efabless/caravel_board/hardware/nucleo/caravel_nucleo/docs/Caravel+Nucleo Board.pdf

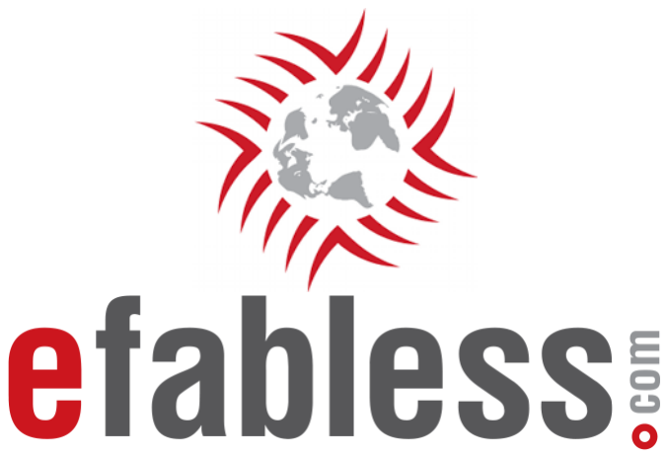
[picture p19: figure]

# Caravel + Nucleo Board

# Specifications

## The board required features:

## - To be physically compatible to act as a hat to the ST Nucleo board using the ST morpho connectors (plug-in). This would provide test setups for characterizing IOs configuration using the Nucleo board

## - Includes programmable power supply on board to test the Caravel chip at a range of power supplies

## - The programmable power supply is programmed with SPI/I

2C

## - It can function as a stand-alone Caravel evaluation board similar to the Caravel V4 evaluation board system

## - The reset could be programmed and not only activated with the push-button

# Programmable Power Supply

## - A programmable power supply is required to test the chip with non-nominal supplies

## - The required ranges are from 1.4V to 2.2V for V1.8 and 3V to 3.6V for V3.3

## - Adjustable dual LDO (MIC2211) is capable of suppling from 1.25V to 5V at 150mA

for Vout1 and at 300mA for Vout2

## - A digital potentiometer (D-POT) MCP4661 could be used with R network to dynamically tune the voltage outputs of the LDO using I

## 2C interface

## - D-POT (10 kΩ device) range to be used in the calculations is from 0 kΩ to 7 kΩ, since its maximum resistance range at temperature corners is 8 kΩ and 12 kΩ

## - MCP4661 has 257 taps

N =

RMAX

RTOT

∗ 256 = 179.2 ≈ 179

[1]: https://www.ti.com/lit/ug/tidu950/tidu950.pdf?ts=1661679201370&ref_url=https%253A%252F%252Fwww.google.com%252F

# Resistance Calculations

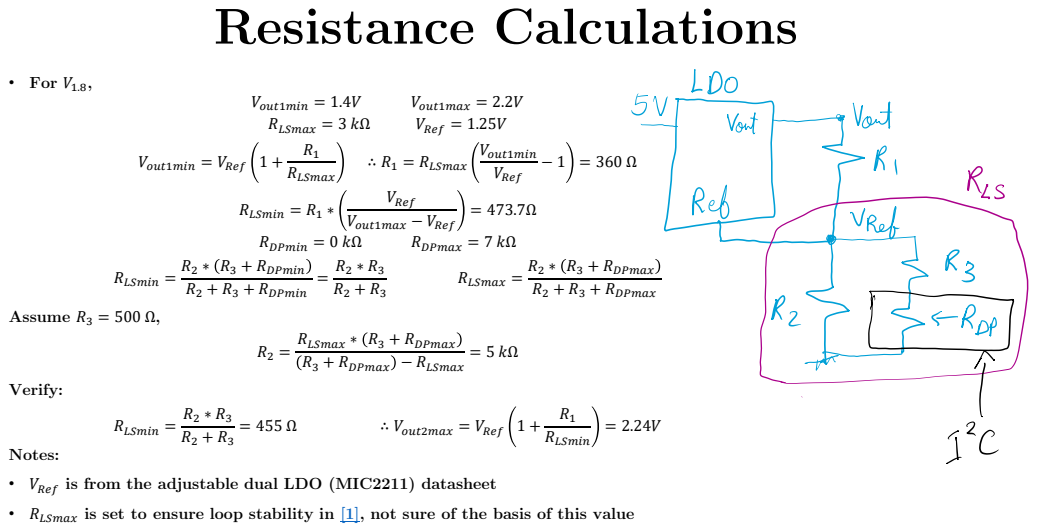
[picture p20: page 4]
• For V1.8,; Vout1min = 1.4V; Vout1max = 2.2V; RLSmax = 3 kΩ; VRef = 1.25V; Vout1min = VRef 1 +; RLSmax; ∴ R1 = RLSmax; Vout1min; VRef; RLSmin = R1 ∗; Vout1max − VRef; RDPmin = 0 kΩ; RDPmax = 7 kΩ; RLSmin =; R2 ∗ R3 + RDPmin; R2 + R3 + RDPmin; RLSmax =; R2 ∗ R3 + RDPmax; R2 + R3 + RDPmax; Assume R3 = 500 Ω,; RLSmax ∗ R3 + RDPmax; R3 + RDPmax − RLSmax; Verify:; ∴ Vout2max = VRef 1 +; RLSmin

Notes:
• VRef is from the adjustable dual LDO (MIC2211) datasheet

• RLSmax is set to ensure loop stability in [1], not sure of the basis of this value

# Resistance Calculations

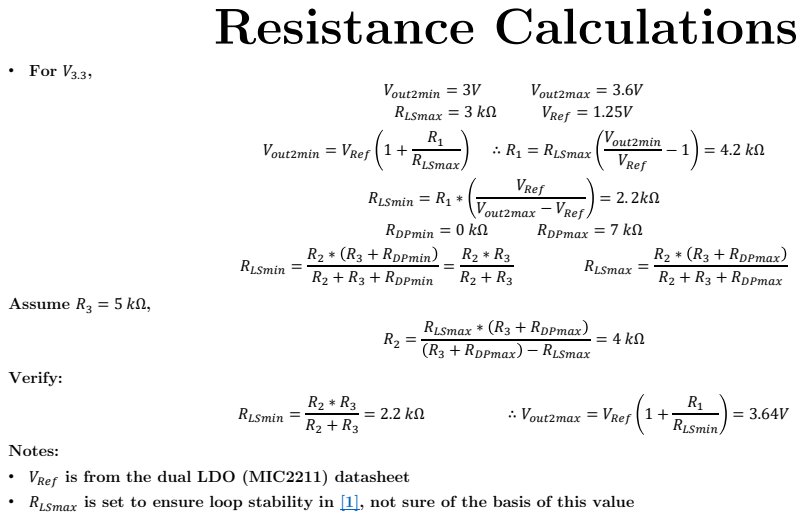
[picture p21: page 5]
• For V3.3,; Vout2min = 3V; Vout2max = 3.6V; RLSmax = 3 kΩ; VRef = 1.25V; Vout2min = VRef 1 +; RLSmax; ∴ R1 = RLSmax; Vout2min; VRef; RLSmin = R1 ∗; Vout2max − VRef; RDPmin = 0 kΩ; RDPmax = 7 kΩ; RLSmin =; R2 ∗ R3 + RDPmin; R2 + R3 + RDPmin; RLSmax =; R2 ∗ R3 + RDPmax; R2 + R3 + RDPmax; Assume R3 = 5 kΩ,; RLSmax ∗ R3 + RDPmax; R3 + RDPmax − RLSmax; Verify:; ∴ Vout2max = VRef 1 +; RLSmin

Notes:
• VRef is from the dual LDO (MIC2211) datasheet
• RLSmax is set to ensure loop stability in [1], not sure of the basis of this value

# Resistors

Output | Resistor | Computed Value | Size 0805 1%
Vout1 | R1 | 360 Ω | 360 Ω
| R2 | 5 kΩ | 4.99 kΩ
| R3 | 500 Ω | 499 Ω
Vout2 | R1 | 4.2 kΩ | 4.22 kΩ
| R2 | 4 kΩ | 4.02 kΩ
| R3 | 5 kΩ | 4.99 kΩ

Note:

- MIC2211 datasheet recommends the resistor values should be between 100kΩ and 500kΩ to prevent compromising the low quiescent current performance. This can’t be achieved with the RLSmax assumption

# Nominal Supplies Code

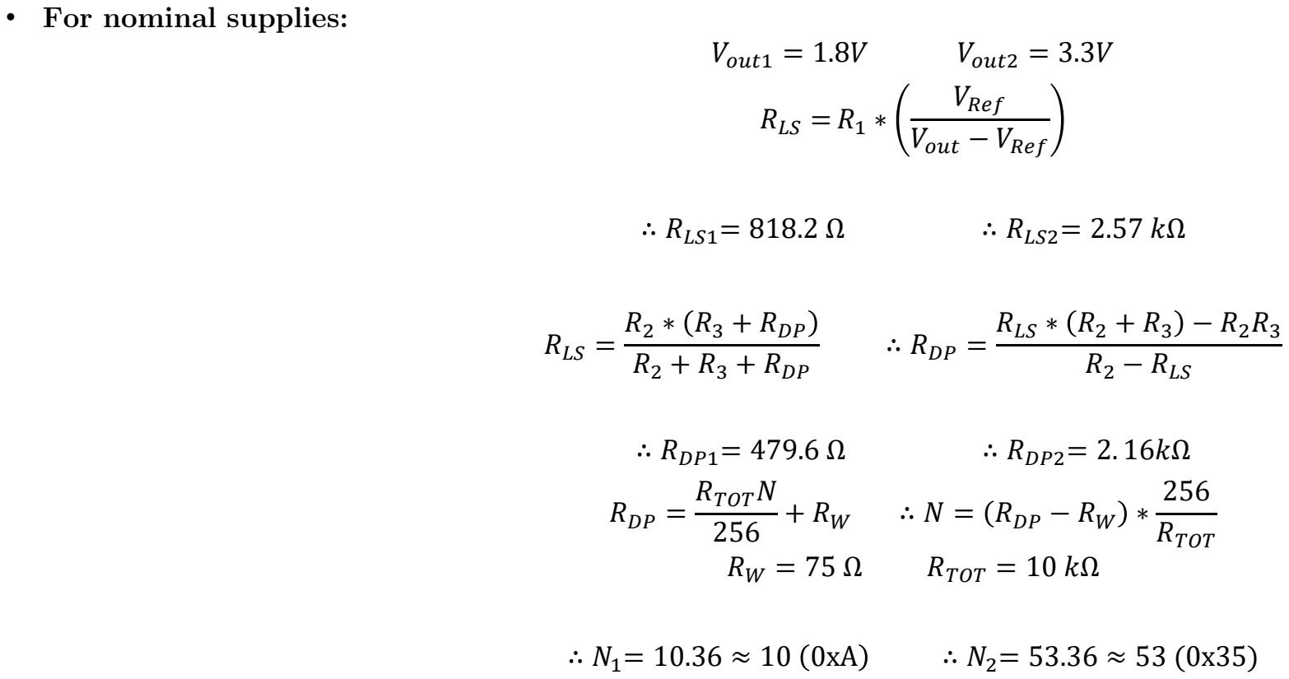
[picture p22: figure]
• For nominal supplies:; Vout1 = 1.8V; Vout2 = 3.3V; RLS = R1 ∗; VRef; Vout − VRef; ∴ RLS1= 818.2 Ω; ∴ RLS2= 2.57 kΩ; RLS =; R2 ∗ R3 + RDP R2 + R3 + RDP; ∴ RDP =; RLS ∗ R2 + R3 − R2R3 R2 − RLS; ∴ RDP1= 479.6 Ω; ∴ RDP2= 2. 16kΩ; RDP =; RTOTN; ∴ N = RDP − RW ∗; RTOT; RTOT = 10 kΩ

∴ N1= 10.36 ≈ 10 0xA ∴ N2= 53.36 ≈ 53 (0x35)

# Supplies Codes

Supply | Value | Code | Notes
Vout1 | 1.4V | 0xB1 | Minimum required supply
| 1.42V | 0x80 | Default code saved in the non-volatile wiper 0 register (0x02)
| 1.6V | 0x1D
| 1.8V | 0xA | Nominal Supply
| 2V | 0x2
| 2.2V | 0x0 | Maximum required supply
Vout2 | 3V | 0xB2 | Minimum required supply
| 3.09V | 0x80 | Default code saved in the non-volatile wiper 1 register (0x03)
| 3.3V | 0x35 | Nominal Supply
| 3.5V | 0xE
| 3.6V | 0x0 | Maximum required supply

Notes:
- Resistance values used are the standard size 0805 1% actual values.
- At reset, the volatile wiper registers (0x00 and 0x01) load the codes saved in the non-volatile wiper registers (0x02 and 0x03)
- The non-volatile wiper registers should be programmed with the desired default supplies

# Caravel Board V4 Block Diagram

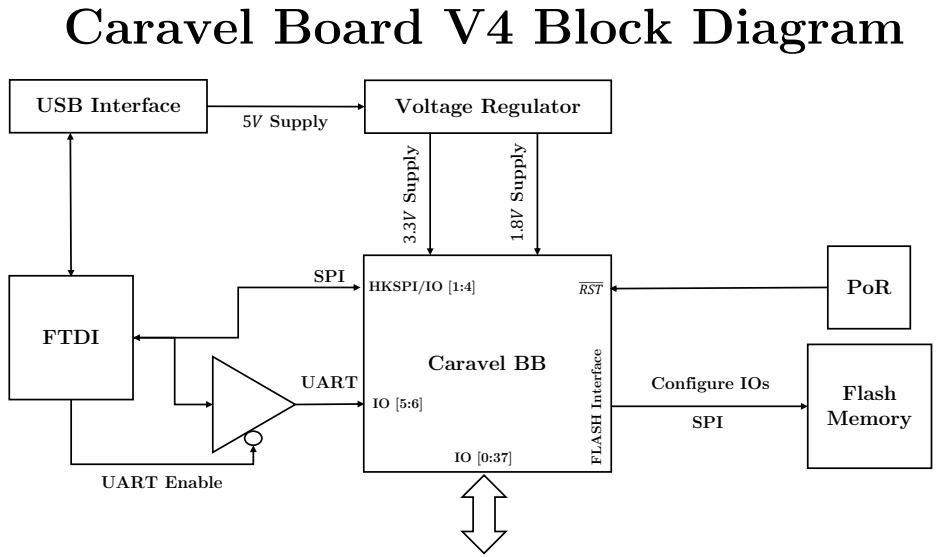
[picture p23: page 9]
Caravel BB; FTDI; USB Interface; HKSPI/IO [1:4]; FLASH Interface; Flash; SPI; Memory; Configure IOs; UART; Voltage Regulator; 5V Supply; 3.3V Supply; 1.8V Supply; UART Enable; RST; PoR

# Nucleo Board:

# NUCLEO144-F746ZG

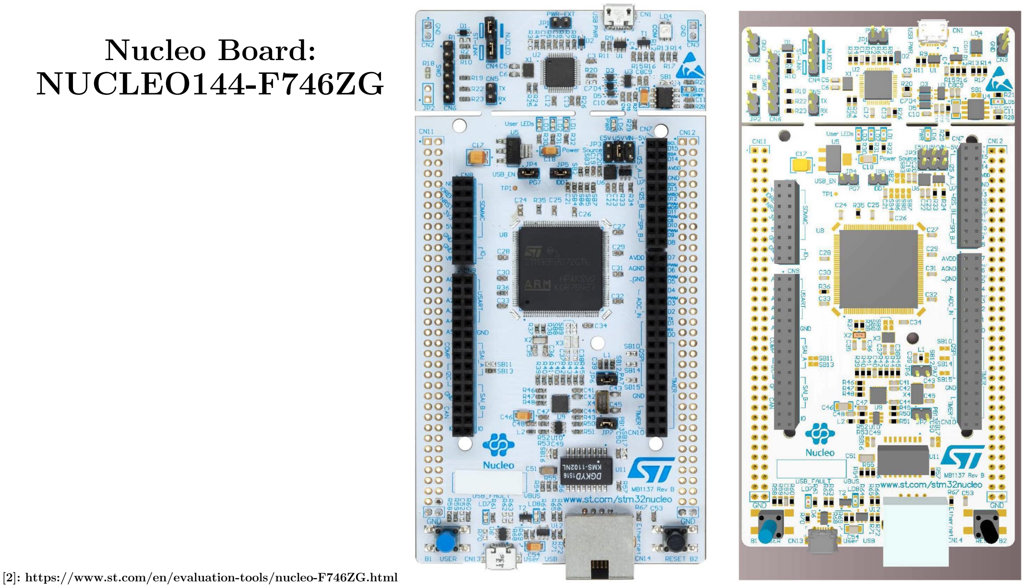
[picture p24: page 10]

[2]: https://www.st.com/en/evaluation-tools/nucleo-F746ZG.html

# Nucleo Board: ST Morpho Connectors

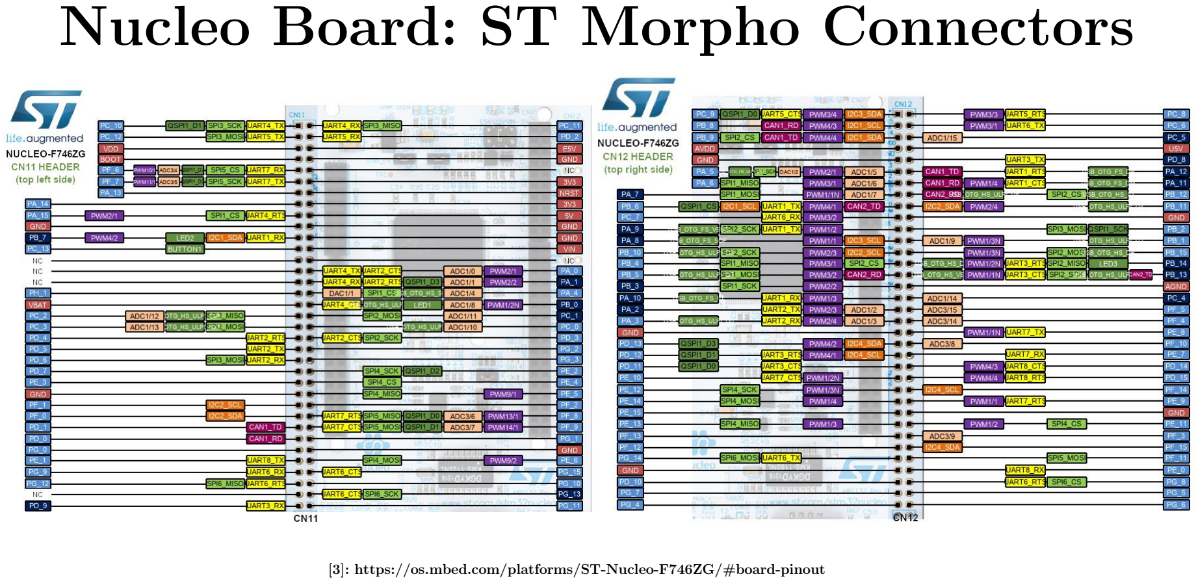
[picture p25: page 11]

[3]: https://os.mbed.com/platforms/ST-Nucleo-F746ZG/#board-pinout

# Nucleo Board: Interface with Caravel

## Nucleo Board: NUCLEO144-F746ZG

## - CN4 jumpers in ST-Link part is used to program STM32 MCU

## - The board is used as a test setup for characterizing the I/O configuration

## - The board has a 3.3V Regulator (Max 500mA)

## - Default clock supply is 8 MHz from ST-Link on PF0/PH0

## - Caravel FLASH/HKSPI interface could be connected to STM32 MCU SPI interfaces

## - Caravel UART interface could be connected to STM32 MCU interface

## - PA13 and PA14 are shared with SWD signals connected to ST-LINK. If ST-LINK part

is not cut, it is not recommended to use them as I/Os.

USB Interface | Nucleo-144 Board

# Caravel + Nucleo Board Block Diagram

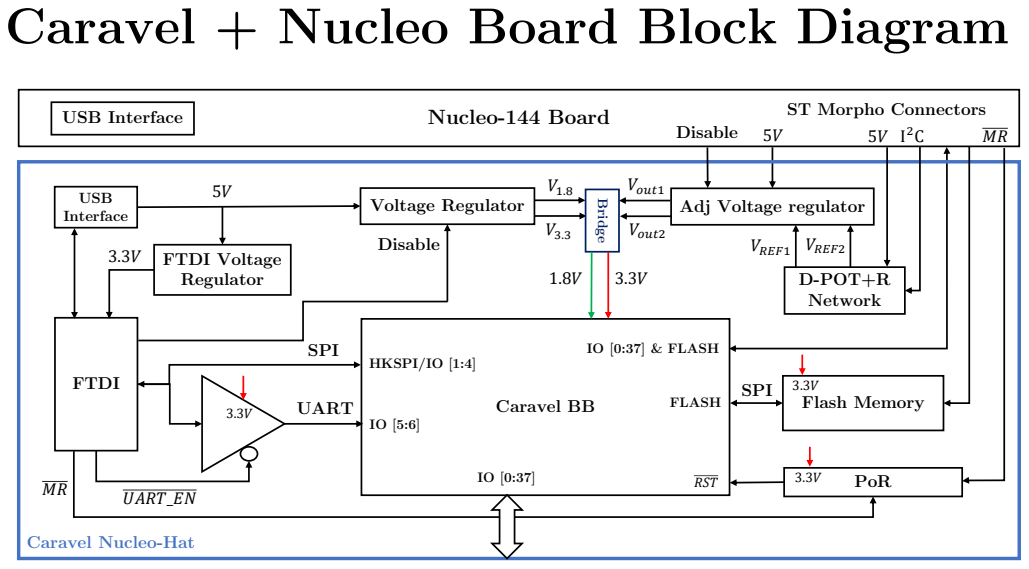
[picture p26: page 13]
Caravel BB; FTDI; USB Interface; HKSPI/IO [1:4]; FLASH; PoR; SPI; UART; Voltage Regulator; UART_EN; Flash Memory; RST IO [0:37]; D-POT+R Network; VREF1; VREF2; IO [0:37] & FLASH; FTDI Voltage Regulator; Vout2; Bridge; Vout1; Disable

ST Morpho Connectors

Adj Voltage regulator

Caravel Nucleo-Hat

# Caravel + Nucleo Board Schematic

## Notes: - A timer could be used to supply the clock to caravel as a PWM signal for

## example, TIM3_CH2 on PB5

- Caravel FLASH connected to SPI4 (PE2 PE4: PE6) - Caravel HKSPI to SPI5 (PF6: PF9) - Caravel UART connected to UART8 (PE0: PE1) - The manual reset MR is connected to PC12 - Caravel remaining 32 I/Os connected to ST Morpho pins that have no conflict on them and support the order of the breakout board pinout - The supplies are connected to external pin header J10 with gpio, xclk and RST - Nucleo Board: NUCLEO144-F746ZG - Cravel Breakout Board: V2 breakout board with Caravel WCSP chip - J4 connector is available to support connecting a serial display easily - J7 connector is available to support testing the flash memory pins

# Caravel + Nucleo Board Schematic

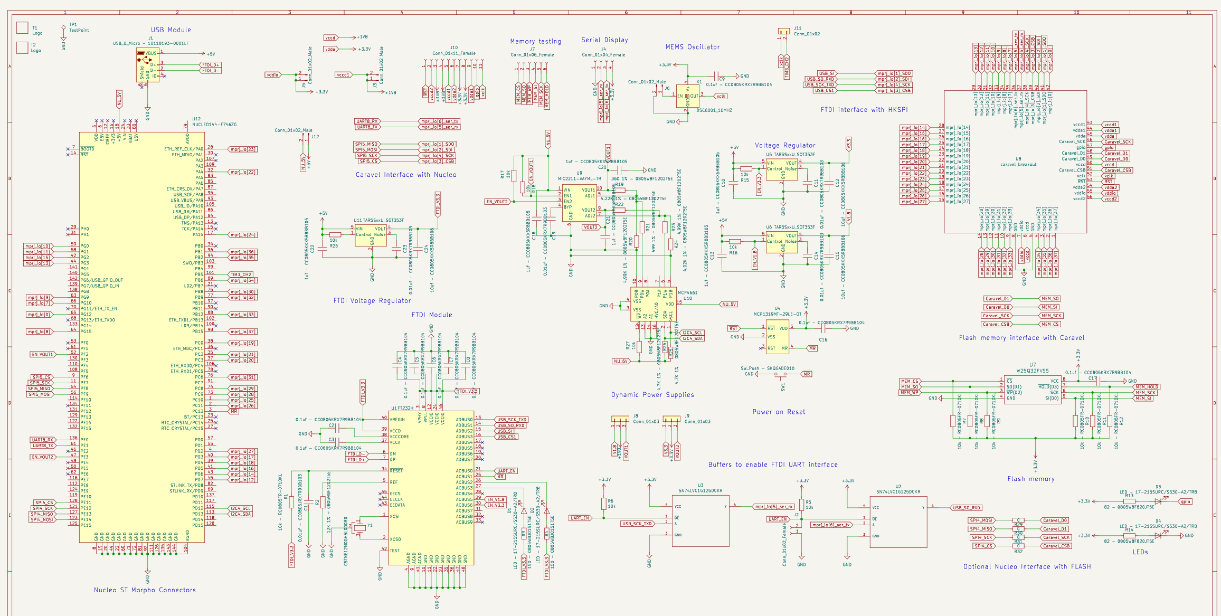
[picture p27: page 15]

# Caravel + Nucleo Board Components

Component | Reference | Description
MCP1319MT-29LE-OT | U4 | Power on Reset (PoR) circuit with internal pull-up resistors
TAR5SxxU_SOT353F | U5 & U6 & U11 | Fixed voltage regulators that provide 1.8V and 3.3V. The footprint is the same for a wide range of LDO devices from 1.5V to 5V which allows installing 1.6V LDO in place of the 1.8V for example
MIC2211-AAYML-TR | U9 | Adjustable voltage regulator that is used to provide a programmable power supply by adjusting the resistors of each output. It is supplied with 5V from the Nucelo Board
MCP4661 | U10 | Digital Potentiometer that is programmed using I 2C interface to provide desired resistive loads for U9 to achieve the programmable power supply. It also has non-volatile memory which allows stand-alone operation after saving the desired values. It is supplied with 5V from the Nucelo Board
NUCLEO144-F429ZI | U12 | The Nucleo-144-F429ZI board ST Morpho connectors that has 144 pins interfacing with STM32 MCU

# Caravel + Nucleo Pinout

Caravel BB Pin | ST Morpho Pin
1: io[37] | 98: PB15
2: io[36] | 96: PB1
3: io[35] | 94: PB2
4: io[34] | 89: PB6
5: GND | GND
6: vccd | -
7: vddio | -
8: GND | GND
9: io[33] | 88: PB12
10: io[32] | 77: PB9
11: io[31] | 76: PC6
12: io[30] | 75: PB8
13: io[29] | 74: PC8
14: io[28] | 73: PC9
Caravel BB Pin | ST Morpho Pin
15: io[27] | 4: PD2
16: io[26] | 2: PC11
17: io[25] | 1: PC10
18: io[24] | 17: PA15
19: io[23] | 28: PA0
20: io[22] | 32: PA4
21: io[21] | 35: PC2
22: io[20] | 37: PC3
23: io[19] | 38: PC0
24: io[18] | 39: PD4
25: io[17] | 40: PD3
26: io[16] | 41: PD5
27: io[15] | 42: PG2
28: io[14] | 43: PD6

# Caravel + Nucleo Pinout

Caravel BB Pin | ST Morpho Pin
29: io[13] | 44: PG3
30: io[12] | 45: PD7
31: io[11] | 58: PG1
32: io[10] | 59: PG0
33: io[9] | 63: PG9
34: io[8] | 64: PG15
35: io[7] | 66: PG10
36: io[6]/tx | 136:PE0
37: io[5]/rx | 61: PE1
38: io[4]/SCK | 11: PF7
39: io[3]/CSB | 9: PF6
40: io[2]/SDI | 56: PF9
41: io[1]/SDO | 54: PF8
42: io[0] | 65: PG12
Caravel BB Pin | ST Morpho Pin
43: vccd1 | -
44: vdda1 | -
45: vdda | -
46: Caravel/SCK | 121: PE12
47: gpio | -
48: Caravel/D1 | 127: PE13
49: Caravel/D0 | 123: PE14
50: vccd | -
51: Caravel/CSB | 128: PE11
52: xclk | -
53: NRST | -
54: vdda2 | -
55: vddio | -
56: vccd2 | -

# Caravel + Nucleo Board Power Supply

Mode | Main Power | Power Domains | Jumper State | Components | Notes
HAT | Nucleo Board 5V | U9: 3.3V | J9: 2 to 3 (HAT) | Caravel, FLASH, buffers, X1 | Programmable
| | U9: 1.8V | J8: 2 to 3 (HAT) | Caravel | Programmable
| | U5: 3.3V | J9: 2 to 1 (MAIN) | Caravel, FLASH, buffers, X1 | Fixed
| | U9: 3.3V | J9: 2 to 3 (HAT) J12: 1 to 2 (NU_5V) | Caravel, FLASH, buffers, X1 | Fixed: DVS saved setting
| | U11: 3.3V | − | FTDI
| | U6: 1.8V | J8: 2 to 1 (MAIN) | Caravel | Fixed
| | U9: 1.8V | J9: 2 to 3 (HAT) J12: 1 to 2 (NU_5V) | Caravel | Fixed: DVS saved setting
MAIN | USB Module 5V
- Both modes support supplying 3.3V and 1.8V externally through J10 pins and leaving J8 and J9 floating

# Caravel + Nucleo Board Reset

Mode | Reset Mechanism | Pin Activated
HAT | SW1 Push-Button | PoR: MR
| Nucleo Program configures PC12 | PoR: MR
| Externally through J10 | RESET
MAIN | SW1 Push-Button | PoR: MR
| FTDI Program configures ACBUS1 | PoR: MR
| Externally through J10 | RESET

# Caravel + Nucleo Board Clock

Mode | Clock Source | Frequency | Jumper State
HAT | MEMS Oscillator X1 | 10 MHz | −
| Nucleo Program configures PB5 | Custom | J6: 1 to 2 J11: 1 to 2 (TIM3_PWM)
| Externally through J10: XCLK | Custom | J6: 1 to 2
MAIN | MEMS Oscillator X1 | 10 MHz | −
| Externally through J10: XCLK | Custom | J6: 1 to 2

# Caravel + Nucleo Board Data

Mode | Interface | Components | Jumper State
HAT | SPI
| UART
MAIN | SPI
| UART

# Caravel + Nucleo Board Modes

### MAIN mode:

- The board is programmed through the USB module communicating with the FTDI.
- The 5V supply is provided from the USB module to power the fixed voltage supplies (U5 and U6) which in turn power up the other system components except for the programmable power supply.
- J8 and J9 are set to connect pin 2 to pin 1 (MAIN).
- J8 and J9 are left floating if the 3.3V and 1.8V are to be supplied externally.
- J11 is left with no connections as the clock is driven from X1 with 10MHz frequency.
- Other frequencies could be supported by disabling X1 through J6 and driving the clock externally.
- To reset the board, use SW1 button or FTDI ACBUS1.

### - The fixed LDOs enables could be programmed through FTDI ACBUS5 (1.8V) and ACBUS6 (3.3V)

- By default, the FTDI interface with the Caravel HKSPI. To switch to the UART interface of

### Caravel, set UART_EN to 0 either using J2 or the FTDI ACBUS0

- To use the programmable power supplies saved setting instead of the fixed voltage supplies:
1. connect pin 2 to pin 3 on J8 and J9 (HAT).
2. connect J12 pins to provide the 5V supply to U9 and U10 (short 5V with NU_5V).

# Caravel + Nucleo Board Modes

## HAT mode:

- The board acts as a hat for Nucleo-144 test setup.

## - The 5V supply is provided from the Nucleo board to power the programmable power supply (U9 and U10) which in turn power up the other system components except for

the fixed power supply and the FTDI module.

## - U10 is programmed from the Nucleo using I

## 2C 4 on pins PD12: PD13 to provide the desired supplies

- J8 and J9 are set to connect pin 2 to pin 3 (HAT).

## - The clock could be programmed from the Nucleo as a PWM signal generated from Timer 3 on PB5. J11 is set in this case

- J6 is set to disable X1 in the case of driving the clock with J11.
- To reset the board, use the Nucleo to program PC12 or SW1 button.

## - The programmable LDOs enables could be programmed from the Nucleo on pins PF2

## (1.8V) and PE3 (3.3V)

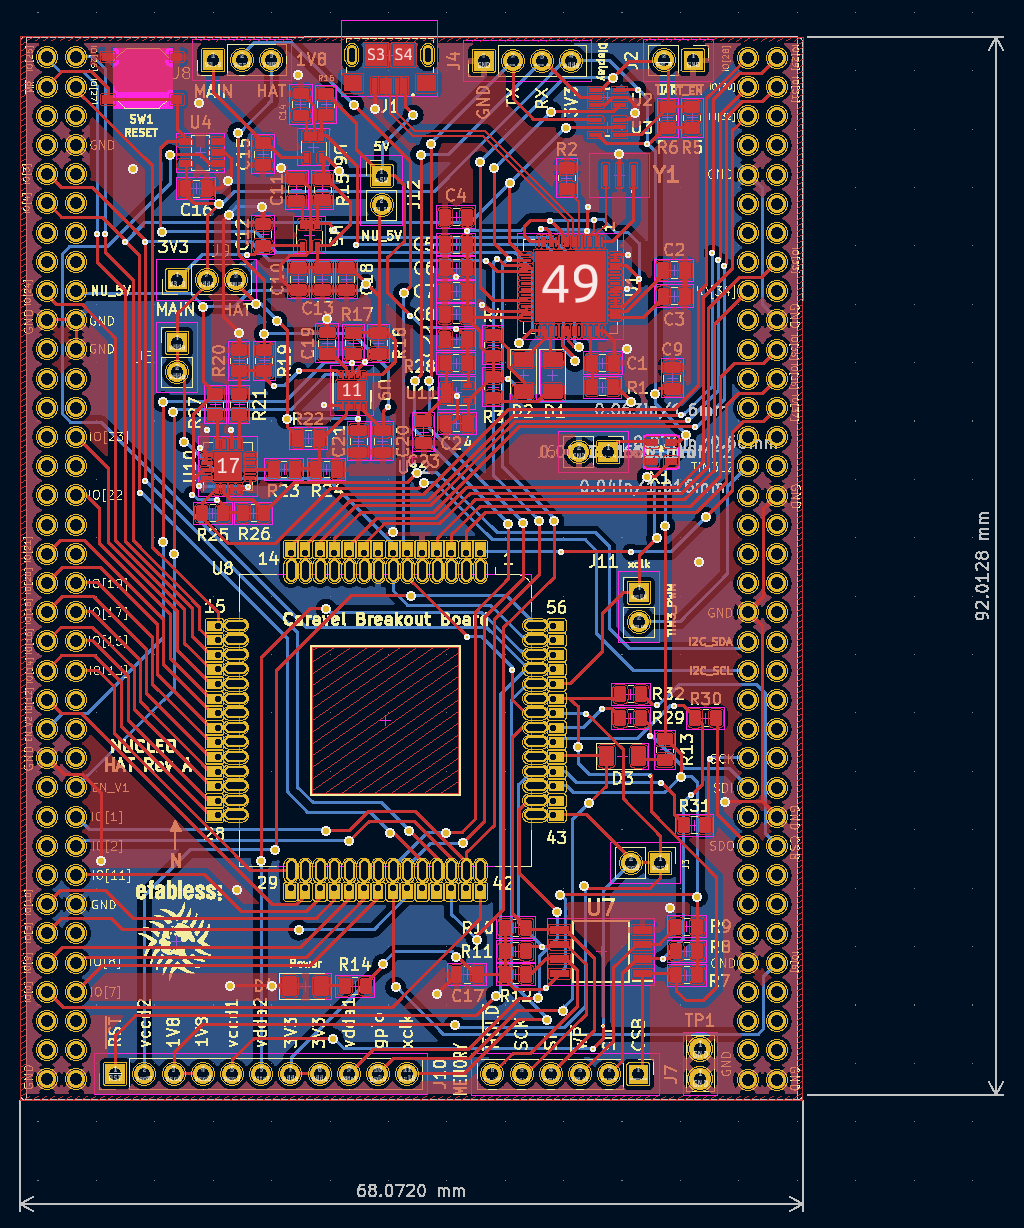
[picture p28: figure]

# Caravel + Nucleo Board PCB

## Dimensions:

## 68.072 ∗ 92.0128 mm²
