efabless/caravel_board/firmware/mpw2-5/nucleo/docs/hat_w_headers.jpg

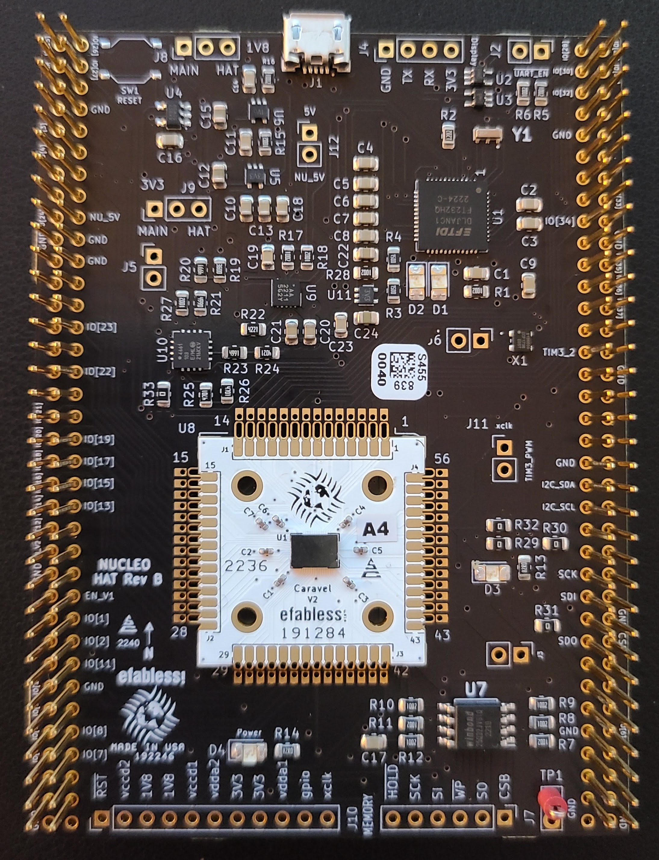
firmware/mpw2-5/nucleo/docs/hat_w_headers.jpg
