efabless/caravel_board/firmware/mpw2-5/nucleo/docs/nucleo_board.jpeg

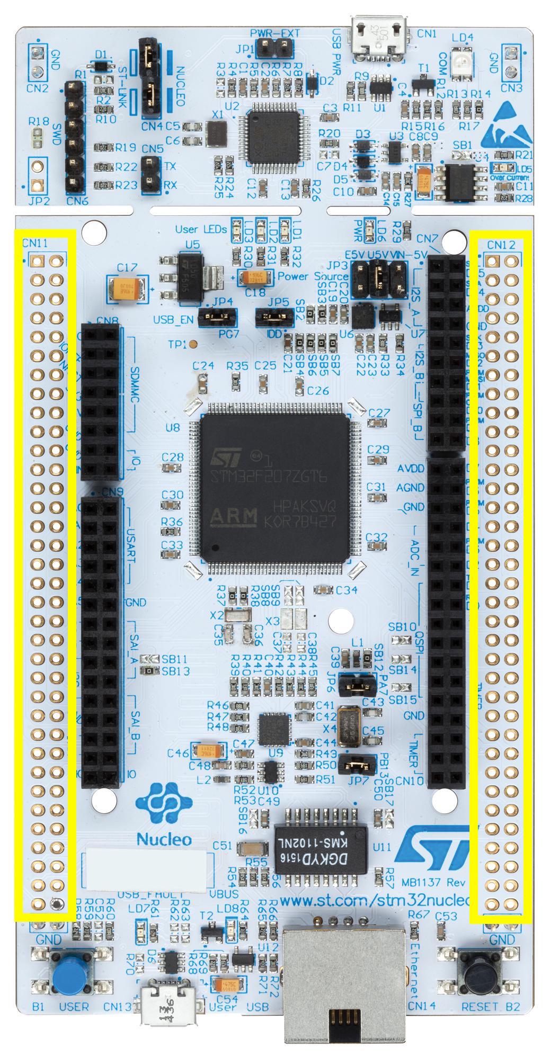
firmware/mpw2-5/nucleo/docs/nucleo_board.jpeg
