efabless/caravel_board/firmware/mpw2-5/nucleo/docs/nucleo_w_headers.jpg

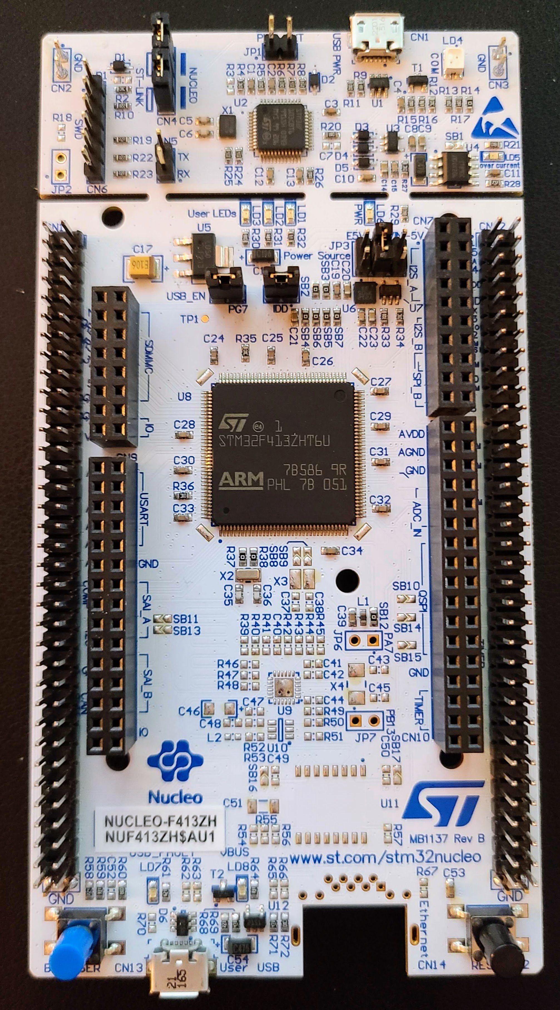
firmware/mpw2-5/nucleo/docs/nucleo_w_headers.jpg
