efabless/caravel_board/hardware/breakout/caravel-M.2-card-QFN/caravel-M.2-card-QFN-back.png

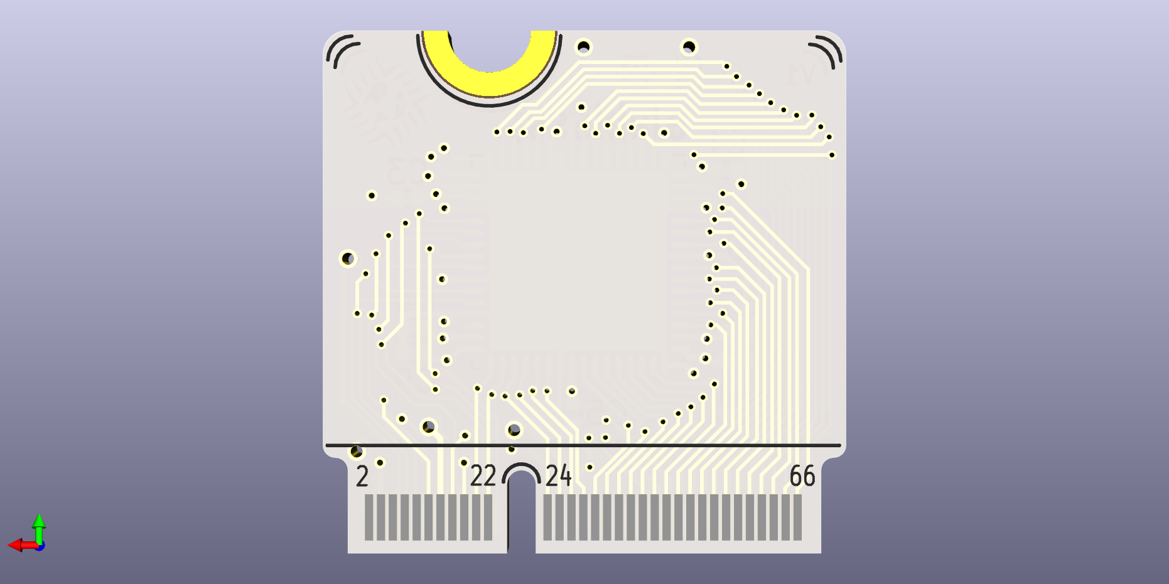
hardware/breakout/caravel-M.2-card-QFN/caravel-M.2-card-QFN-back.png
