efabless/caravel_board/hardware/breakout/caravel-M.2-card-QFN/caravel-M.2-card-QFN-front.png

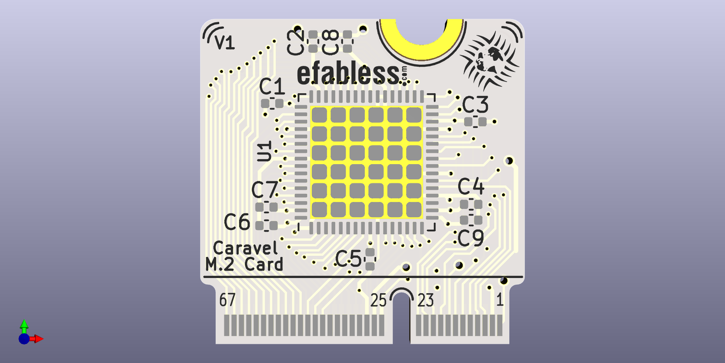
hardware/breakout/caravel-M.2-card-QFN/caravel-M.2-card-QFN-front.png
