efabless/caravel_board/hardware/breakout/caravel-M.2-card-WCSP/caravel-M.2-card-WCSP-back.png

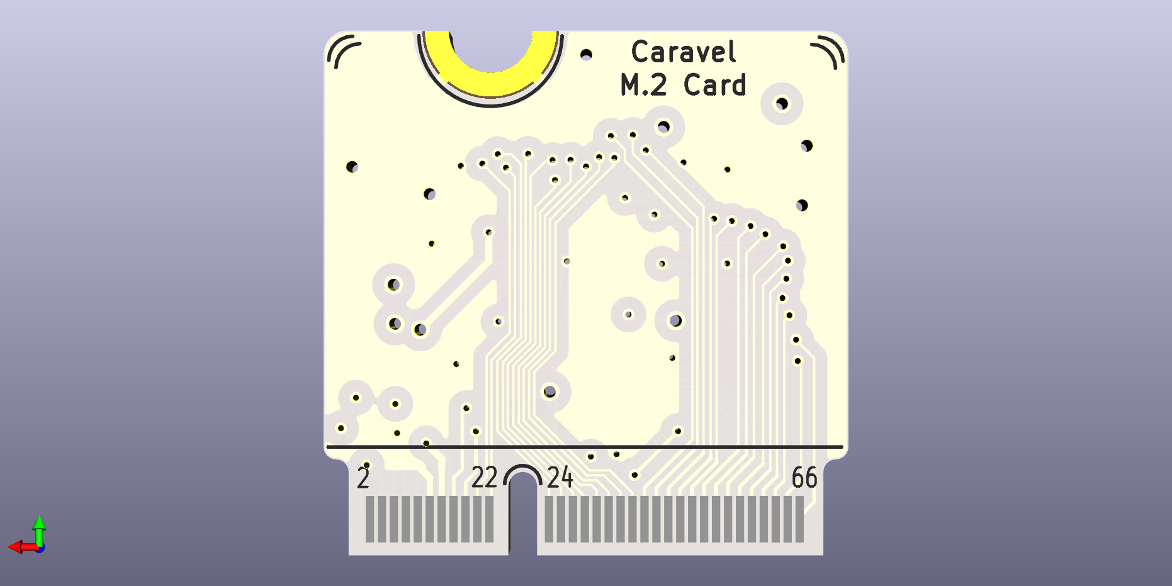
hardware/breakout/caravel-M.2-card-WCSP/caravel-M.2-card-WCSP-back.png
