efabless/caravel_board/hardware/breakout/caravel_breakout_QFN/caravel_breakout_QFN_back.png

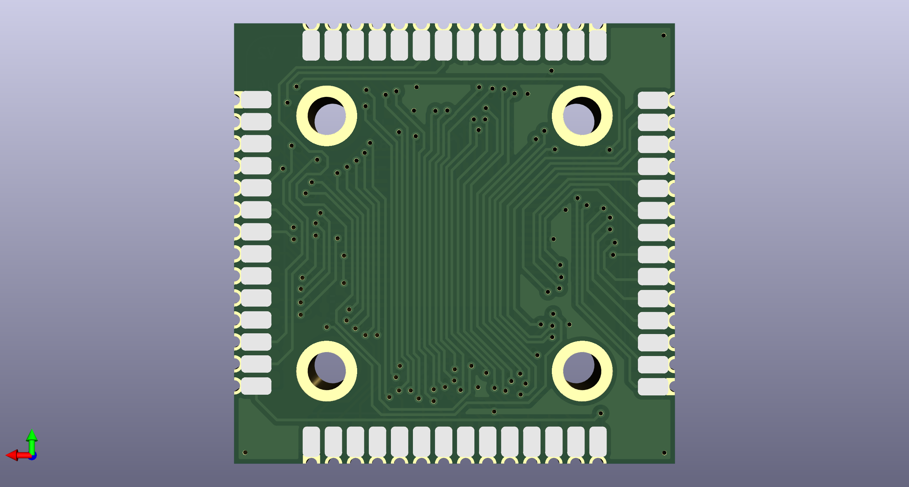
hardware/breakout/caravel_breakout_QFN/caravel_breakout_QFN_back.png
