efabless/caravel_board/hardware/breakout/caravel_breakout_QFN/caravel_breakout_QFN_front.png

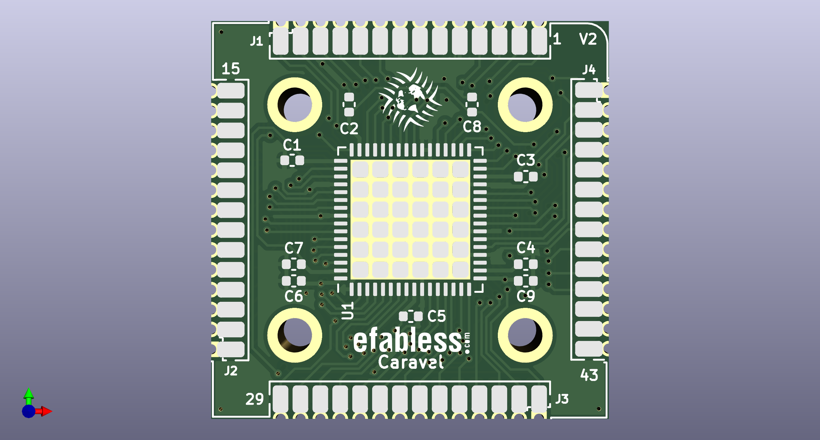
hardware/breakout/caravel_breakout_QFN/caravel_breakout_QFN_front.png
