efabless/caravel_board/hardware/breakout/caravel_breakout_v2/Caravel_breakout_v2_front.png

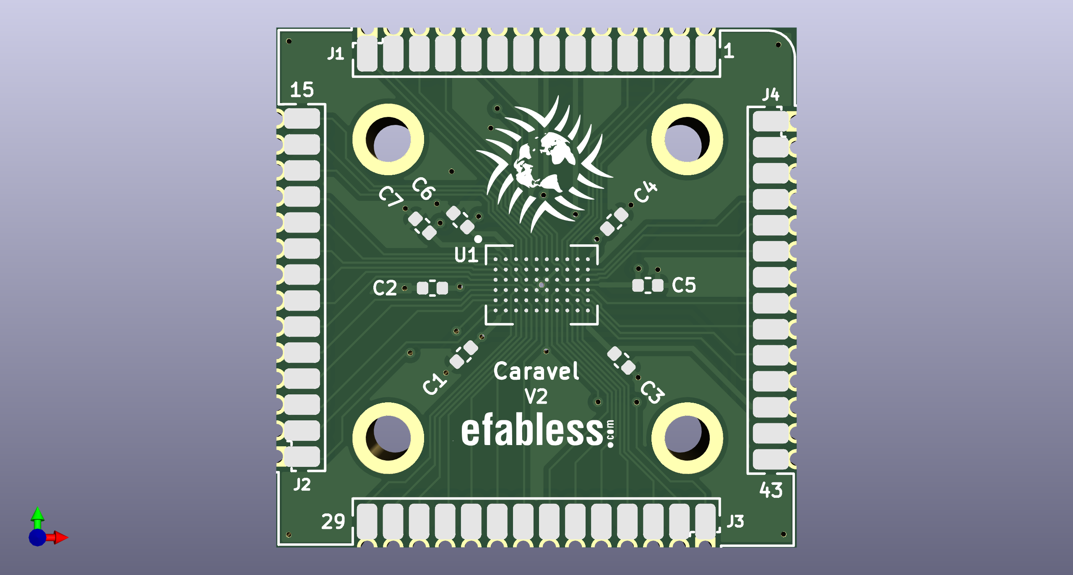
hardware/breakout/caravel_breakout_v2/Caravel_breakout_v2_front.png
