efabless/caravel_board/hardware/breakout/caravel_daughter/Caravel_daughter.jpg

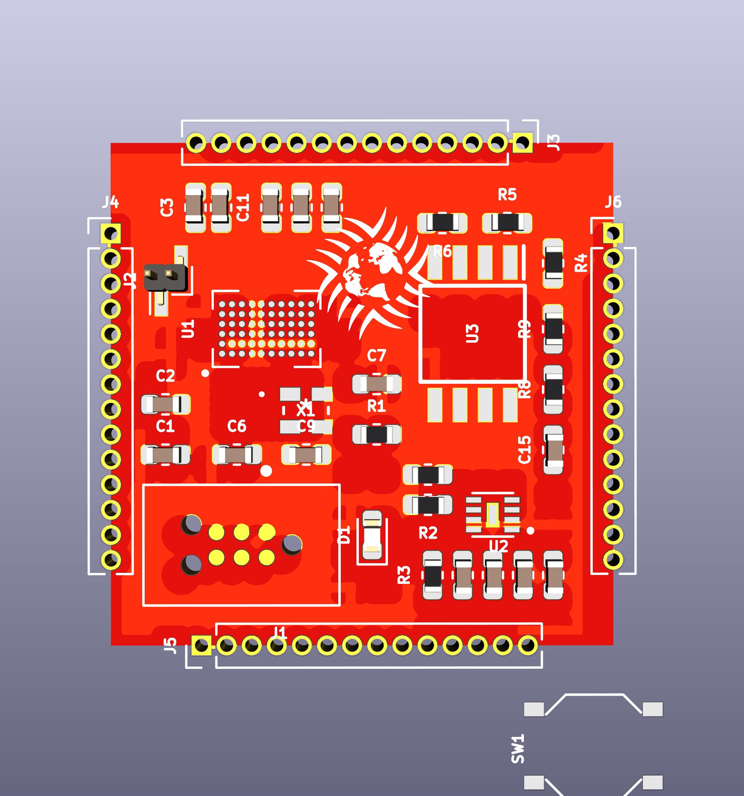
hardware/breakout/caravel_daughter/Caravel_daughter.jpg
