efabless/caravel_board/hardware/development/caravel-dev-gf180-v6-M.2/caravel-5V-dev-v6-M.2-front.png

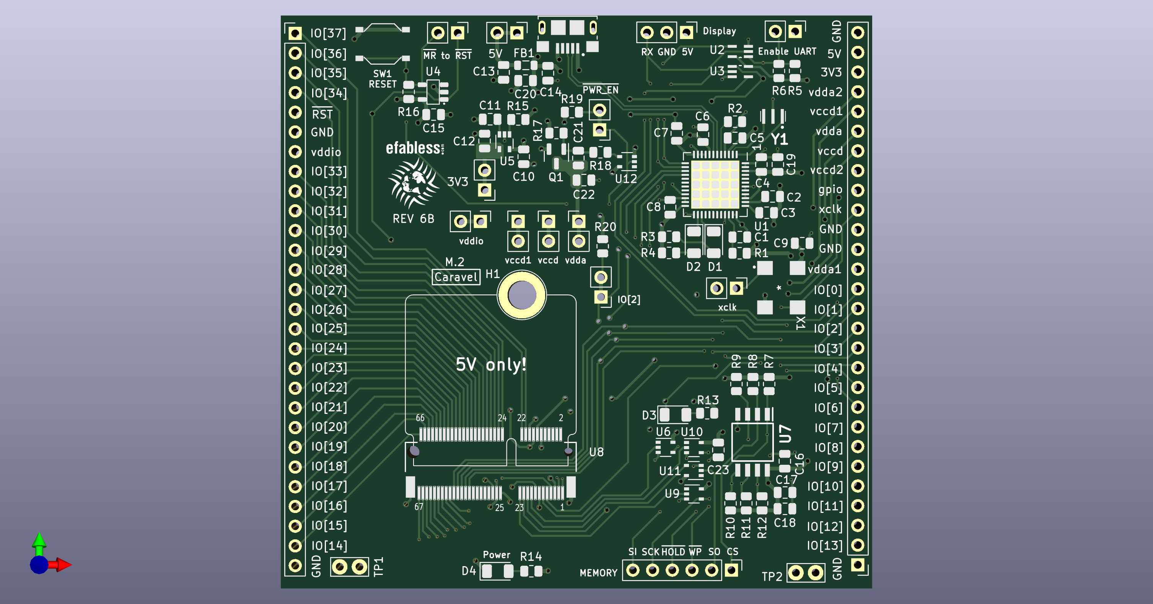
hardware/development/caravel-dev-gf180-v6-M.2/caravel-5V-dev-v6-M.2-front.png
