efabless/caravel_board/hardware/development/caravel-dev-v5-M.2/caravel-dev-v5-M.2-back.png

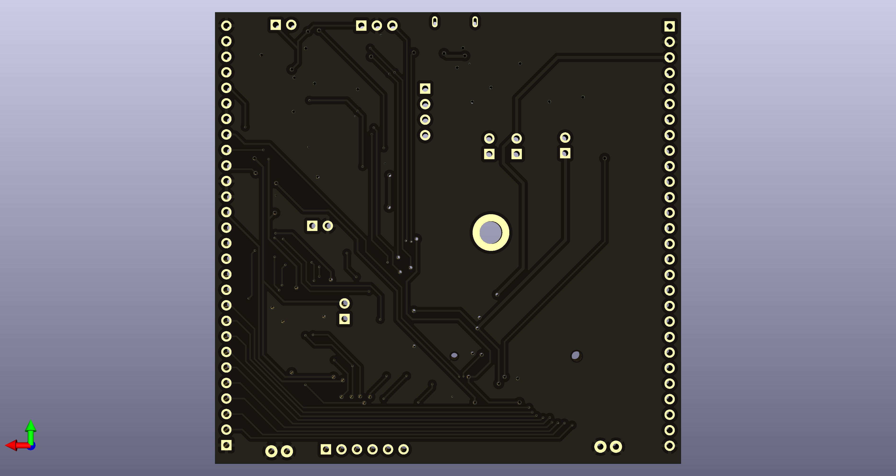
hardware/development/caravel-dev-v5-M.2/caravel-dev-v5-M.2-back.png
