efabless/caravel_board/hardware/development/caravel_pcb_v2/caravel_back.jpg

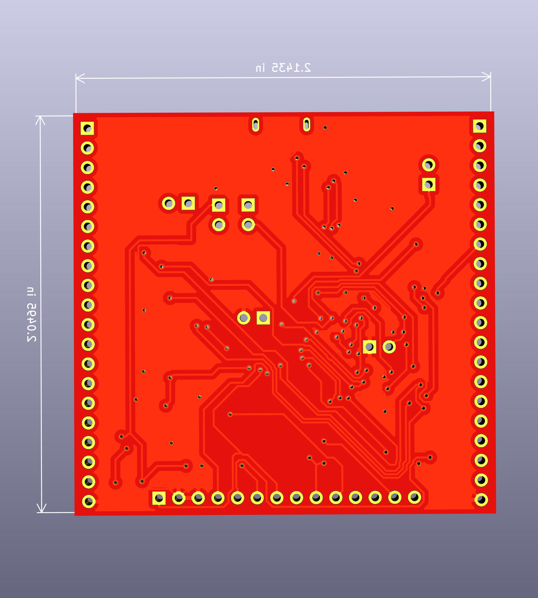
hardware/development/caravel_pcb_v2/caravel_back.jpg
