efabless/caravel_board/hardware/development/caravel_pcb_v2/caravel_front.png

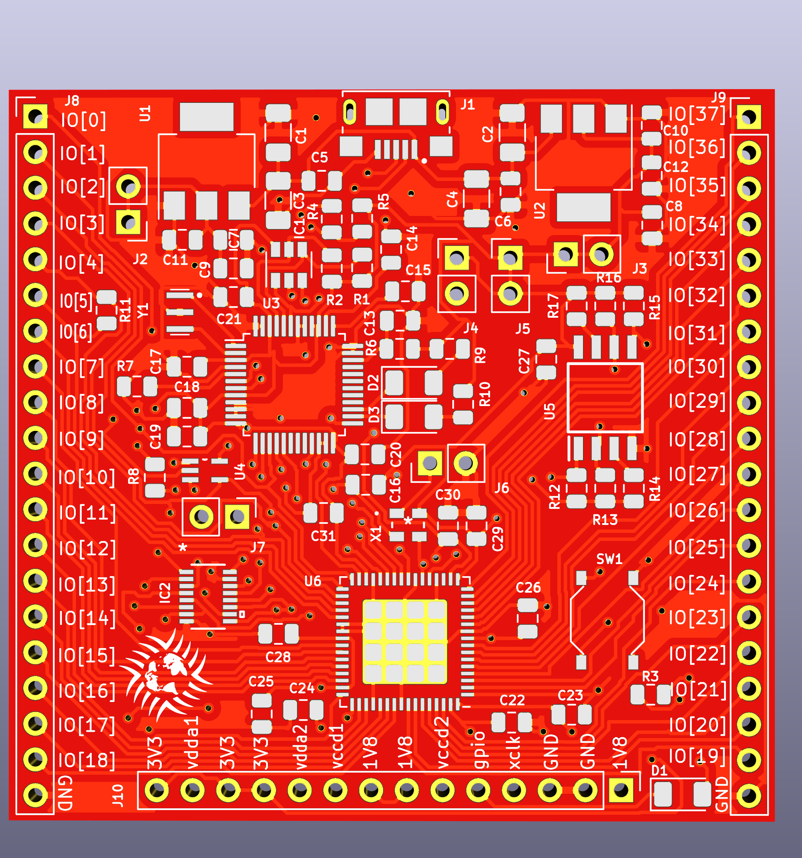
hardware/development/caravel_pcb_v2/caravel_front.png
