efabless/caravel_board/hardware/development/clear-dev-v1/clear-dev-v1-Front.png

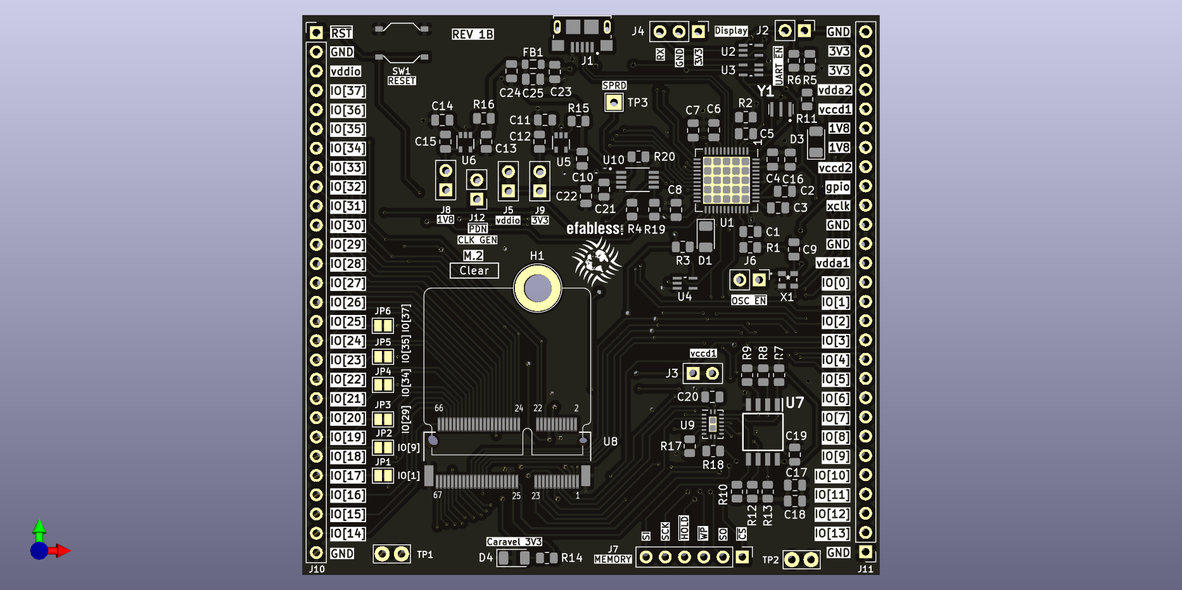
hardware/development/clear-dev-v1/clear-dev-v1-Front.png
