efabless/caravel_board/hardware/nucleo/caravel-Nucleo-v2-M.2/caravel-Nucleo-v2-M.2-front.png

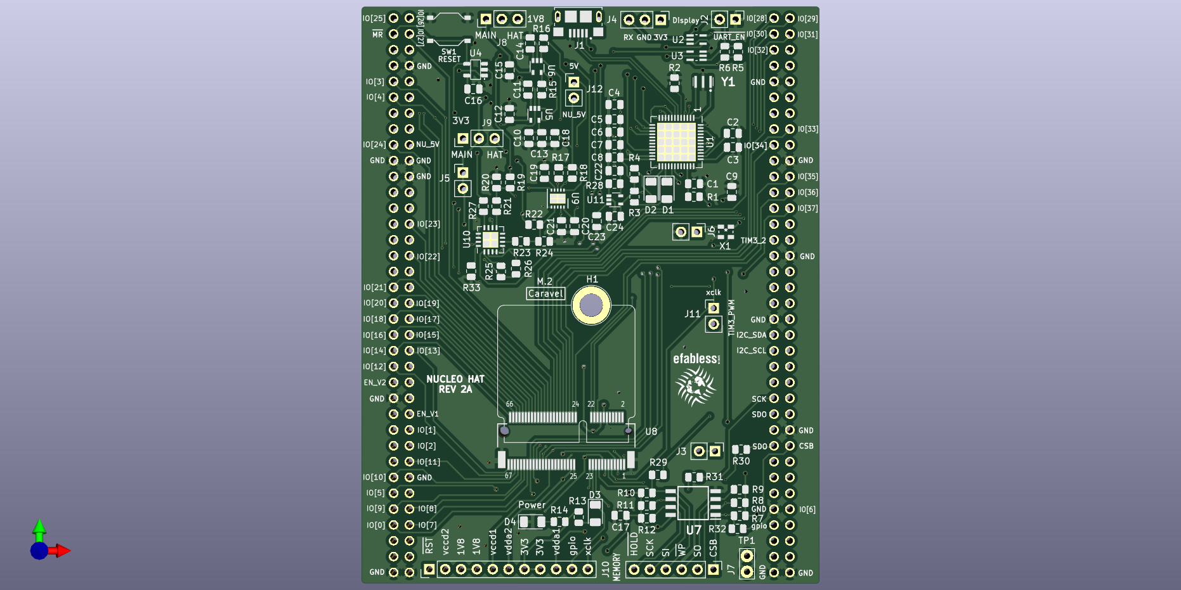
hardware/nucleo/caravel-Nucleo-v2-M.2/caravel-Nucleo-v2-M.2-front.png
