efabless/caravel_board/hardware/nucleo/caravel_nucleo/caravel_Nucleo_front.png

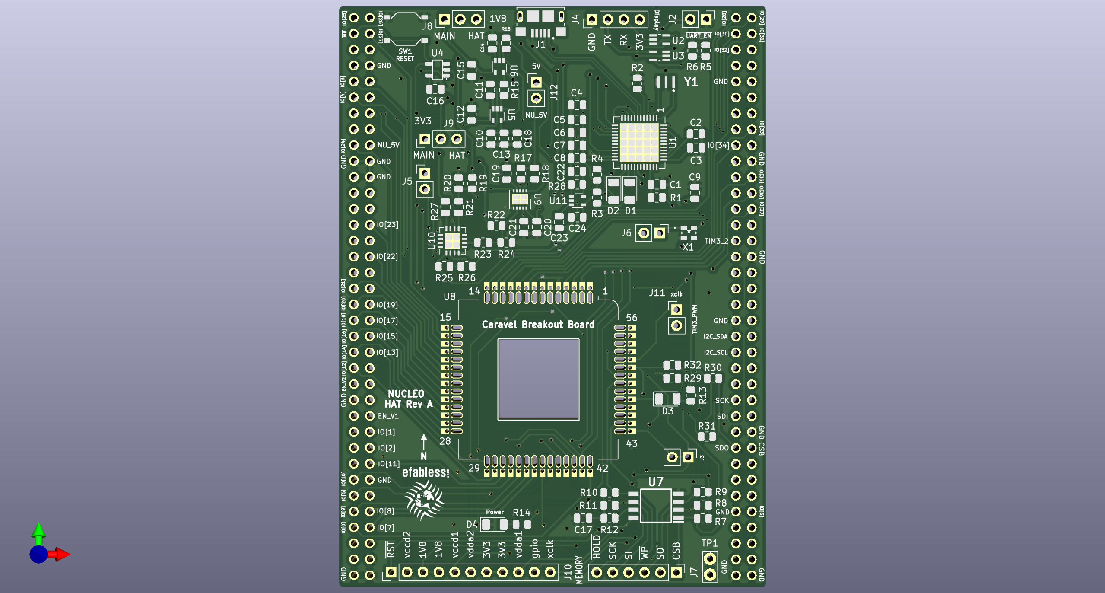
hardware/nucleo/caravel_nucleo/caravel_Nucleo_front.png
