efabless/caravel_board/hardware/nucleo/caravel_nucleo/caravel_nucleo_isoview.png

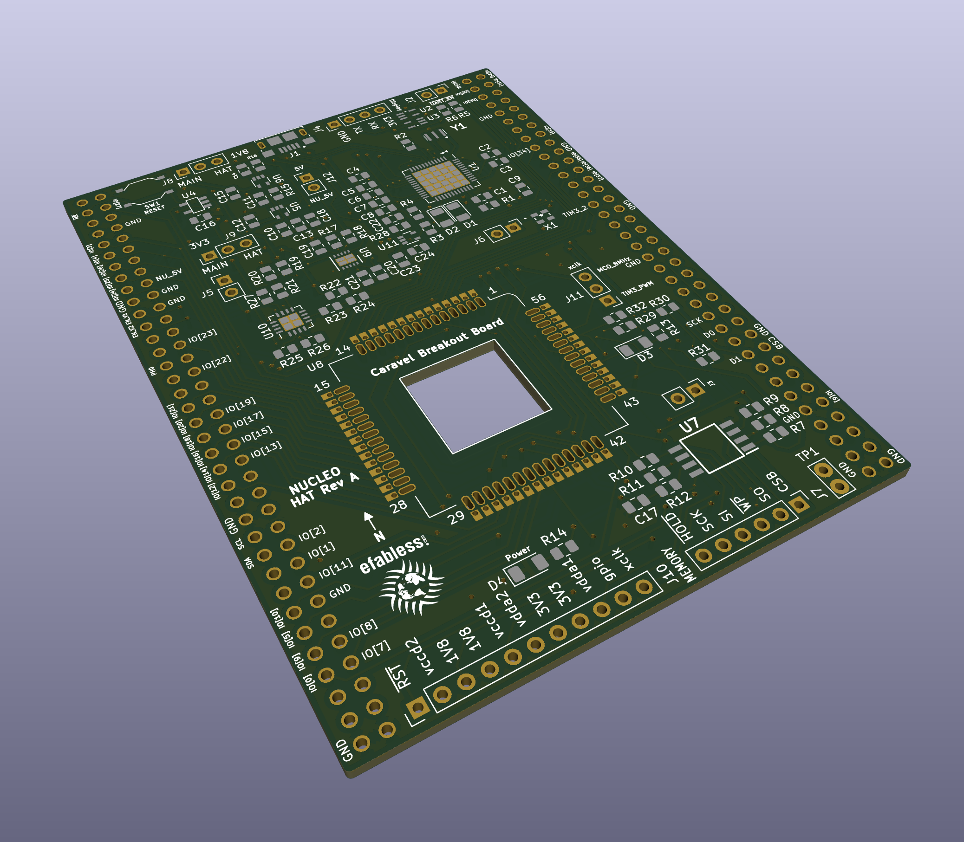
hardware/nucleo/caravel_nucleo/caravel_nucleo_isoview.png
