efabless/caravel_board/hardware/breakout/caravel_breakout_v2/Caravel_breakout_v2.xls

Designator | Qty | Value | Part number | Vendor
C1, C2, C3, C4, C5, C6, C7, | 7 | 0.1uf | CC0402KRX7R9BB104 | DK
J1, J2, J3, J4, | 4 | DNI
U1, | 1 | Caravel |  | Customer provided
