efabless/caravel_board/hardware/test_fixture/caravel_FTDI_QFN_test_socket/caravel_FTDI_QFN_test_socket.xlsx

Designators | QTY | Value | Part Number | Supplier
U1 | 1 |  | FT232HQ | not stocked
U2, U3 | 2 |  | SN74LVC1G125DCKT (https://eu.mouser.com/ProductDetail/Texas-Instruments/SN74LVC1G125DCKT?qs=pajgIaoyDUhOMyeC25ASaQ%3D%3D) | Mouser | alternative part
U4 | 1 |  | AZ1117CH-1.8TRG1 (https://www.digikey.com/en/products/detail/diodes-incorporated/AZ1117CH-1-8TRG1/4470983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) | DK
U5 | 1 |  | AZ1117IH-3.3TRG1 (https://www.digikey.com/en/products/detail/diodes-incorporated/AZ1117IH-3-3TRG1/5699672) | DK | alternative part | LDI1117-3.3H (https://www.digikey.com/en/products/detail/diotec-semiconductor/LDI1117-3-3H/13154408)
U6 | 1 |  | QFN64-(9x9)-0.5-CL Test Socket with QFN Caravel | EF
U7 | 1 |  | W25Q32JVSSIQ (https://www.digikey.com/en/products/detail/winbond-electronics/W25Q32JVSSIQ/5803981) | DK
D1, D2, D3, D4 | 4 |  | LTST-C230KRKT (https://www.digikey.com/en/products/detail/liteon/LTST-C230KRKT/386857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) | DK
C9-C12 | 4 | 100u | GMC31X5R107M6R3NT (https://www.digikey.com/en/products/detail/cal-chip-electronics-inc/GMC31X5R107M6R3NT/12140450) | DK
C13, C14, C18, C19 | 4 | 10u | CC0805KKX5R8BB106 (https://www.digikey.com/en/products/detail/yageo/CC0805KKX5R8BB106/5195275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) | DK
C16, C17 | 2 | 22u | CC0805MKX5R5BB226 (https://www.digikey.com/en/products/detail/yageo/CC0805MKX5R5BB226/2833629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) | DK
C20, C21 | 2 | 1u | CC0805KKX7R8BB105 (https://www.digikey.com/en/products/detail/yageo/CC0805KKX7R8BB105/2833621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) | DK
C2-C8, C15, C22-C31 | 18 | 0.1u | CC0805KRX7R9BB104 (https://www.digikey.com/en/products/detail/yageo/CC0805KRX7R9BB104/302874) | DK
C1 | 1 | 0.01u | CC0805JRX7R9BB103 (https://www.digikey.com/en/products/detail/yageo/CC0805JRX7R9BB103/5195264) | DK
R1, R5-R10, R12, R13 | 9 | 10K | RC0805FR-0710KL (https://www.digikey.com/en/products/detail/yageo/RC0805FR-0710KL/727535) | DK
R2 | 1 | 12K, 1% | RMCF0805FT12K0 (https://www.digikey.com/en/products/detail/stackpole-electronics-inc/RMCF0805FT12K0/1760674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) | DK
R3, R4 | 2 | 150 | RNCP0805FTD150R (https://www.digikey.com/en/products/detail/stackpole-electronics-inc/RNCP0805FTD150R/2240211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) | DK
R11, R14 | 2 | 82 | RMCF0805FT82R0 (https://www.digikey.com/en/products/detail/stackpole-electronics-inc/RMCF0805FT82R0/1713389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) | DK
J1 | 1 |  | 10118193-0001LF (https://www.digikey.com/en/products/detail/amphenol-cs-fci/10118193-0001LF/2785388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) | DK
X1 | 1 | 10MHz | DSC6001JE1A-010.0000 (https://www.digikey.com/en/products/detail/microchip-technology/DSC6001JE1A-010-0000/7732720) | DK
Y1 | 1 | 12MHz | CSTNE12M0GH5L000R0 (https://www.digikey.com/en/products/detail/murata-electronics/CSTNE12M0GH5L000R0/8747728) | DK
TP1, TP2 | 2 |  | 36-5000-ND (https://www.digikey.com/en/products/detail/keystone-electronics/5000/255326) | DK
