efabless/caravel_board/hardware/breakout/caravel_breakout_QFN/caravel_breakout_QFN.xlsx

Id | Designator | Package | Quantity | Value | Part Number | Supplier
1 | J1,J3,J2,J4 | Caravel_Breakout_Connectors_2x14 | 0 | DNI
3 | C9,C2,C7,C8,C3,C4,C5,C1,C6 | C_0402_1005Metric | 9 | 0.1uf | CC0402KRX7R9BB104 | DK
6 | U1 | QFN-64-1EP_9x9mm_P0.5mm_EP6x6mm | 1 | Caravel | Customer provided
