efabless/caravel_board/docs/trace cuts for mux install.png

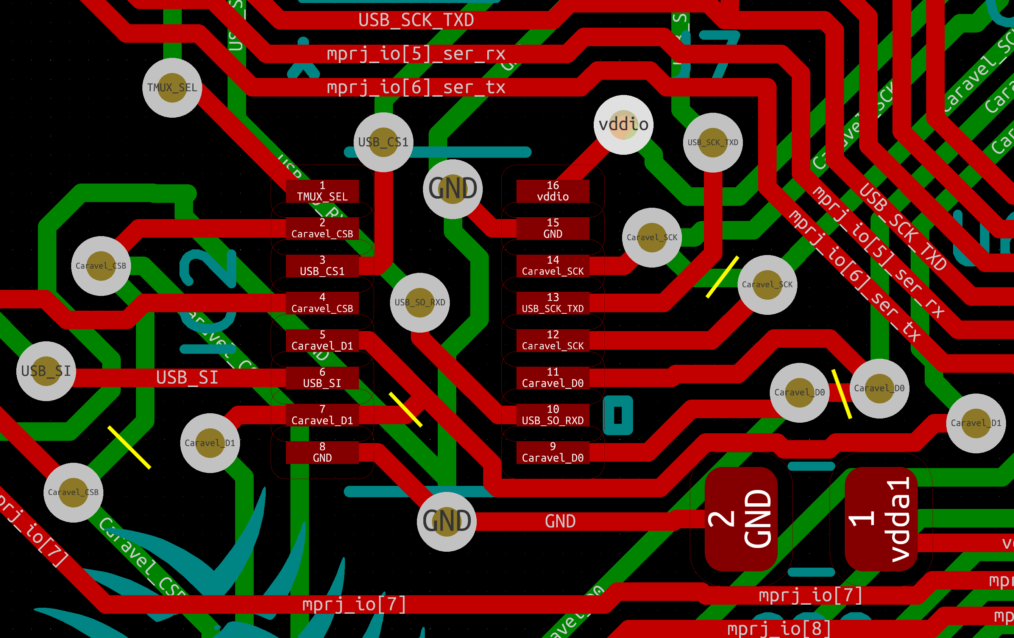
docs/trace cuts for mux install.png
