efabless/caravel_board/firmware/mpw2-5/nucleo/docs/nucleo_hat_pin_install.jpg

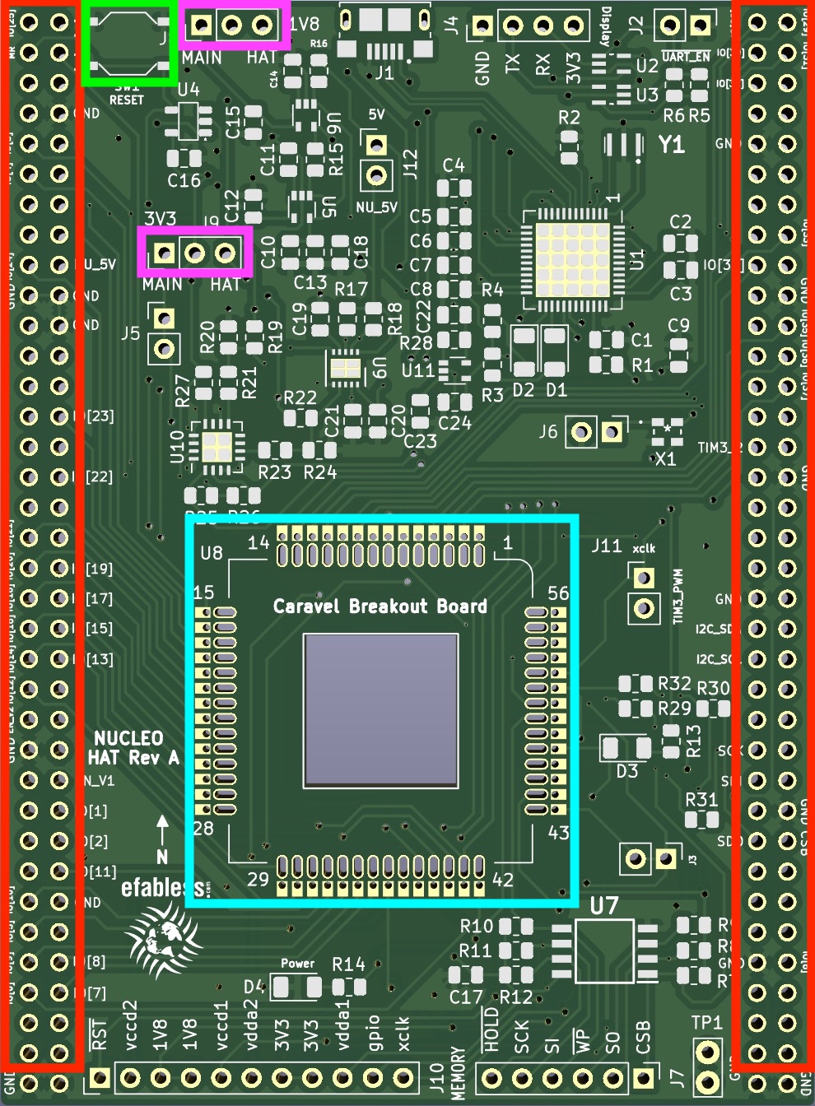
firmware/mpw2-5/nucleo/docs/nucleo_hat_pin_install.jpg
