efabless/caravel_board/hardware/development/caravel_pcb_v2/Caravel_schematic.pdf

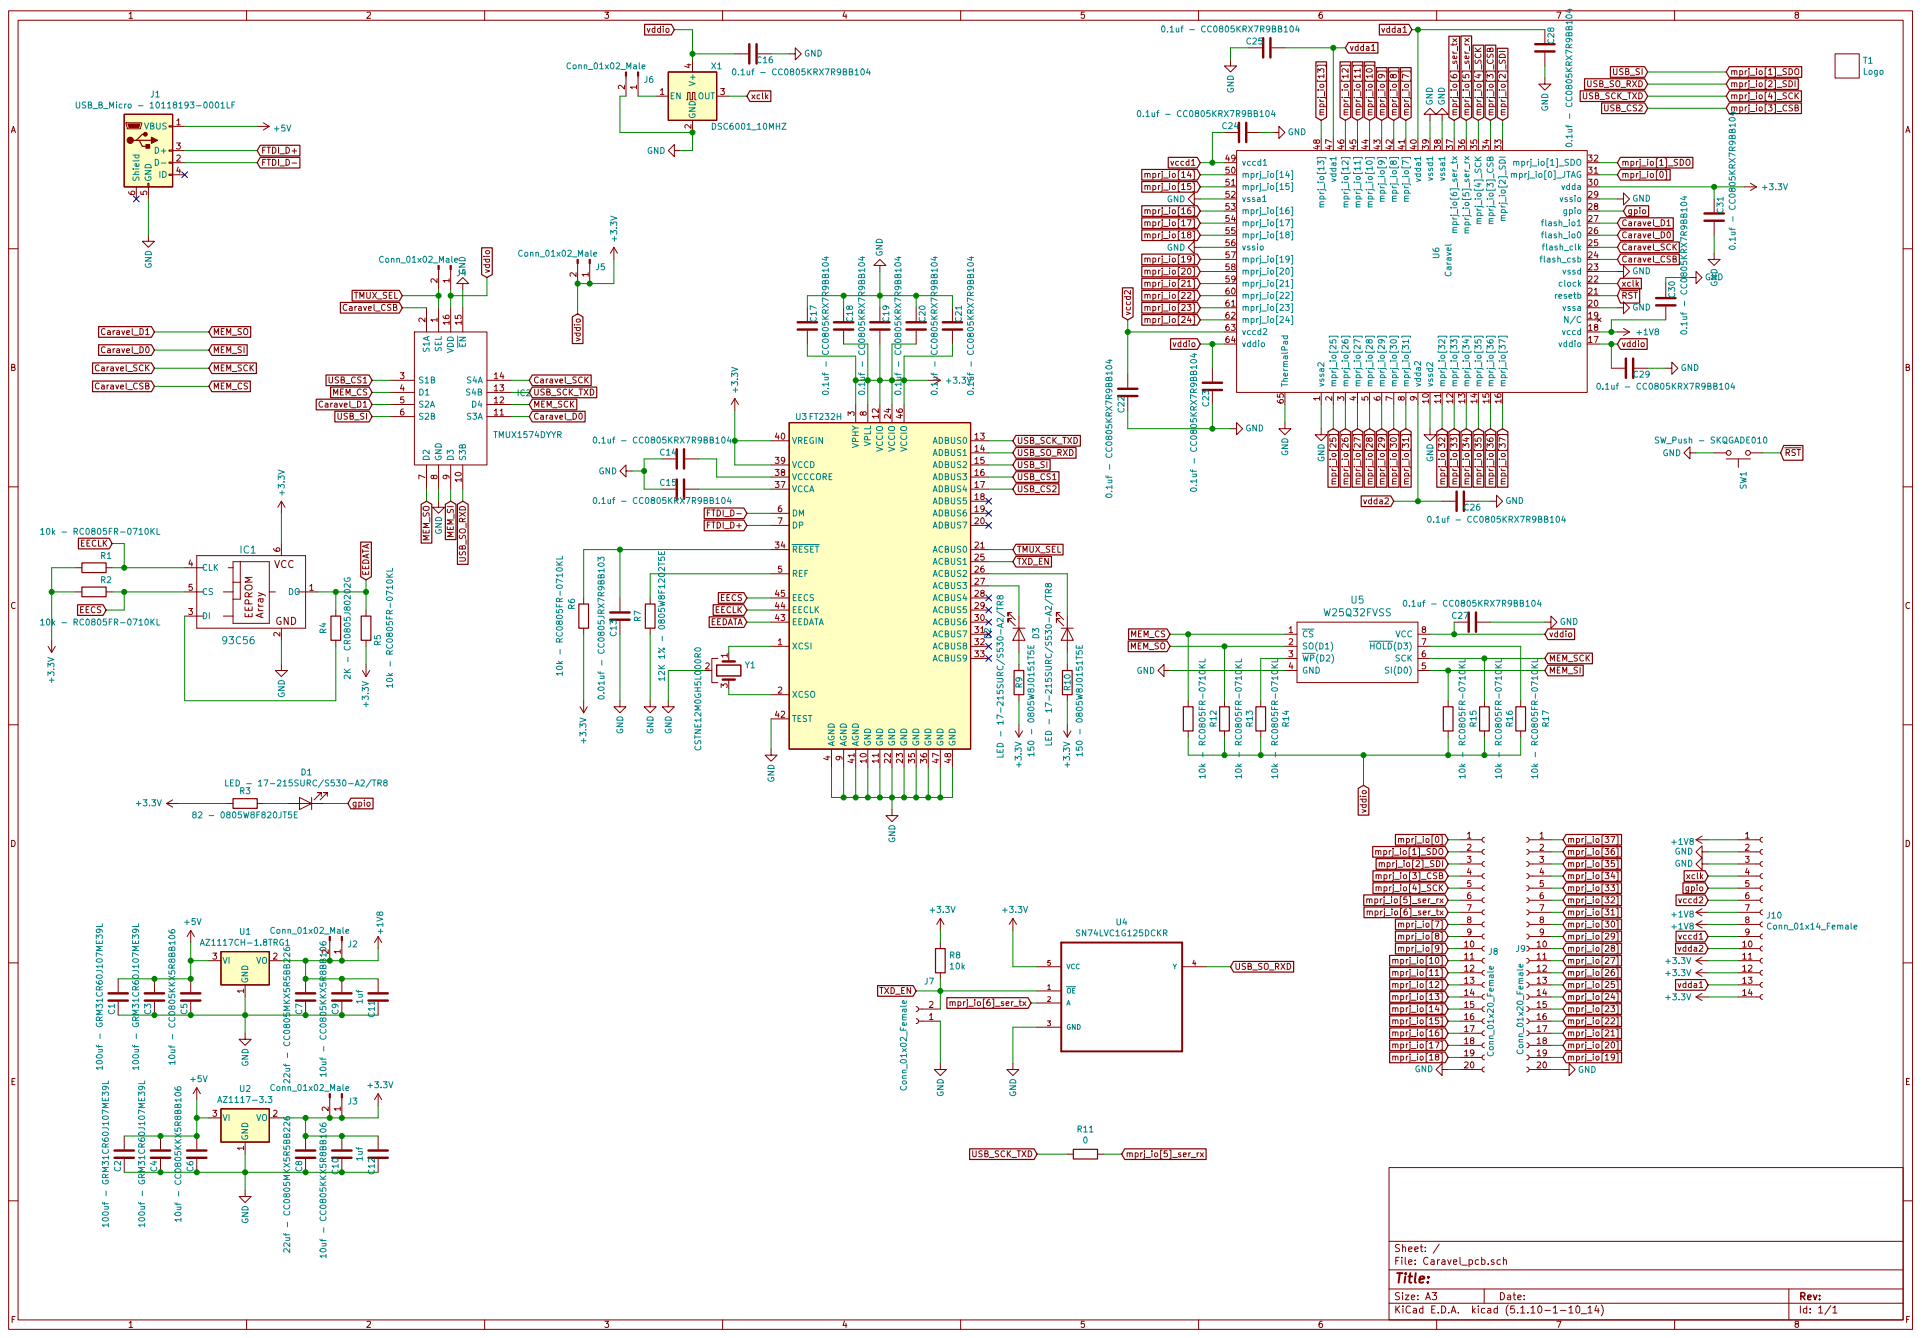
[picture p79: page 1]

1 VO 2 VI 3 U2 AZ1117-3.3 GND GND GND GND GND GND GND GND GND mprj_io[29]

1 VO 2 VI 3 U1 AZ1117CH-1.8TRG1 GND GND GND C31 0.1uf - CC0805KRX7R9BB104 C7 22uf - CC0805MKX5R5BB226 C8 22uf - CC0805MKX5R5BB226

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
