efabless/caravel_board/hardware/development/caravel_pcb_v2/gerbers/Caravel_pcb-F_SilkS.pdf

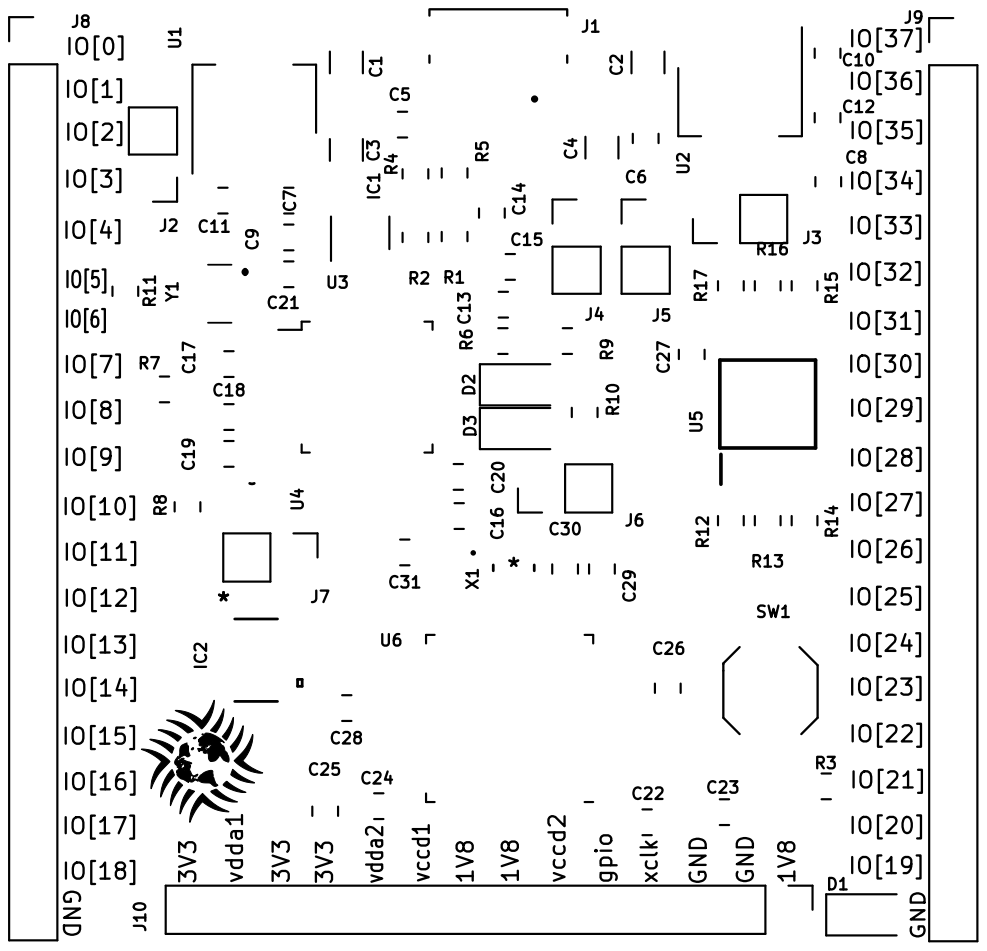
[picture p80: page 1]

3V3 vdda1 3V3 3V3 vdda2 vccd1 1V8 1V8 vccd2 gpio xclk GND GND 1V8 GND
