efabless/caravel_board/docs/caravel_qfn_bond.pdf

# efabless "caravel" project harness 64-pin QFN package version August 27, 2021 Revision 0

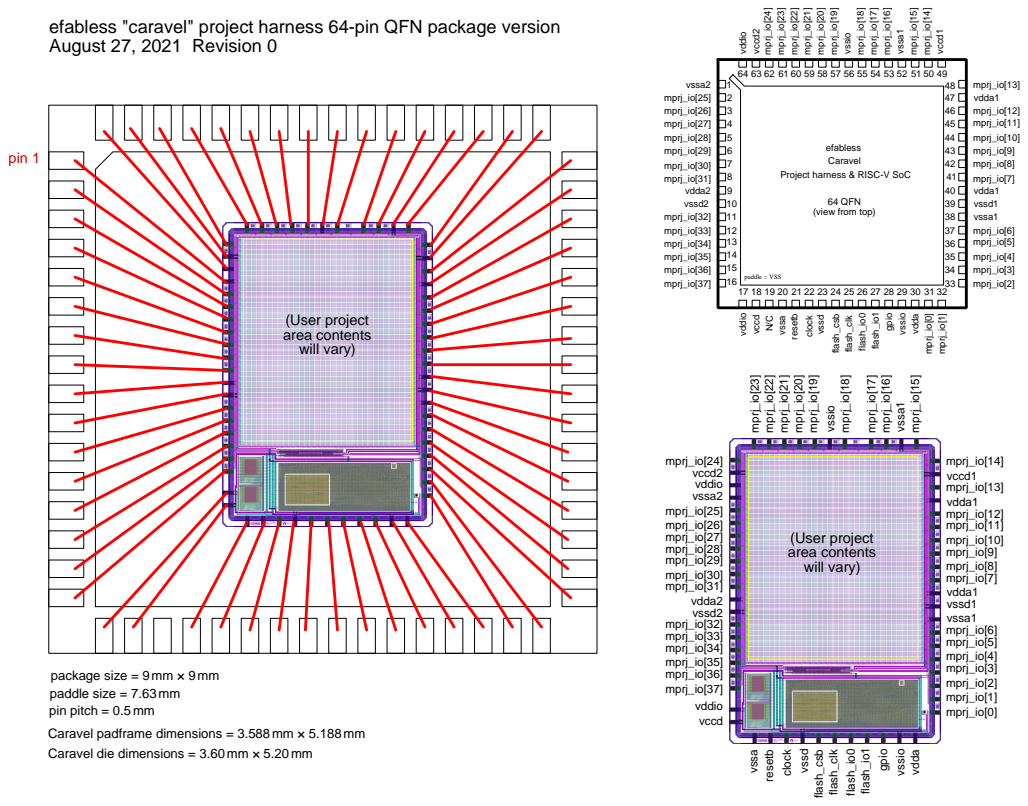
[picture p81: page 1]
Caravel; paddle = VSS 16; efabless; mprj_io[23]; mprj_io[22]; mprj_io[21]; mprj_io[20]; mprj_io[19]; vssio; mprj_io[18]; mprj_io[17]; mprj_io[16]; vssa1; mprj_io[15]; mprj_io[0]; mprj_io[1]; mprj_io[2]; mprj_io[3]; mprj_io[4]; mprj_io[5]; mprj_io[6]; vssd1; vdda1; mprj_io[7]; mprj_io[8]; mprj_io[9]; mprj_io[10]; mprj_io[11]; mprj_io[12]; mprj_io[13]; mprj_io[14]; vccd1; vssa; resetb; clock; vssd; flash_csb; flash_clk; flash_io0; flash_io1; gpio; vdda; mprj_io[24]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

Project harness & RISC-V SoC

64 QFN
(view from top)

package size = 9mm × 9mm
paddle size = 7.63mm
pin pitch = 0.5mm
Caravel padframe dimensions = 3.588mm × 5.188mm
Caravel die dimensions = 3.60mm × 5.20mm
