efabless/caravel_board/firmware/chipignite/_docs/caravel_registers.pdf

Register, byte addresses, bit fields, and description

reg_mprj_xfer
0x26000003 | 0x26000002 | 0x26000001 | 0x26000000 | address
0x13 | SPI register
(undefined, reads zero) | gpio xfer controls | value
31 | 30 | 29 | 28 | 27 | 26 | 25 | 24 | 23 | 22 | 21 | 20 | 19 | 18 | 17 | 16 | 15 | 14 | 13 | 12 | 11 | 10 | 9 | 8 | 7 | 6 | 5 | 4 | 3 | 2 | 1 | 0 | bit

gpio xfer controls (7 bits) bit fields:
bit 0 | serial xfer/busy | Write 1 to apply configuration values to GPIO. Auto-zeroing. Read back value 1 = busy, 0 = idle | default = 0
bit 1 | bitbang enable | 1 = serial transfer bitbang mode enabled; 0 = bitbang mode disabled | default = 0
bit 2 | bitbang resetn | 0 = bit bang mode reset; 1 = bitbang mode normal operation | default = 0
bit 3 | bitbang load | 0 = bit bang mode normal operation; 1 = latch configuration values | default = 0
bit 4 | bitbang clock | 0->1 transition: Advance data in serial shift register by 1 bit in bitbang mode | default = 0
bit 5 | bitbang data right | Value = data to apply to serial data right side shift register (GPIO 0 to 18) on next bitbang clock | default = 0
bit 6 | bitbang data left | Value = data to apply to serial data left side shift register (GPIO 19 to 37) on next bitbang clock | default = 0

The reg_mprj_xfer register controls the programming of the configurable GPIO (general-purpose input/output) pins . There are 38 GPIO pins,
in two banks of 19. GPIO 0 to 18 start at the bottom right corner of the chip and extend to the midpoint of the top side of the chip. GPIO 19 to
37 start at the midpoint of the top side of the chip and extend to the bottom left corner. The GPIO indexes always increase in a counterclockwise direction around the chip perimeter. The GPIOs are configured through the "user_defines.v" file to have a specific configuration on power-up. However, the GPIOs may be reprogrammed at any time either through the housekeeping SPI or through processor reads and writes to the memory map described on this page. The programming starts with the intended configuration for each GPIO programmed into registers reg_mprj_io_0 to reg_mprj_io_37 (see below). These registers are a staging area for the GPIO configuration. The actual GPIO configuration is kept in duplicate registers next to each GPIO and are not directly readable or writeable. The GPIOs are configured by an automatic programming step that copies the configurations from the registers to the GPIO pins via a serial shift register. The reg_mprj_xfer register controls this programming process. Normally, only the simple, automatic programming is used. The user sets (through the housekeeping SPI or from a running program) bit 0 to start the configuration transfer from housekeeping registers to the GPIO pins. The same bit 0 may be subsequently monitored; when the bit clears, the configuration programming is complete. The rest of the control bits are intended only for diagnostic purposes. They can be used to override the automatic GPIO programming and perform the programming sequence manually.

reg_mprj_pwr
0x26000007 | 0x26000006 | 0x26000005 | 0x26000004 | address
0x6E | SPI register
(undefined, reads zero) | value
31 | 30 | 29 | 28 | 27 | 26 | 25 | 24 | 23 | 22 | 21 | 20 | 19 | 18 | 17 | 16 | 15 | 14 | 13 | 12 | 11 | 10 | 9 | 8 | 7 | 6 | 5 | 4 | 3 | 2 | 1 | 0 | bit
This register intended for future use powering up/down internal power domains. Currently it has no function. | default = N/A

reg_mprj_datal
0x2600000F | 0x2600000E | 0x2600000D | 0x2600000C | address
0x6A | 0x6B | 0x6C | 0x6D | SPI register
gpio data [31:0] | value
31 | 30 | 29 | 28 | 27 | 26 | 25 | 24 | 23 | 22 | 21 | 20 | 19 | 18 | 17 | 16 | 15 | 14 | 13 | 12 | 11 | 10 | 9 | 8 | 7 | 6 | 5 | 4 | 3 | 2 | 1 | 0 | bit
bits 31 to 0 | gpio data [31:0] | Read values from or write values to the GPIO pins for GPIO[31] (bit 31) down to GPIO[0] (bit 0) | default = 0

reg_mprj_datah
0x26000013 | 0x26000012 | 0x26000011 | 0x26000010 | address
0x69 | SPI register
(undefined, reads zero) | gpio data [37:32] | value
31 | 30 | 29 | 28 | 27 | 26 | 25 | 24 | 23 | 22 | 21 | 20 | 19 | 18 | 17 | 16 | 15 | 14 | 13 | 12 | 11 | 10 | 9 | 8 | 7 | 6 | 5 | 4 | 3 | 2 | 1 | 0 | bit
bits 5 to 0 | gpio data [37:32] | Read values from or write values to the GPIO pins for GPIO[37] (bit 5) down to GPIO[32] (bit 0) | default = 0

The reg_mprj_datah and reg_mprj_datal registers together comprise the 38 bits of data corresponding to the 38 configurable GPIO pins.
Writing to the register is only meaningful for GPIO pins that are configured for management control and which are not being controlled by one
of the special functions (e.g., SPI master, UART, housekeeping SPI). If the corresponding GPIO is configured for management control, configured as an output, and has the output enabled, then a bit written to these registers will appear as an output value on the corresponding GPIO pin. Reading the value from these registers will read the value at the pin, regardless of whether or not the pin is configured for management control, and whether or not the pin is configured for a special function. However, the GPIO must have the input enabled.

reg_mprj_io_0
0x26000027 | 0x26000026 | 0x26000025 | 0x26000024 | address

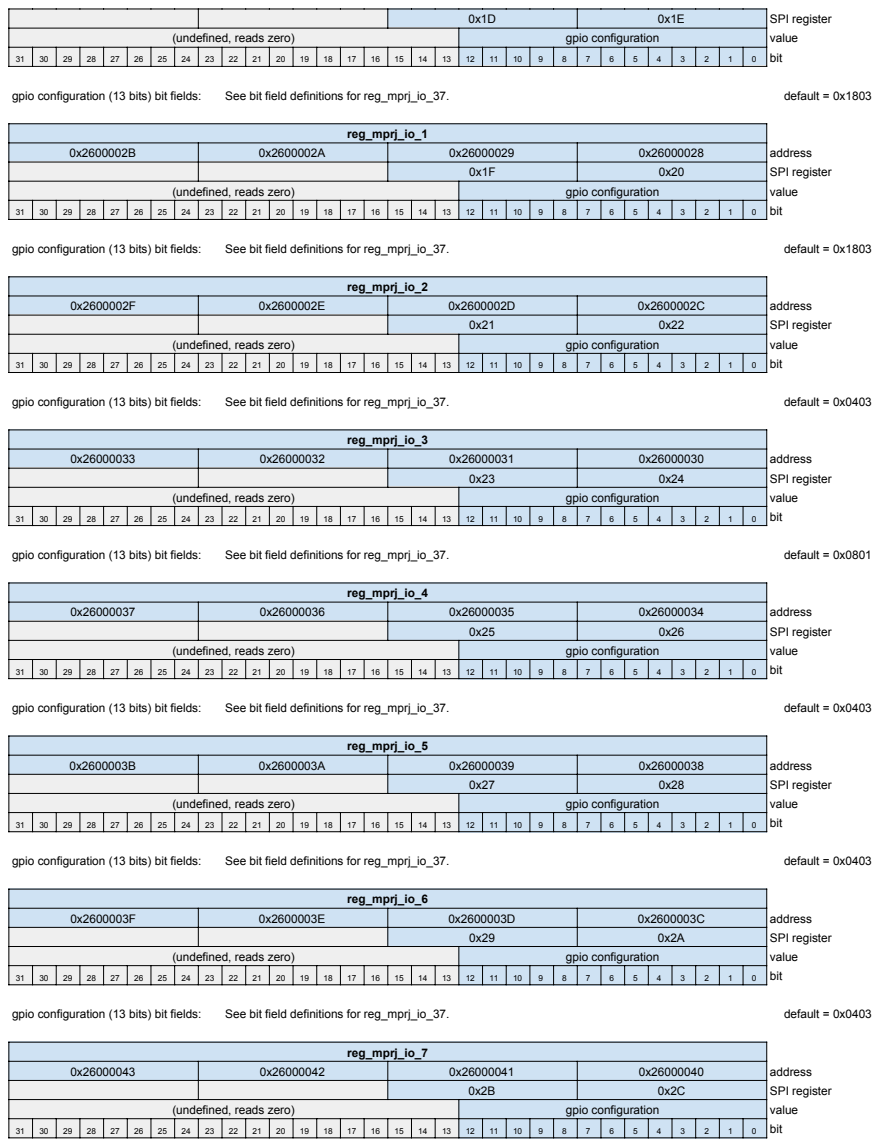
[picture p82: page 2]
gpio configuration (13 bits) bit fields:; See bit field definitions for reg_mprj_io_37.; default = 0x1803; default = 0x0403; default = 0x0801

(undefined, reads zero) 31 30 29 28 27 26 25 24 23 22 21 20 19 18 17 16 | 0x1D 0x1E | SPI register
15 14 13 | gpio configuration 12 11 10 9 8 7 6 5 4 3 2 1 0 | value bit

reg_mprj_io_1 0x2600002B 0x2600002A 0x26000029 0x26000028 | address

(undefined, reads zero) 31 30 29 28 27 26 25 24 23 22 21 20 19 18 17 16 | 0x1F 0x20 | SPI register

reg_mprj_io_2 0x2600002F 0x2600002E 0x2600002D 0x2600002C | address

(undefined, reads zero) 31 30 29 28 27 26 25 24 23 22 21 20 19 18 17 16 | 0x21 0x22 | SPI register

reg_mprj_io_3 0x26000033 0x26000032 0x26000031 0x26000030 | address

(undefined, reads zero) 31 30 29 28 27 26 25 24 23 22 21 20 19 18 17 16 | 0x23 0x24 | SPI register

reg_mprj_io_4 0x26000037 0x26000036 0x26000035 0x26000034 | address

(undefined, reads zero) 31 30 29 28 27 26 25 24 23 22 21 20 19 18 17 16 | 0x25 0x26 | SPI register

reg_mprj_io_5 0x2600003B 0x2600003A 0x26000039 0x26000038 | address

(undefined, reads zero) 31 30 29 28 27 26 25 24 23 22 21 20 19 18 17 16 | 0x27 0x28 | SPI register

reg_mprj_io_6 0x2600003F 0x2600003E 0x2600003D 0x2600003C | address

(undefined, reads zero) 31 30 29 28 27 26 25 24 23 22 21 20 19 18 17 16 | 0x29 0x2A | SPI register

reg_mprj_io_7 0x26000043 0x26000042 0x26000041 0x26000040 | address

(undefined, reads zero) 31 30 29 28 27 26 25 24 23 22 21 20 19 18 17 16 | 0x2B 0x2C | SPI register

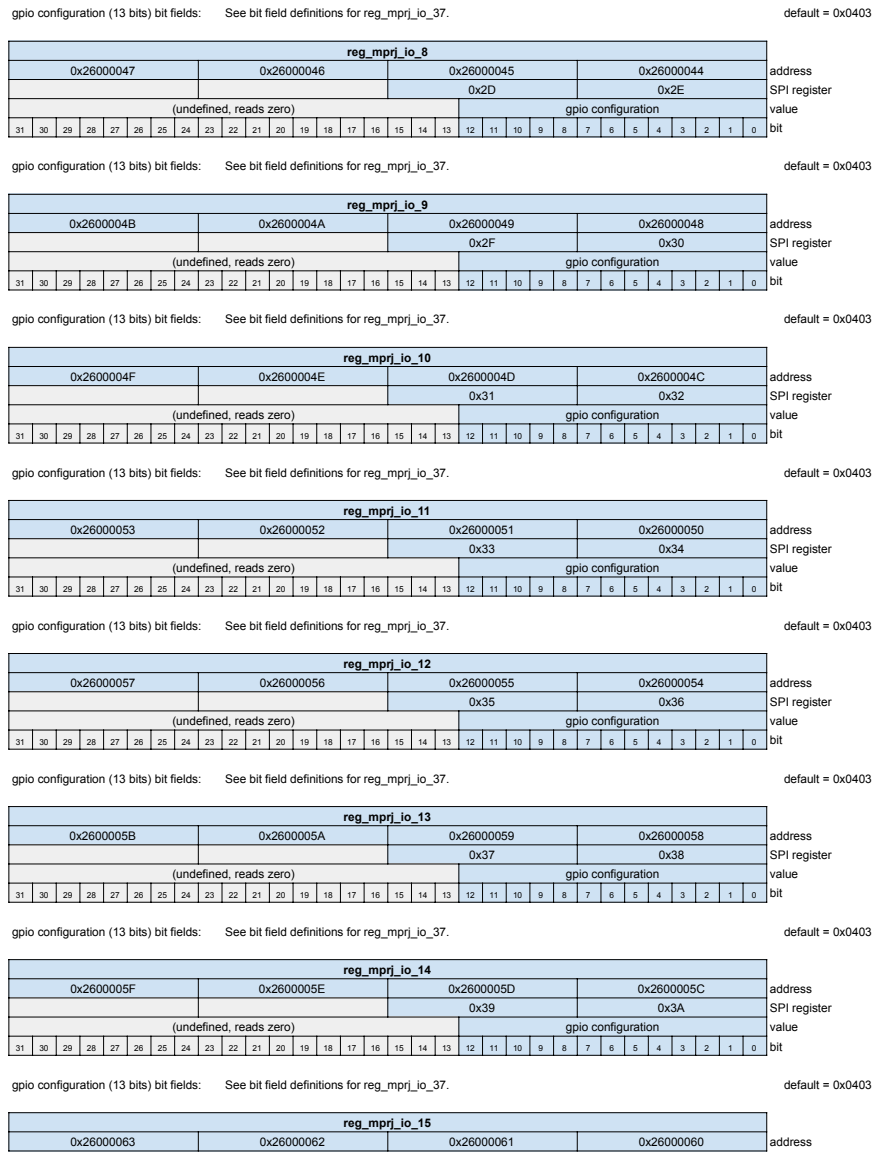
[picture p83: page 3]
gpio configuration (13 bits) bit fields:; See bit field definitions for reg_mprj_io_37.; default = 0x0403; reg_mprj_io_15; address

reg_mprj_io_8 0x26000047 0x26000046 0x26000045 0x26000044 | address

(undefined, reads zero) 31 30 29 28 27 26 25 24 23 22 21 20 19 18 17 16 | 0x2D 0x2E | SPI register
15 14 13 | gpio configuration 12 11 10 9 8 7 6 5 4 3 2 1 0 | value bit

reg_mprj_io_9 0x2600004B 0x2600004A 0x26000049 0x26000048 | address

(undefined, reads zero) 31 30 29 28 27 26 25 24 23 22 21 20 19 18 17 16 | 0x2F 0x30 | SPI register

reg_mprj_io_10 0x2600004F 0x2600004E 0x2600004D 0x2600004C | address

(undefined, reads zero) 31 30 29 28 27 26 25 24 23 22 21 20 19 18 17 16 | 0x31 0x32 | SPI register

reg_mprj_io_11 0x26000053 0x26000052 0x26000051 0x26000050 | address

(undefined, reads zero) 31 30 29 28 27 26 25 24 23 22 21 20 19 18 17 16 | 0x33 0x34 | SPI register

reg_mprj_io_12 0x26000057 0x26000056 0x26000055 0x26000054 | address

(undefined, reads zero) 31 30 29 28 27 26 25 24 23 22 21 20 19 18 17 16 | 0x35 0x36 | SPI register

reg_mprj_io_13 0x2600005B 0x2600005A 0x26000059 0x26000058 | address

(undefined, reads zero) 31 30 29 28 27 26 25 24 23 22 21 20 19 18 17 16 | 0x37 0x38 | SPI register

reg_mprj_io_14 0x2600005F 0x2600005E 0x2600005D 0x2600005C | address

(undefined, reads zero) 31 30 29 28 27 26 25 24 23 22 21 20 19 18 17 16 | 0x39 0x3A | SPI register

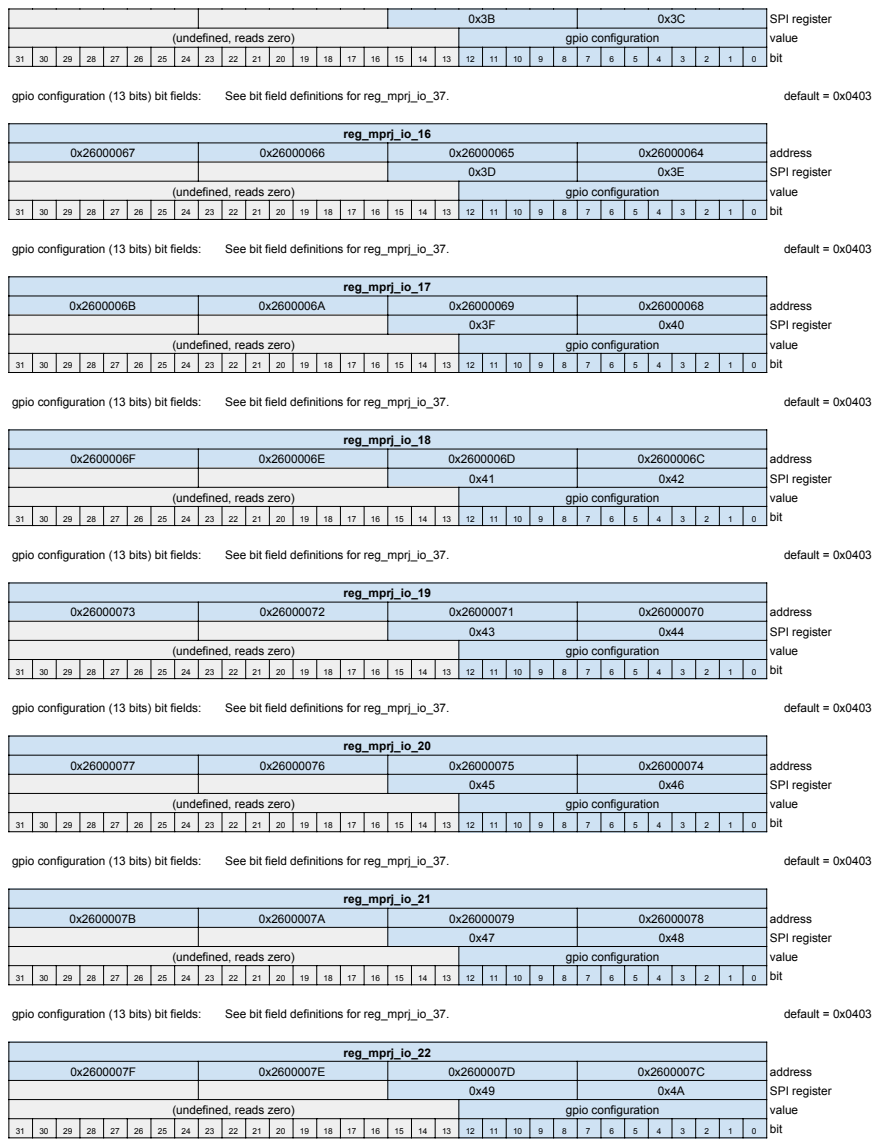
[picture p84: page 4]
gpio configuration (13 bits) bit fields:; See bit field definitions for reg_mprj_io_37.; default = 0x0403

(undefined, reads zero) 31 30 29 28 27 26 25 24 23 22 21 20 19 18 17 16 | 0x3B 0x3C | SPI register
15 14 13 | gpio configuration 12 11 10 9 8 7 6 5 4 3 2 1 0 | value bit

reg_mprj_io_16 0x26000067 0x26000066 0x26000065 0x26000064 | address

(undefined, reads zero) 31 30 29 28 27 26 25 24 23 22 21 20 19 18 17 16 | 0x3D 0x3E | SPI register

reg_mprj_io_17 0x2600006B 0x2600006A 0x26000069 0x26000068 | address

(undefined, reads zero) 31 30 29 28 27 26 25 24 23 22 21 20 19 18 17 16 | 0x3F 0x40 | SPI register

reg_mprj_io_18 0x2600006F 0x2600006E 0x2600006D 0x2600006C | address

(undefined, reads zero) 31 30 29 28 27 26 25 24 23 22 21 20 19 18 17 16 | 0x41 0x42 | SPI register

reg_mprj_io_19 0x26000073 0x26000072 0x26000071 0x26000070 | address

(undefined, reads zero) 31 30 29 28 27 26 25 24 23 22 21 20 19 18 17 16 | 0x43 0x44 | SPI register

reg_mprj_io_20 0x26000077 0x26000076 0x26000075 0x26000074 | address

(undefined, reads zero) 31 30 29 28 27 26 25 24 23 22 21 20 19 18 17 16 | 0x45 0x46 | SPI register

reg_mprj_io_21 0x2600007B 0x2600007A 0x26000079 0x26000078 | address

(undefined, reads zero) 31 30 29 28 27 26 25 24 23 22 21 20 19 18 17 16 | 0x47 0x48 | SPI register

reg_mprj_io_22 0x2600007F 0x2600007E 0x2600007D 0x2600007C | address

(undefined, reads zero) 31 30 29 28 27 26 25 24 23 22 21 20 19 18 17 16 | 0x49 0x4A | SPI register

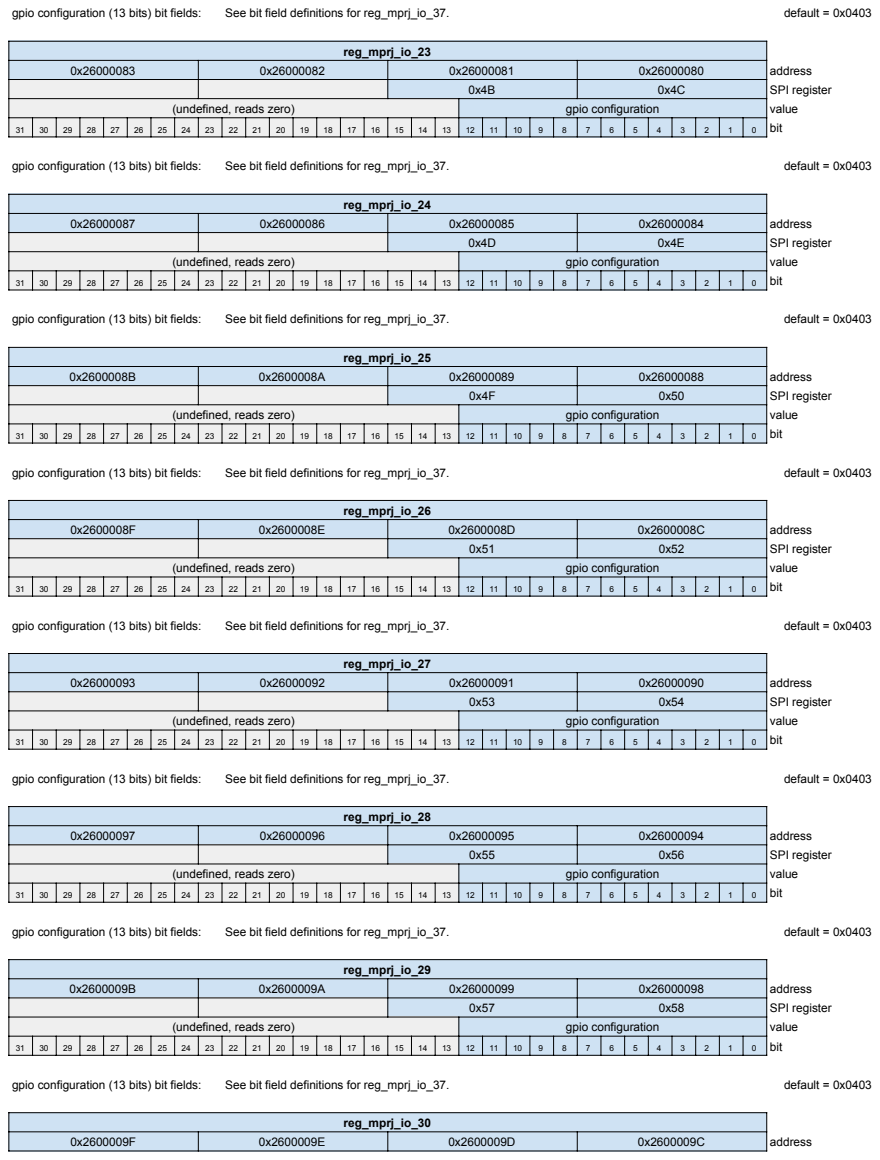
[picture p85: page 5]
gpio configuration (13 bits) bit fields:; See bit field definitions for reg_mprj_io_37.; default = 0x0403; reg_mprj_io_30; address

reg_mprj_io_23 0x26000083 0x26000082 0x26000081 0x26000080 | address

(undefined, reads zero) 31 30 29 28 27 26 25 24 23 22 21 20 19 18 17 16 | 0x4B 0x4C | SPI register
15 14 13 | gpio configuration 12 11 10 9 8 7 6 5 4 3 2 1 0 | value bit

reg_mprj_io_24 0x26000087 0x26000086 0x26000085 0x26000084 | address

(undefined, reads zero) 31 30 29 28 27 26 25 24 23 22 21 20 19 18 17 16 | 0x4D 0x4E | SPI register

reg_mprj_io_25 0x2600008B 0x2600008A 0x26000089 0x26000088 | address

(undefined, reads zero) 31 30 29 28 27 26 25 24 23 22 21 20 19 18 17 16 | 0x4F 0x50 | SPI register

reg_mprj_io_26 0x2600008F 0x2600008E 0x2600008D 0x2600008C | address

(undefined, reads zero) 31 30 29 28 27 26 25 24 23 22 21 20 19 18 17 16 | 0x51 0x52 | SPI register

reg_mprj_io_27 0x26000093 0x26000092 0x26000091 0x26000090 | address

(undefined, reads zero) 31 30 29 28 27 26 25 24 23 22 21 20 19 18 17 16 | 0x53 0x54 | SPI register

reg_mprj_io_28 0x26000097 0x26000096 0x26000095 0x26000094 | address

(undefined, reads zero) 31 30 29 28 27 26 25 24 23 22 21 20 19 18 17 16 | 0x55 0x56 | SPI register

reg_mprj_io_29 0x2600009B 0x2600009A 0x26000099 0x26000098 | address

(undefined, reads zero) 31 30 29 28 27 26 25 24 23 22 21 20 19 18 17 16 | 0x57 0x58 | SPI register

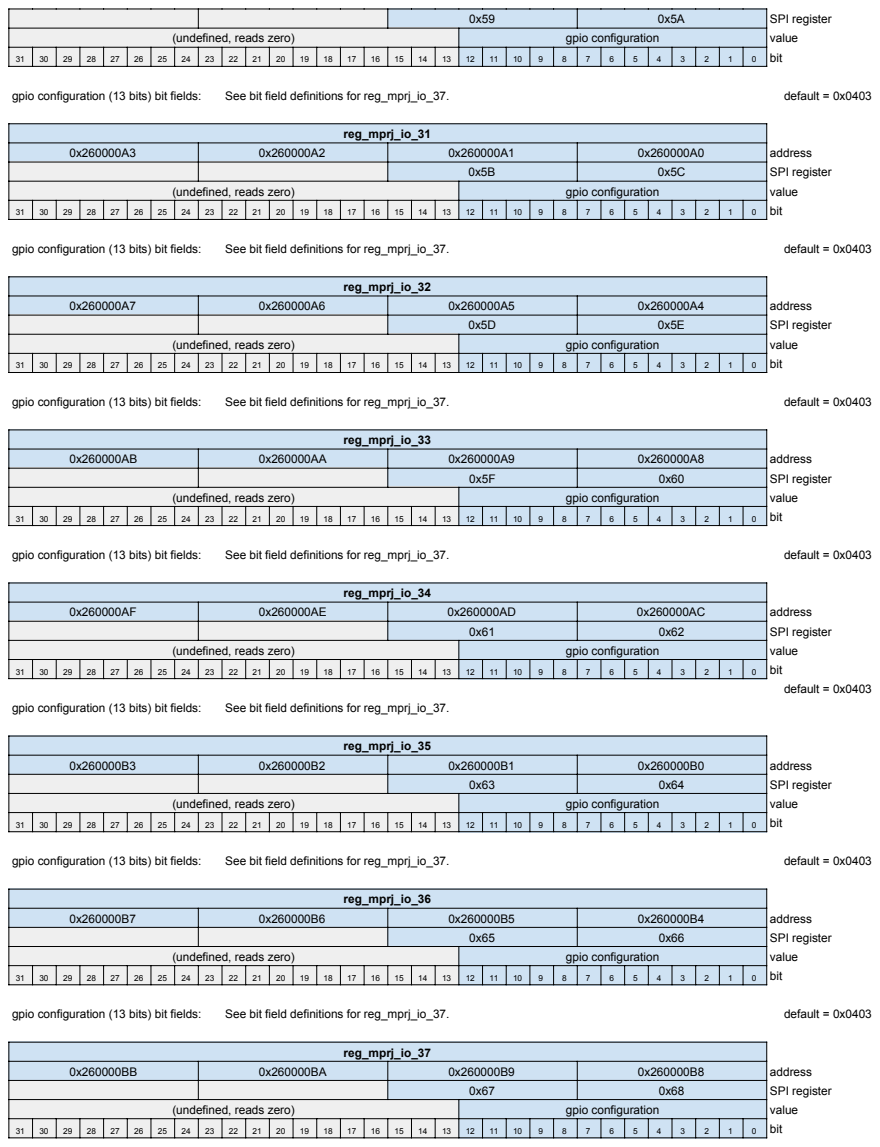
[picture p86: page 6]
gpio configuration (13 bits) bit fields:; See bit field definitions for reg_mprj_io_37.; default = 0x0403

(undefined, reads zero) 31 30 29 28 27 26 25 24 23 22 21 20 19 18 17 16 | 0x59 0x5A | SPI register
15 14 13 | gpio configuration 12 11 10 9 8 7 6 5 4 3 2 1 0 | value bit

reg_mprj_io_31 0x260000A3 0x260000A2 0x260000A1 0x260000A0 | address

(undefined, reads zero) 31 30 29 28 27 26 25 24 23 22 21 20 19 18 17 16 | 0x5B 0x5C | SPI register

reg_mprj_io_32 0x260000A7 0x260000A6 0x260000A5 0x260000A4 | address

(undefined, reads zero) 31 30 29 28 27 26 25 24 23 22 21 20 19 18 17 16 | 0x5D 0x5E | SPI register

reg_mprj_io_33 0x260000AB 0x260000AA 0x260000A9 0x260000A8 | address

(undefined, reads zero) 31 30 29 28 27 26 25 24 23 22 21 20 19 18 17 16 | 0x5F 0x60 | SPI register

reg_mprj_io_34 0x260000AF 0x260000AE 0x260000AD 0x260000AC | address

(undefined, reads zero) 31 30 29 28 27 26 25 24 23 22 21 20 19 18 17 16 | 0x61 0x62 | SPI register

reg_mprj_io_35 0x260000B3 0x260000B2 0x260000B1 0x260000B0 | address

(undefined, reads zero) 31 30 29 28 27 26 25 24 23 22 21 20 19 18 17 16 | 0x63 0x64 | SPI register

reg_mprj_io_36 0x260000B7 0x260000B6 0x260000B5 0x260000B4 | address

(undefined, reads zero) 31 30 29 28 27 26 25 24 23 22 21 20 19 18 17 16 | 0x65 0x66 | SPI register

reg_mprj_io_37 0x260000BB 0x260000BA 0x260000B9 0x260000B8 | address

(undefined, reads zero) 31 30 29 28 27 26 25 24 23 22 21 20 19 18 17 16 | 0x67 0x68 | SPI register

gpio configuration (13 bits) bit fields: | default = 0x0403
bit 0 | management enable 1 = management SoC controls GPIO; 0 = user project controls GPIO
bit 1 | output disable | 1 = digital output driver disabled ; 0 = digital output driver enabled (management controlled mode only)
bit 2 | hold state value | Value of GPIO when in low-power state.
bit 3 | input disable | 1 = digital input driver disabled; 1 = digital input driver enabled
bit 4 | IB mode select | See definition in SkyWater documentation for sky130_fd_io__top_gpiov2
bit 5 | analog enable | See definition in SkyWater documentation for sky130_fd_io__top_gpiov2
bit 6 | analog select | See definition in SkyWater documentation for sky130_fd_io__top_gpiov2
bit 7 | analog polarity | See definition in SkyWater documentation for sky130_fd_io__top_gpiov2
bit 8 | slow slew | See definition in SkyWater documentation for sky130_fd_io__top_gpiov2
bit 9 | trip point select | See definition in SkyWater documentation for sky130_fd_io__top_gpiov2
bits 10-12 | digital mode | See table below for typical settings; see SkyWater documentation for complete list.
000 | disabled | Both input and output digital buffers disabled. Use this when connecting an analog signal to the pad
001 | input | Digital input only. Output buffer is disabled.
010 | input pullup | Input mode with pull-up. User mode only: Output must be enabled and driven to value 1.
011 | input pulldown | Input mode with pull-down. User mode only: Output must be enabled and driven to value 0.
110 | output | Digital output. User mode only: Output must be enabled (OEB = 0)

The registers reg_mprj_io_0 through reg_mprj_io_37 are a staging area for the configuration of GPIO pins 0 to 37, respectively. Each GPIO is controlled by a 13 bit vector with values as described above. The values in the staging area are copied to the GPIO pins by use of the register reg_mrpj_xfer (see above). The default value of all GPIOs other than 0 to 4 is determined by the values set by the user in the file user_defines.v. The configuration is via-programmed at the GPIO itself. However, the value is not duplicated in the housekeeping registers, which continue to read the default values indicated above until the register is modified. The header file defs.h includes macros for the most common GPIO configuration settings.

reg_hkspi_status
0x26100003 | 0x26100002 | 0x26100001 | 0x26100000 | address
0x00 | SPI register
(undefined, reads zero) | SPI status | value
31 | 30 | 29 | 28 | 27 | 26 | 25 | 24 | 23 | 22 | 21 | 20 | 19 | 18 | 17 | 16 | 15 | 14 | 13 | 12 | 11 | 10 | 9 | 8 | 7 | 6 | 5 | 4 | 3 | 2 | 1 | 0 | bit
bits 0-7 SPI status | This byte is currently unused and undefined (intended for SPI mode control) | default = 0

reg_hkspi_chip_id
0x26100007 | 0x26100006 | 0x26100005 | 0x26100004 | address
0x01 | 0x02 | 0x03 | SPI register
(undefined, reads zero) | Manufacturer ID (= 0x456) | Product ID = (0x11) | value
31 | 30 | 29 | 28 | 27 | 26 | 25 | 24 | 23 | 22 | 21 | 20 | 19 | 18 | 17 | 16 | 15 | 14 | 13 | 12 | 11 | 10 | 9 | 8 | 7 | 6 | 5 | 4 | 3 | 2 | 1 | 0 | bit
bits 0-23 | Fixed product ID value 0x11 representing Caravel v4 (Sky130). Value is read-only | default = 0x11
bits 16-23 | Fixed manufacturer ID value 0x456 representing Efabless Corporation. Value is read-only | default = 0x456

reg_hkspi_user_id
0x2610000B | 0x2610000A | 0x26100009 | 0x26100008 | address
0x04 | 0x05 | 0x06 | 0x07 | SPI register
User project ID | value
31 | 30 | 29 | 28 | 27 | 26 | 25 | 24 | 23 | 22 | 21 | 20 | 19 | 18 | 17 | 16 | 15 | 14 | 13 | 12 | 11 | 10 | 9 | 8 | 7 | 6 | 5 | 4 | 3 | 2 | 1 | 0 | bit
bits 0-31 | Unique project ID assigned to each user design. Traditionally, bits 16-31 are an ID sub-field for the MPW run. | default = (variable)

The reg_hkspi_user_id register allows a user to read back the 32-bit project ID value assigned to the Caravel user project. Each project on a
reticle (currently 40 projects per shuttle run) gets a unique identification number that is automatically via-programmed into this register during
chip assembly prior to tape-out.

reg_hkspi_pll_ena
0x2610000F | 0x2610000E | 0x2610000D | 0x2610000C | address
0x08 | SPI register
(undefined, reads zero) | DCOENA value
31 | 30 | 29 | 28 | 27 | 26 | 25 | 24 | 23 | 22 | 21 | 20 | 19 | 18 | 17 | 16 | 15 | 14 | 13 | 12 | 11 | 10 | 9 | 8 | 7 | 6 | 5 | 4 | 3 | 2 | 1 | 0 | bit
bit 0 | ENA | DLL/DCO enable (1 = enabled; 0 = disabled) | default = 0
bit 1 | DCO | DCO mode enable (1 = use DCO mode; 0 = use DLL mode) | default = 1

The caravel chip has an on-board oscillator that is a programmable-length ring oscillator, or DCO (digitally-controlled oscillator). The oscillator on the Sky130 version of Caravel has a frequency range of about 50MHz to 120MHz (at a low-voltage supply of 1.8V). This register controls the enabled state of the DCO and the DLL (digital locked loop), which is a controller that automatically trims the DCO to lock the frequency to a multiple of the external clock input. The base enable (bit 0) must be set to 1 for either the DCO or the DLL to operate. The DCO enable bit is effectively a DLL disable bit, which lets the DCO run freely with manual trim control through the reg_hkspi_pll_trim register. Registers affecting DCO and DLL operation are reg_hkspi_pll_ena, reg_hkspi_pll_bypass, reg_hkspi_pll_trim, reg_hkspi_pll_source, and reg_hkspi_pll_divider. Please see the register descriptions below for additional information.

reg_hkspi_pll_bypass
0x26100013 | 0x26100012 | 0x26100011 | 0x26100010 | address
0x09 | SPI register
(undefined, reads zero) | BYP | value
31 | 30 | 29 | 28 | 27 | 26 | 25 | 24 | 23 | 22 | 21 | 20 | 19 | 18 | 17 | 16 | 15 | 14 | 13 | 12 | 11 | 10 | 9 | 8 | 7 | 6 | 5 | 4 | 3 | 2 | 1 | 0 | bit
bit 0 | BYP | DLL bypass (1 = use external clock; 0 = use DLL/DCO clock) | default = 1

The reg_hkspi_pll_bypass register contains one bit which, when set, bypasses the DLL or DCO (see above) and allows the Caravel chip core
to be driven by the signal on the external clock pin. When cleared, the Caravel chip core is driven from the DLL/DCO clock. The default value
is 1 so that the clock rate on power-up is defined by the external clock.

reg_hkspi_irq
0x26100017 | 0x26100016 | 0x26100015 | 0x26100014 | address
0x0A | SPI register
(undefined, reads zero) | IRQ | value
31 | 30 | 29 | 28 | 27 | 26 | 25 | 24 | 23 | 22 | 21 | 20 | 19 | 18 | 17 | 16 | 15 | 14 | 13 | 12 | 11 | 10 | 9 | 8 | 7 | 6 | 5 | 4 | 3 | 2 | 1 | 0 | bit
bit 0 | IRQ | Manual interrupt (1 = interrupt; 0 = no action) | default = 0

The reg_hkspi_irq register can be used to apply a manual interrupt to the VexRISC processor. The value of bit 0 is passed directly to the
interrupt vector of the processor.

reg_hkspi_reset
0x2610001B | 0x2610001A | 0x26100019 | 0x26100018 | address
0x0B | SPI register
(undefined, reads zero) | RST | value
31 | 30 | 29 | 28 | 27 | 26 | 25 | 24 | 23 | 22 | 21 | 20 | 19 | 18 | 17 | 16 | 15 | 14 | 13 | 12 | 11 | 10 | 9 | 8 | 7 | 6 | 5 | 4 | 3 | 2 | 1 | 0 | bit
bit 0 | RST | Manual reset (1 = apply reset; 0 = release reset) | default = 0

The reg_hkspi_reset register can be used to apply a manual reset to the VexRISC processor. It is equivalent to grounding the RESETB pin
on the chip. Note that both the pin and software resets do not affect values in the housekeeping module, which can only be reset by a power
cycle to the chip.

reg_hkspi_pll_trim
0x2610001F | 0x2610001E | 0x2610001D | 0x2610001C | address
0x10 | 0x0F | 0x0E | 0x0D | SPI register
(undefined, reads zero) | DLL manual trim | value
31 | 30 | 29 | 28 | 27 | 26 | 25 | 24 | 23 | 22 | 21 | 20 | 19 | 18 | 17 | 16 | 15 | 14 | 13 | 12 | 11 | 10 | 9 | 8 | 7 | 6 | 5 | 4 | 3 | 2 | 1 | 0 | bit
all bits | All 1 values = maximum trim; all 0 values = minimum trim (To-do: table needed) | default = 0x03ffefff

The reg_hkspi_pll_trim value controls the frequency of the DCO when the DCO is not in DLL mode (free-running DCO mode). The trim is
undecoded, so each trim bit will turn a section of the ring oscillator on or off, lengthening or shortening the ring oscillator. With 26 trim bits,
there are effectively 27 unique settings of the DCO, from minimum trim (value 0x00000000) to maximum trim (value 0x03ffffff). The default state is one less than the maximum trim and is necessary for proper startup of the DLL.

reg_hkspi_pll_source
0x26100023 | 0x26100022 | 0x26100021 | 0x26100020 | address
0x11 | SPI register
(undefined, reads zero) | out div 2 | out div 1 | value
31 | 30 | 29 | 28 | 27 | 26 | 25 | 24 | 23 | 22 | 21 | 20 | 19 | 18 | 17 | 16 | 15 | 14 | 13 | 12 | 11 | 10 | 9 | 8 | 7 | 6 | 5 | 4 | 3 | 2 | 1 | 0 | bit
bit 2-0 | out div 1 | Core clock DLL output divider (0 = thru; 1 = off; 2-7 = divide by 2 to 7 | default = 2

bits 5-3 | out div 2 | Secondary (user) clock DLL output divider (0 = thru; 1 = off; 2-7 = divide by 2 to 7 | default = 2

The reg_hkspi_pll_source register defines the values of the two output dividers associated with the DCO/DLL. The primary divider (div 1)
divides the DCO/DLL frequency down by the given value to generate the primary (core) clock for the processor. The secondary divider (div 2)
divides the DCO/DLL frequency down by the given value to generate the secondary (user) clock, which is passed directly to the user project as an independent clock that is independent of the core clock (wishbone clock). Note that value 0 is effectively divide-by-1 (pass-through), while value 1 disables the divider. The output dividers operate in both DCO and DLL modes.

reg_hkspi_pll_divider
0x26100027 | 0x26100026 | 0x26100025 | 0x26100024 | address
0x12 | SPI register
(undefined, reads zero) | feedback div | value
31 | 30 | 29 | 28 | 27 | 26 | 25 | 24 | 23 | 22 | 21 | 20 | 19 | 18 | 17 | 16 | 15 | 14 | 13 | 12 | 11 | 10 | 9 | 8 | 7 | 6 | 5 | 4 | 3 | 2 | 1 | 0 | bit
bits 4-0 | feedback div | DLL feedback divider. Values 1-31 = divide by 1 to 31 | default = 4

The reg_hkspi_pll_divider register defines the value of the feedback divider for the DLL. This divider value is only relevant when the DLL
mode is on (DCO mode off). The DLL will lock to a frequency that is the frequency of the external input clock multiplied by the feedback divider
value. The feedback divider value must be set such that the resulting DLL frequency is in the operational range of the DCO (which is 50MHz to 120MHz at 1.8V vccd supply). The value of the resulting clock when running in DLL mode can be computed as the external clock frequency times the feedback divider value, divided by the output divider value (see reg_hkspi_pll_source).

reg_power_good
0x26200003 | 0x26200002 | 0x26200001 | 0x26200000 | address
0x1A | SPI register
(undefined, reads zero) | power monitors | value
31 | 30 | 29 | 28 | 27 | 26 | 25 | 24 | 23 | 22 | 21 | 20 | 19 | 18 | 17 | 16 | 15 | 14 | 13 | 12 | 11 | 10 | 9 | 8 | 7 | 6 | 5 | 4 | 3 | 2 | 1 | 0 | bit

power monitors (4 bits) bit fields:
bit 0 | vdda2 power good | 1 = vdda2 (user 2 3.3V domain) powered up; 0 = vdda2 powered down | default = N/A
bit 1 | vdda1 power good | 1 = vdda1 (user 1 3.3V domain) powered up; 0 = vdda1 powered down | default = N/A
bit 2 | vccd2 power good | 1 = vccd2 (user 2 1.8V domain) powered up; 0 = vccd2 powered down | default = N/A
bit 3 | vccd1 power good | 1 = vccd1 (user 1 1.8V domain) powered up; 0 = vccd1 powered down | default = N/A

The reg_power_good read-only bits report the status of the power supply to the four independent user area power supplies. Note that these
are trivially simple power detectors and will read "1" whenever a supply is high enough to trip a digital buffer input, which is half of the nominal
power supply or less.

reg_clk_out_dest
0x26200007 | 0x26200006 | 0x26200005 | 0x26200004 | address
0x1B | SPI register
(undefined, reads zero) | monitors | value
31 | 30 | 29 | 28 | 27 | 26 | 25 | 24 | 23 | 22 | 21 | 20 | 19 | 18 | 17 | 16 | 15 | 14 | 13 | 12 | 11 | 10 | 9 | 8 | 7 | 6 | 5 | 4 | 3 | 2 | 1 | 0 | bit

monitors bit fields:
bit 0 | trap monitor | 1 = Moniitor CPU trap state on GPIO[13] (unavailable on current caravel version) | default = 0
bit 1 | core clock monitor | 1 = Monitor core clock on GPIO[14] | default = 0
bit 2 | user clock monitor | 1 = Monitor secondary (user) clock on GPIO[15] | default = 0

The reg_clk_out_dest monitoring functions allow either or both of the core clock and the user clock to be routed to a GPIO pin for monitoring.
Specific GPIO pins (14 and 15) are assigned to these functions.

reg_irq_source
0x2620000F | 0x2620000E | 0x2620000D | 0x2620000C | address
0x1C | SPI register
(undefined, reads zero) | source | value
31 | 30 | 29 | 28 | 27 | 26 | 25 | 24 | 23 | 22 | 21 | 20 | 19 | 18 | 17 | 16 | 15 | 14 | 13 | 12 | 11 | 10 | 9 | 8 | 7 | 6 | 5 | 4 | 3 | 2 | 1 | 0 | bit

source bit fields:
bit 0 | IRQ 1 source | 1 = Enable pin GPIO[7] as IRQ[1] input source | default = 0
bit 1 | IRQ 2 source | 1 = Enable pin GPIO[12] as IRQ[2] input source | default = 0

The reg_irq_source register controls the enablement of special-purpose GPIO pins (7 and/or 12) to be used for external interrupts to the
processor from an off-chip source.

reg_hkspi_disable
0x26200013 | 0x26200012 | 0x26200011 | 0x26200010 | address
0x6F | SPI register
(undefined, reads zero) | DIS | value
31 | 30 | 29 | 28 | 27 | 26 | 25 | 24 | 23 | 22 | 21 | 20 | 19 | 18 | 17 | 16 | 15 | 14 | 13 | 12 | 11 | 10 | 9 | 8 | 7 | 6 | 5 | 4 | 3 | 2 | 1 | 0 | bit
bit 0 | DIS | Disable the housekeeping SPI. 1 = SPI disabled; 0 = SPI enabled | default = 0

The reg_hkspi_disable register contains a single bit that will disable the special function of the housekeeping SPI. The housekeeping SPI
should be disabled whenever GPIO pins 1 to 4 are used for any purpose other than the housekeeping SPI interface. Otherwise, the CSB pin
(GPIO 3) can trigger an action on the SPI, which may then attempt to apply an output value to SDO (GPIO 1).
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
