efabless/caravel_board/hardware/development/caravel_pcb_v4_FTDI/caravel_pcb_v4_FTDI.pdf

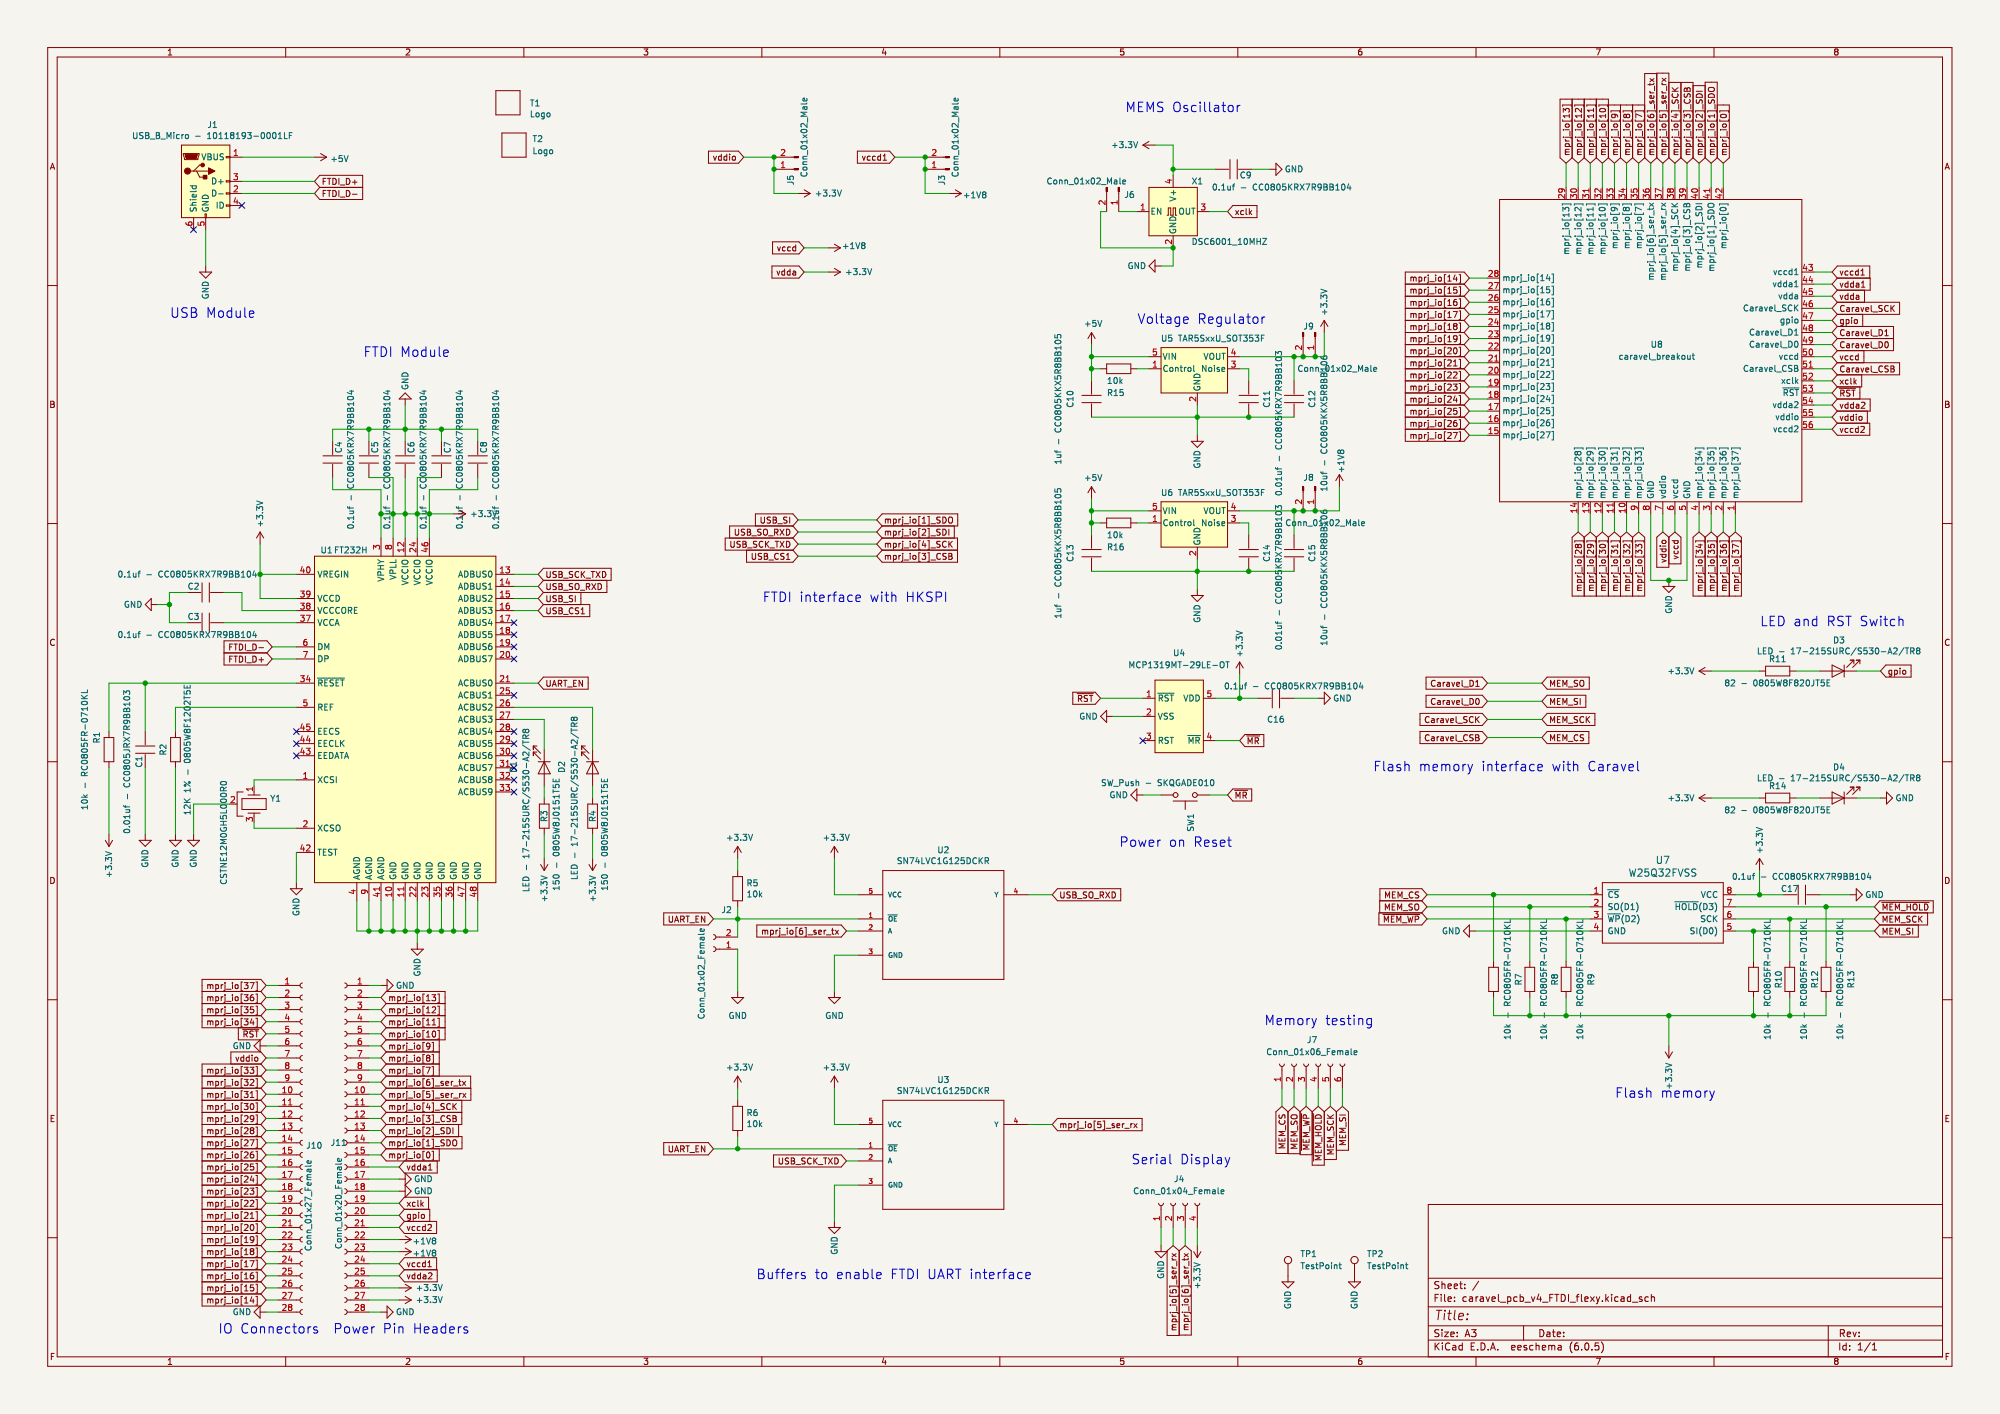
[picture p91: page 1]
