efabless/caravel_board/hardware/breakout/caravel_breakout_v2/Caravel_breakout_v2.pdf

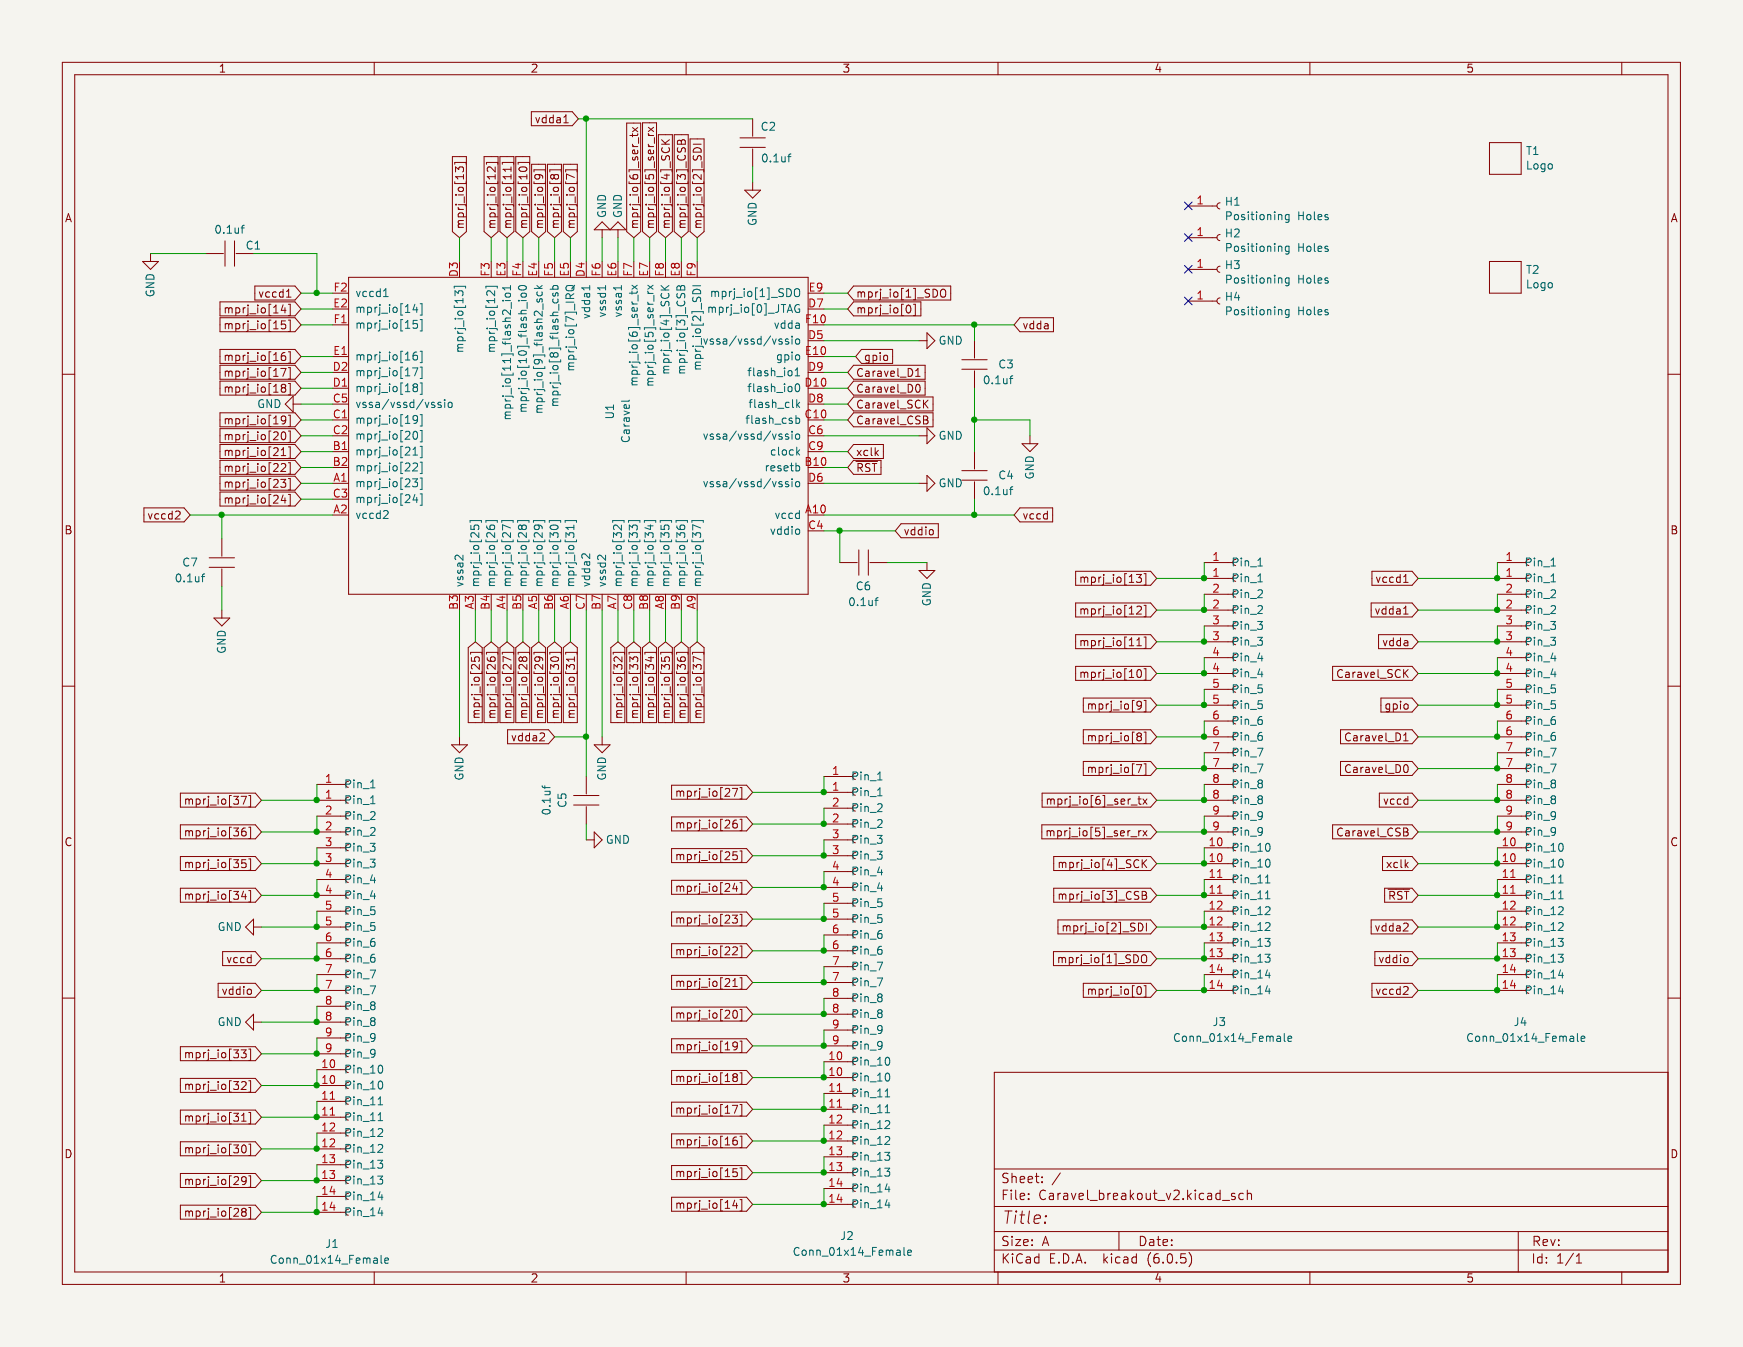
[picture p92: page 1]
