efabless/caravel_board/hardware/development/caravel_pcb_v3_MCP/caravel_pcb_v3_MCP.pdf

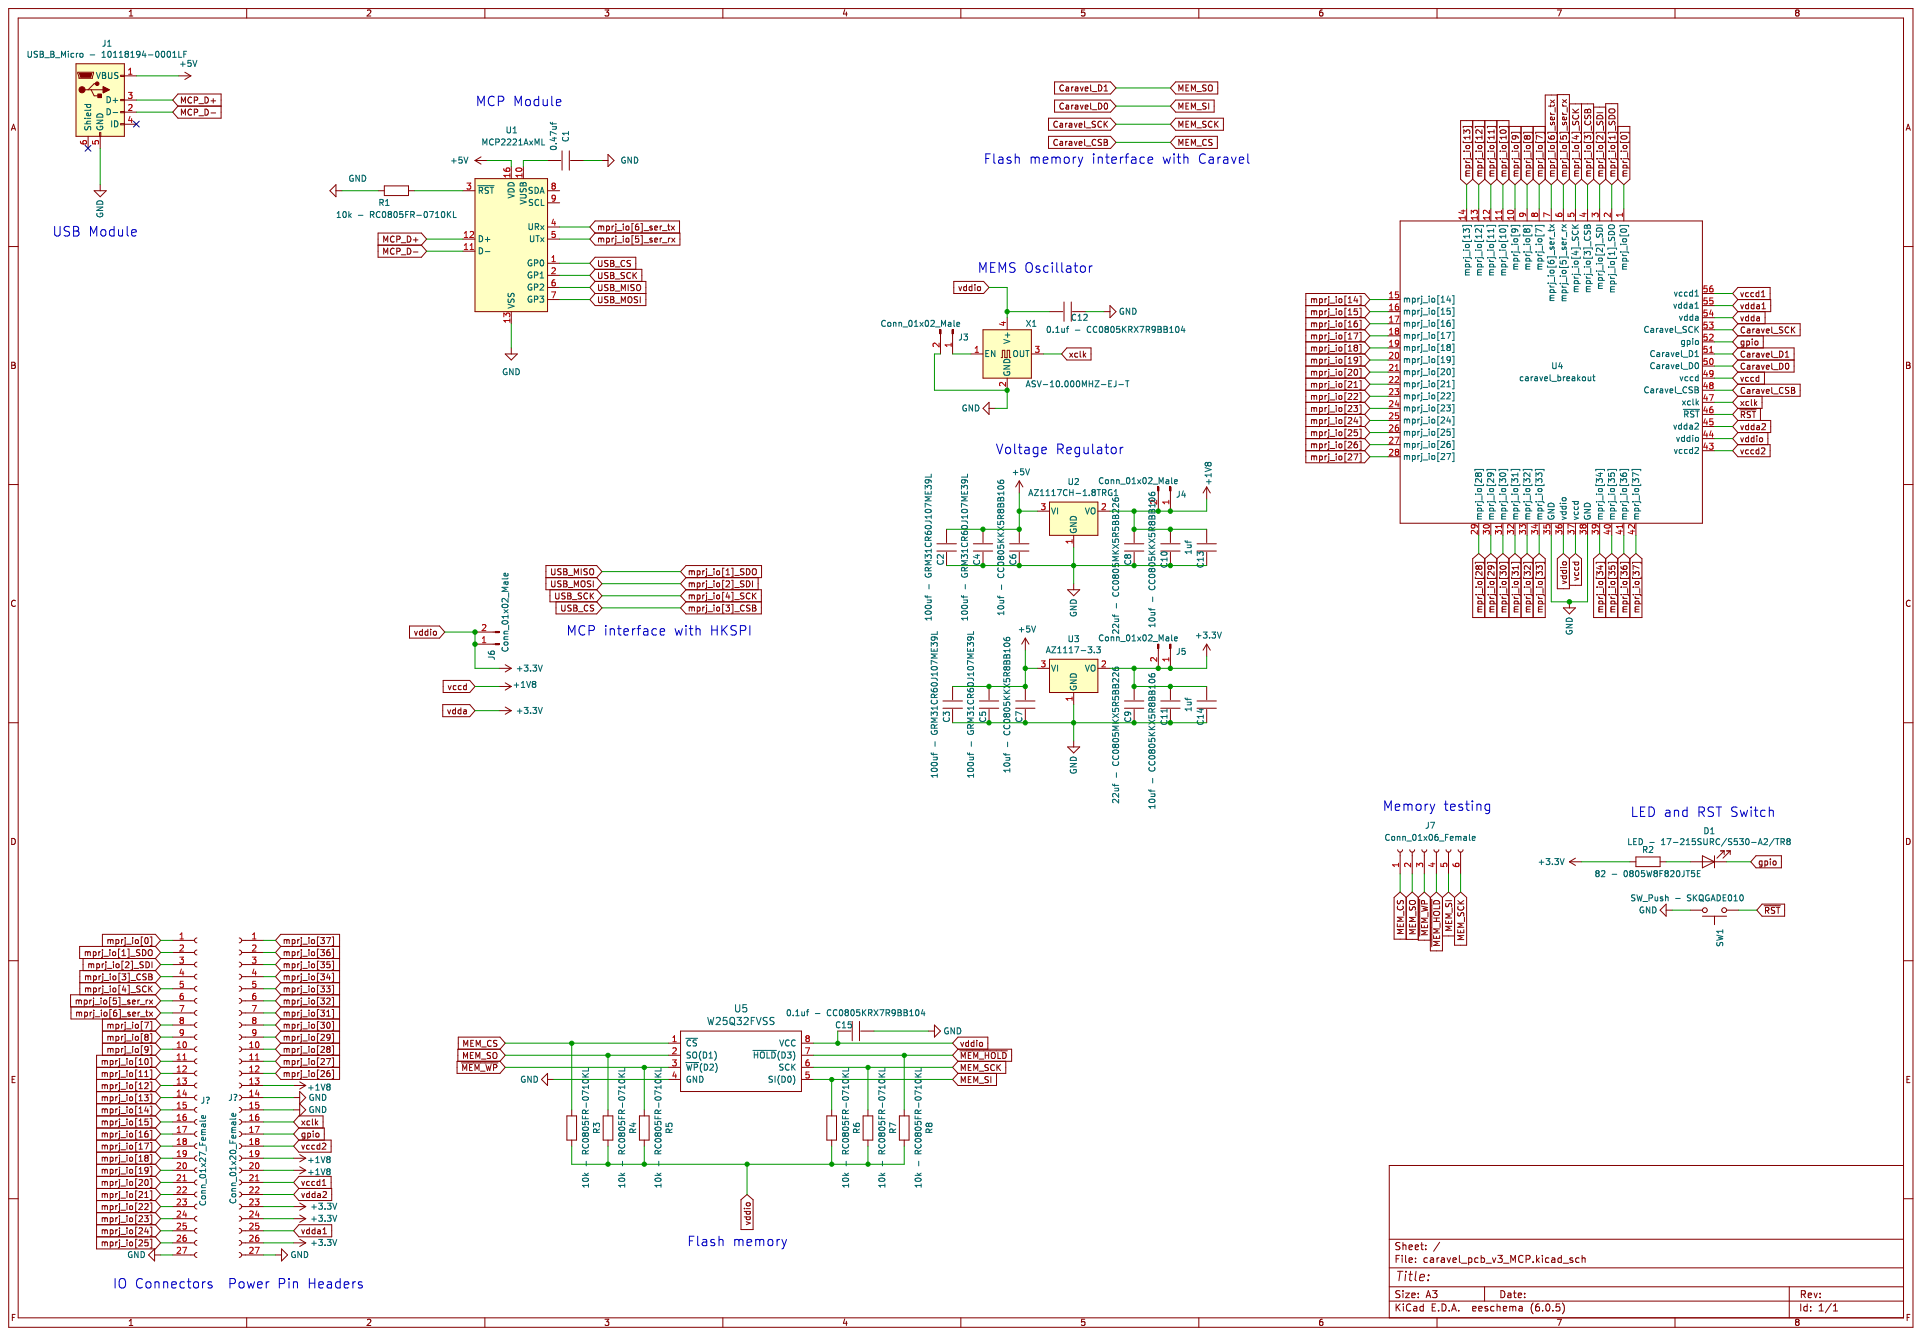
[picture p93: page 1]
