efabless/caravel_board/hardware/development/caravel_pcb_v2/gerbers/Caravel_pcb-F_Cu.pdf

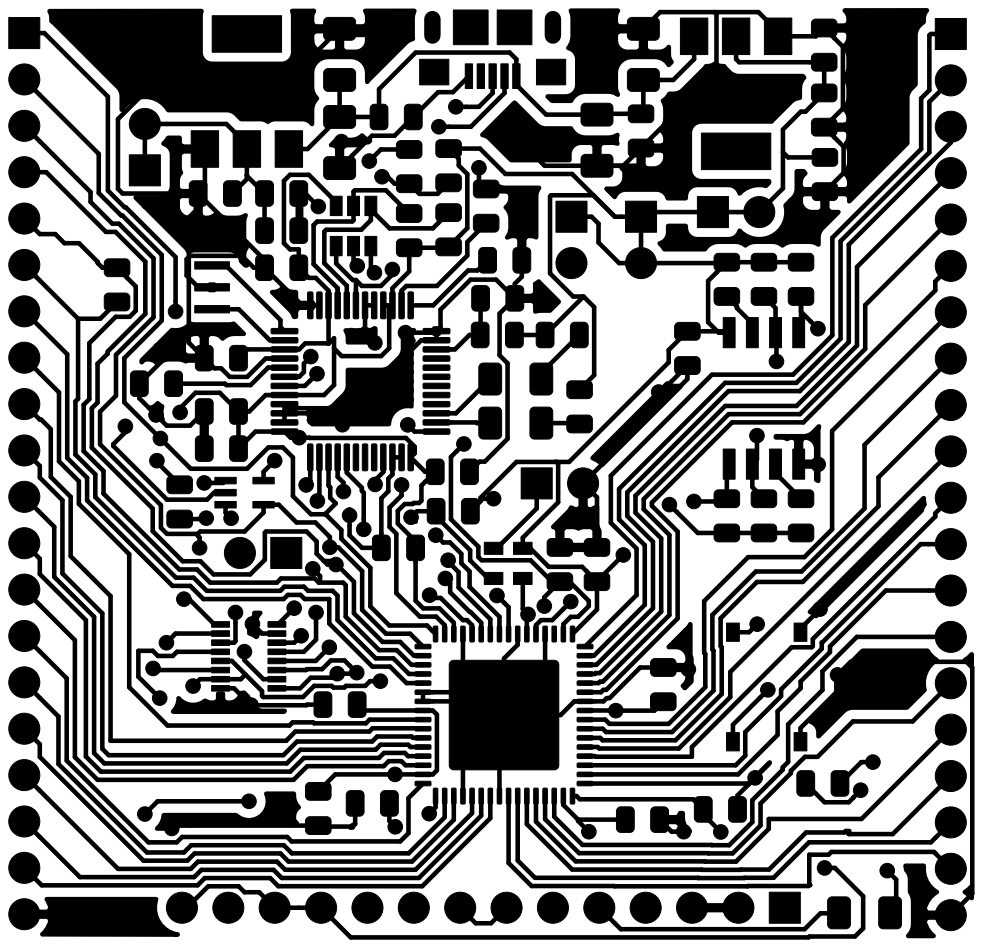
[picture p94: page 1]
