efabless/caravel_board/hardware/development/_archive/caravel_pcb_v3_FTDI/caravel_pcb_v3_FTDI.pdf

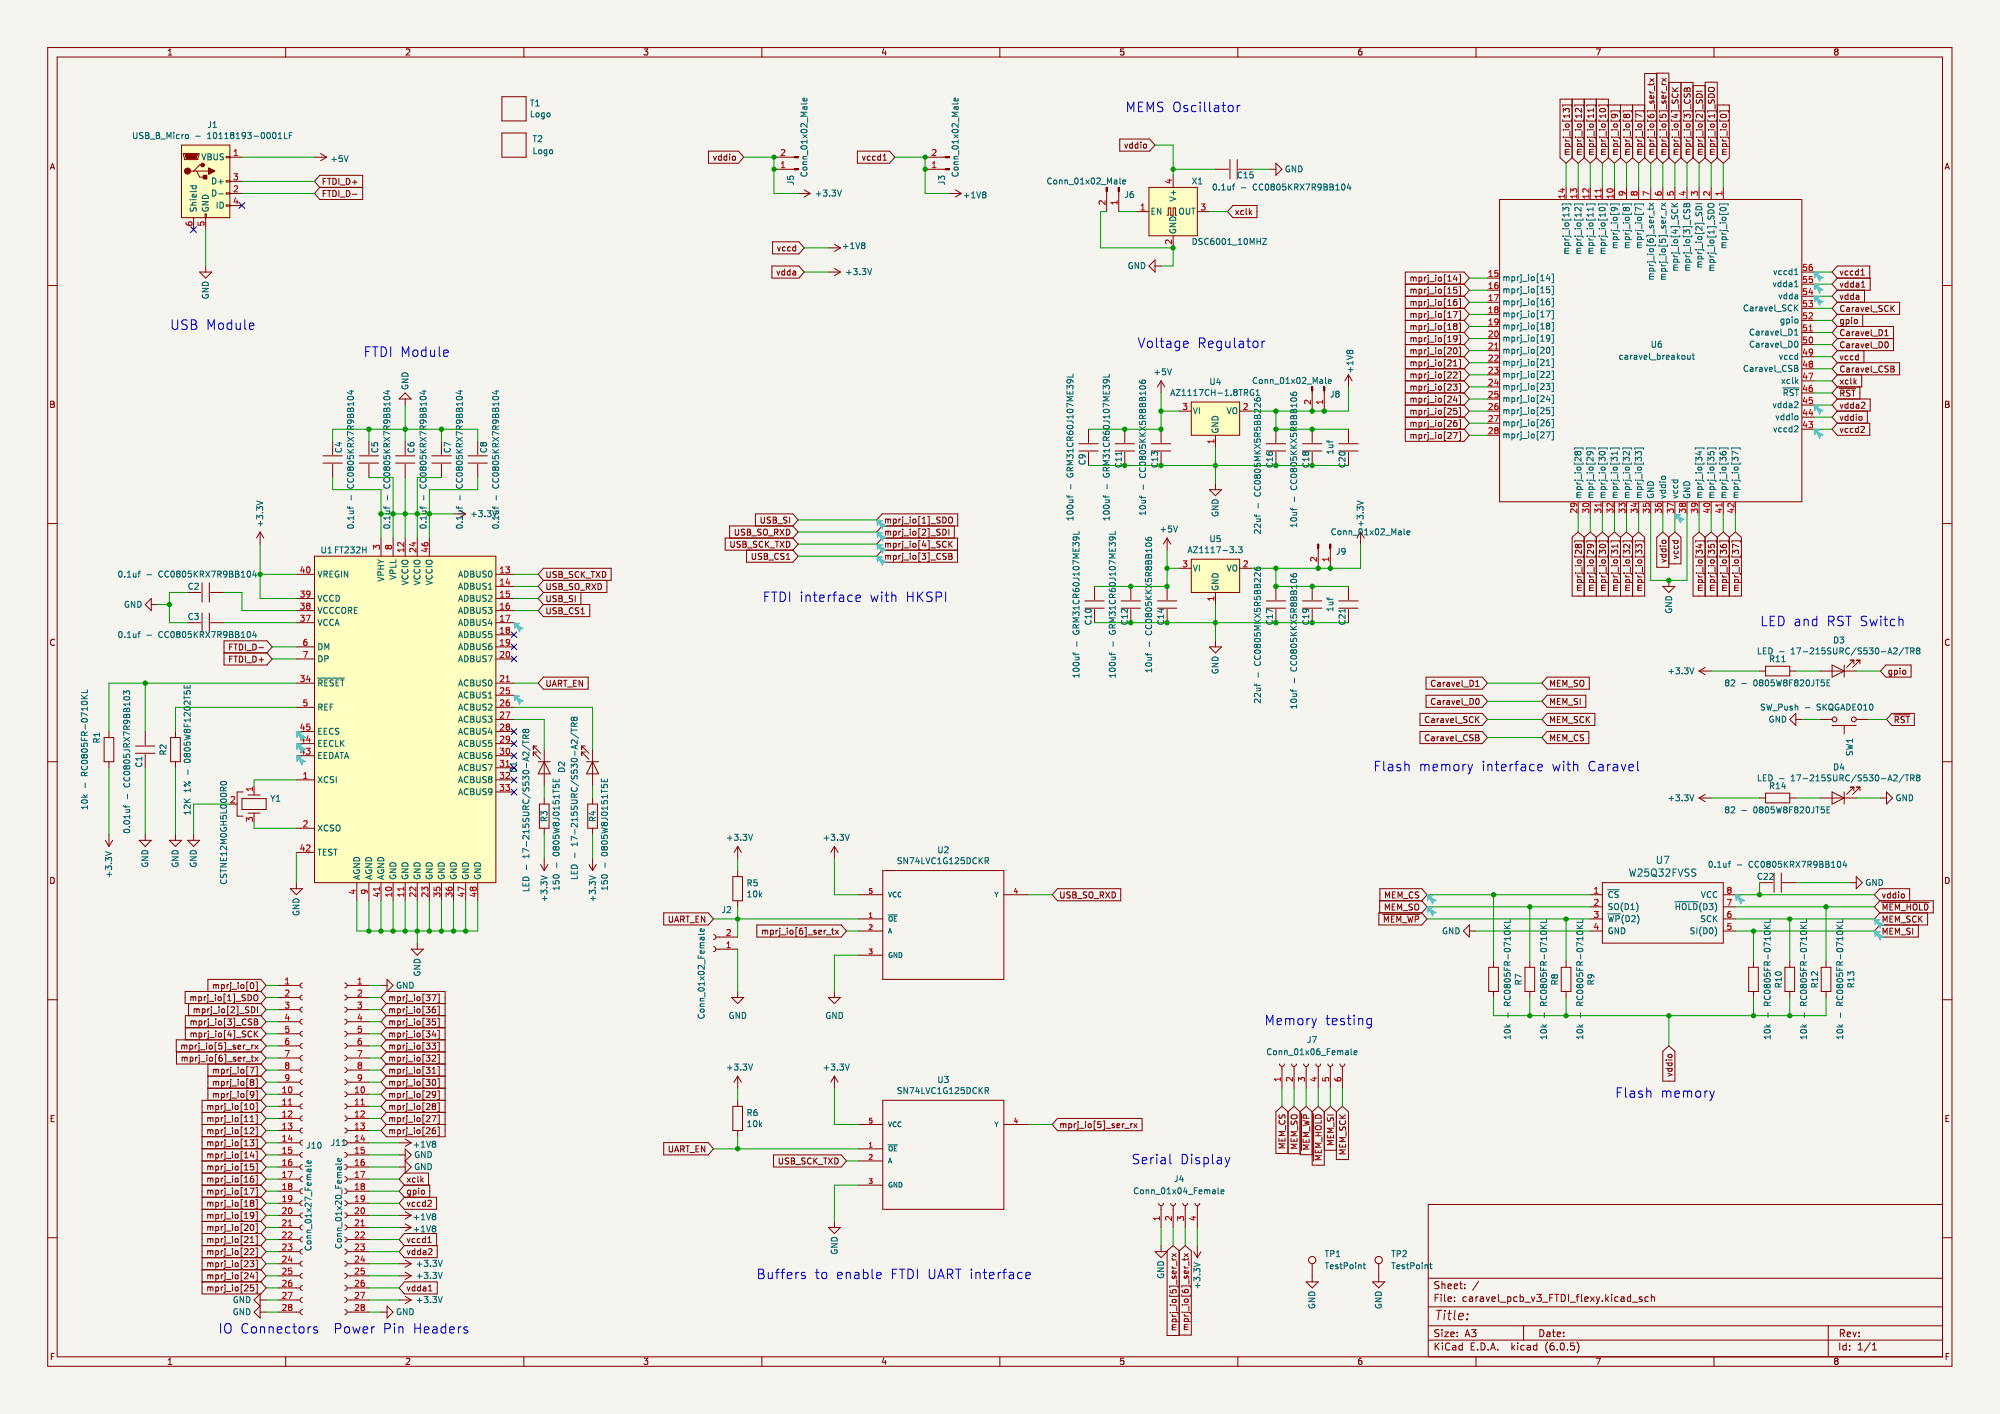
[picture p95: page 1]
