efabless/caravel_board/hardware/breakout/_archive/caravel_breakout_v1/Caravel_breakout.pdf

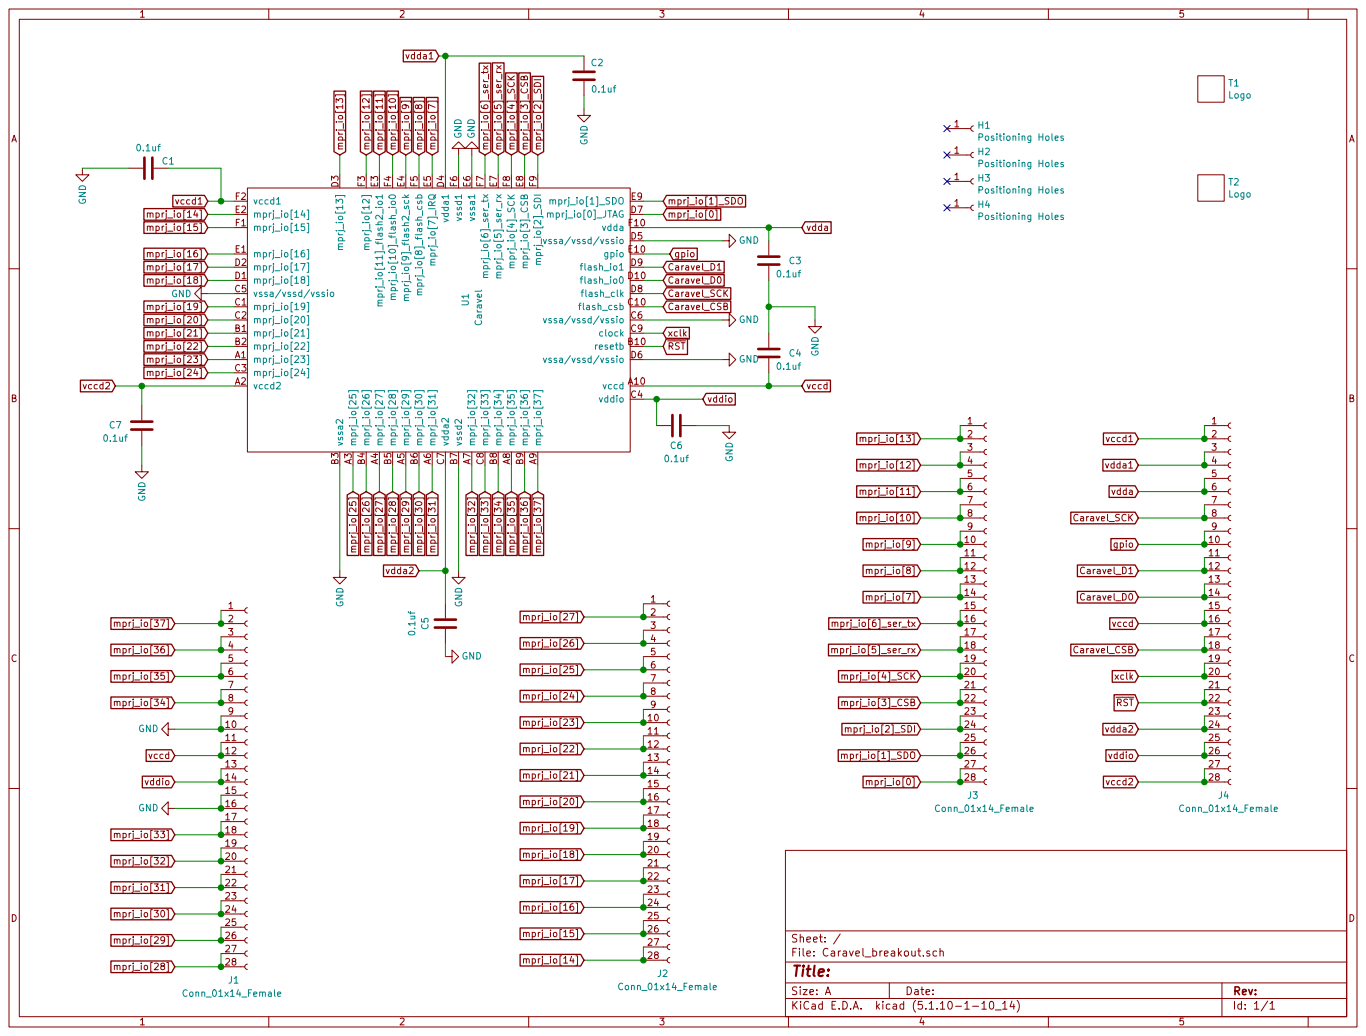
[picture p96: page 1]
