efabless/caravel_board/hardware/development/_archive/caravel_pcb_v1/Caravel_pcb.kicad_pcb

## KiCad design hardware/development/_archive/caravel_pcb_v1/Caravel_pcb.kicad_pcb (2021-10-22, an earlier design)

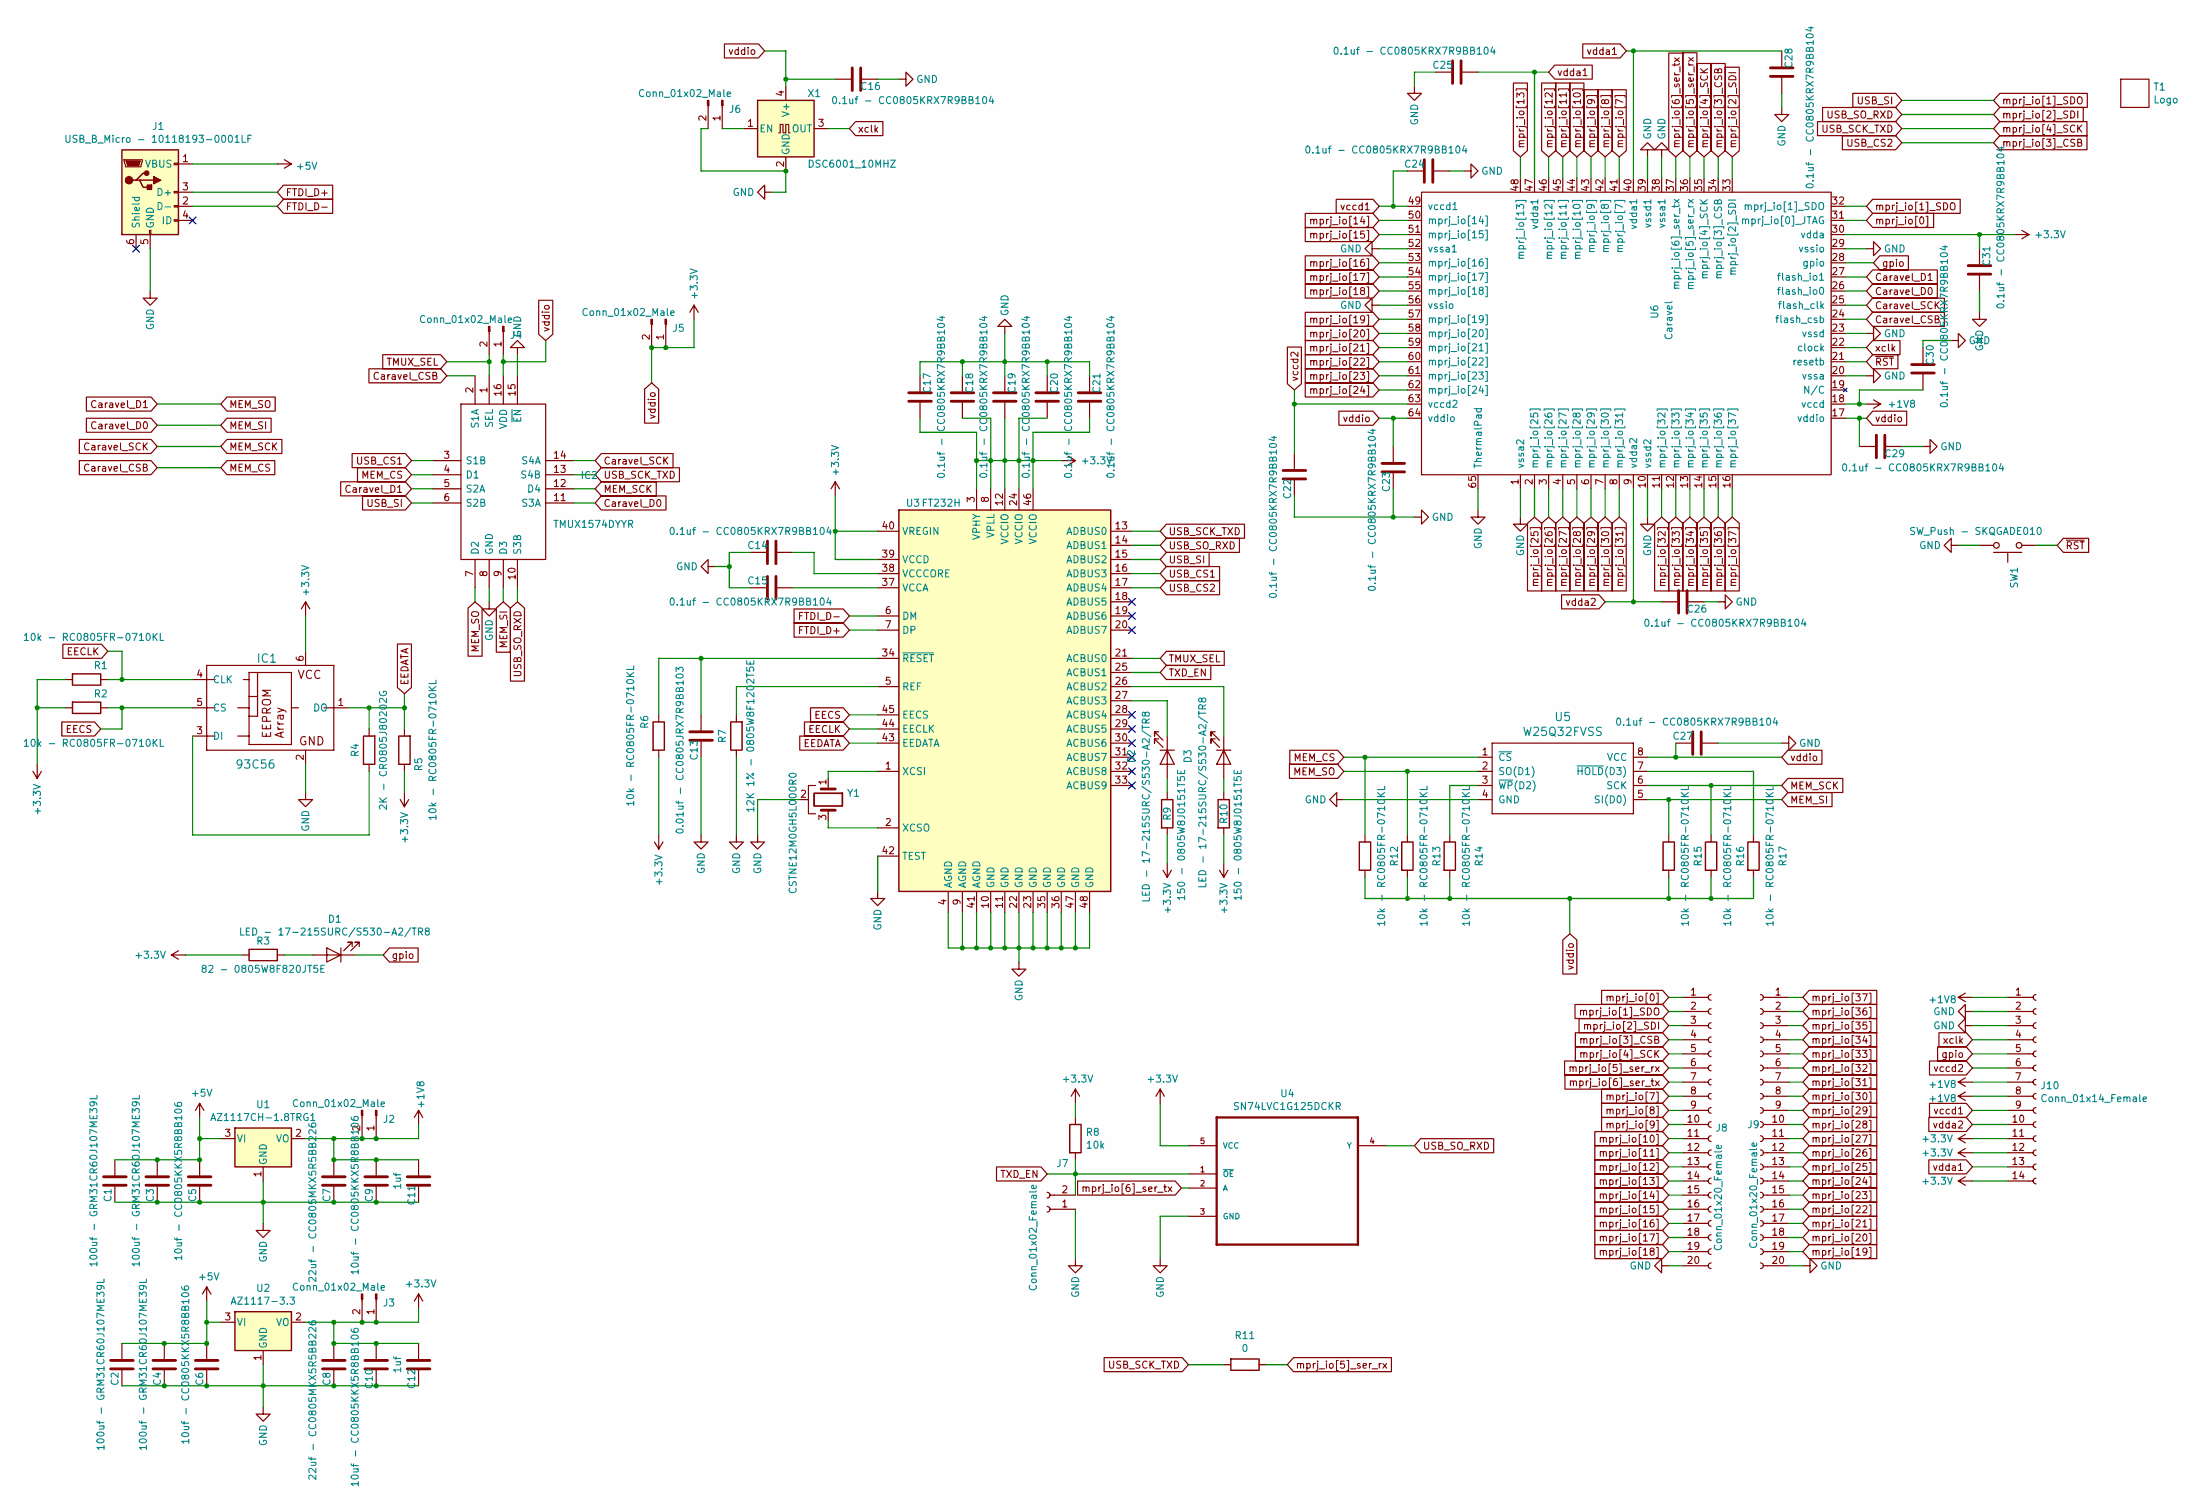
[picture p113: schematic Caravel_pcb.sch]

Parts:
C1, C2, C3, C4: 100uf - GRM31CR60J107ME39L; C_1206_3216Metric
C5, C6, C9, C10: 10uf - CC0805KKX5R8BB106; C_0805_2012Metric
C7, C8: 22uf - CC0805MKX5R5BB226; C_0805_2012Metric
C11, C12: 1uf; C_0805_2012Metric
C13: 0.01uf - CC0805JRX7R9BB103; C_0805_2012Metric
C14, C15, C16, C17, C18, C19, C20, C21, C22, C23, C24, C25, C26, C27, C28, C29, C30, C31: 0.1uf - CC0805KRX7R9BB104; C_0805_2012Metric
D1, D2, D3: LED - 17-215SURC/S530-A2/TR8; LED_1206_3216Metric
IC1: 93C56; SOT-23-6
IC2: TMUX1574DYYR; Mouser Part Number 595-TMUX1574RSVR
J1: USB_B_Micro - 10118193-0001LF; FCI_10118193-0001LF
J2, J3, J4, J5, J6: Conn_01x02_Male; PinHeader_1x02_P2.54mm_Vertical
J7: Conn_01x02_Female; PinHeader_1x02_P2.54mm_Vertical
J8, J9: Conn_01x20_Female; PinHeader_1x20_P2.54mm_Vertical
J10: Conn_01x14_Female; PinHeader_1x14_P2.54mm_Vertical
R1, R2, R5, R6, R12, R13, R14, R15, R16, R17: 10k - RC0805FR-0710KL; R_0805_2012Metric
R3: 82 - 0805W8F820JT5E; R_0805_2012Metric
R4: 2K - CR0805J80202G; R_0805_2012Metric
R7: 12K 1% - 0805W8F1202T5E; R_0805_2012Metric
R8: 10k; R_0805_2012Metric
R9, R10: 150 - 0805W8J0151T5E; R_0805_2012Metric
R11: 0; R_0805_2012Metric
SW1: SW_Push - SKQGADE010; SW4-SMD-5.2X5.2X1.5MM
T1: Logo; logo
U1: AZ1117CH-1.8TRG1; SOT-223
U2: AZ1117-3.3; SOT-223
U3: FT232H; LQFP-48_7x7mm_P0.5mm
U4: SN74LVC1G125DCKR; SOT65P210X110-5N
U5: W25Q32FVSS; SOIC127P790X216-8N
U6: Caravel; QFN-64-1EP_9x9mm_P0.5mm_EP6x6mm
X1: DSC6001_10MHZ; DSC6001JE1A-010.0000
Y1: CSTNE12M0GH5L000R0

Connections:
+1V8: C7.2, C9.2, C11.2, C30.2, J2.1, J2.2, J10.1, J10.7, J10.8, U1.2 (VO), U6.18 (vccd)
+5V: C1.2, C2.2, C3.2, C4.2, C5.2, C6.2, J1.1 (VBUS), U1.3 (VI), U2.3 (VI)
Caravel_CSB: IC2.2 (S1A), IC2.4 (D1), R12.1, U5.1 (~CS~), U6.24 (flash_csb)
Caravel_D0: IC2.9 (D3), IC2.11 (S3A), R15.1, U5.5 (SI(D0)), U6.26 (flash_io0)
Caravel_D1: IC2.5 (S2A), IC2.7 (D2), R13.1, U5.2 (SO(D1)), U6.27 (flash_io1)
Caravel_SCK: IC2.12 (D4), IC2.14 (S4A), R16.1, U5.6 (SCK), U6.25 (flash_clk)
EECLK: IC1.4 (CLK), R1.1, U3.44 (EECLK)
EECS: IC1.5 (CS), R2.1, U3.45 (EECS)
EEDATA: IC1.1 (DO), R4.2, R5.2, U3.43 (EEDATA)
FTDI_D+: J1.3 (D+), U3.7 (DP)
FTDI_D-: J1.2 (D-), U3.6 (DM)
GND: C1.1, C2.1, C3.1, C4.1, C5.1, C6.1, C7.1, C8.1, C9.1, C10.1, C11.1, C12.1, C13.1, C14.1, C15.1, C16.1, C17.1, C18.1, C19.1, C20.1, C21.1, C22.1, C23.1, C24.2, C25.1, C26.1, C27.2, C28.2, C29.1, C30.1, C31.2, IC1.2 (GND), IC2.8 (GND), IC2.15 (~EN), J1.5 (GND), J6.2, J7.1, J8.20, J9.20, J10.2, J10.3, R7.1, SW1.2, U1.1 (GND), U2.1 (GND), U3.4 (AGND), U3.9 (AGND), U3.10 (GND), U3.11 (GND), U3.22 (GND), U3.23 (GND), U3.35 (GND), U3.36 (GND), U3.41 (AGND), U3.42 (TEST), U3.47 (GND), U3.48 (GND), U4.3 (GND), U5.4 (GND), U6.1 (vssa2), U6.10 (vssd2), U6.20 (vssa), U6.23 (vssd), U6.29 (vssio), U6.38 (vssa1), U6.39 (vssd1), U6.52 (vssa1), U6.56 (vssio), U6.65 (ThermalPad), X1.2 (GND), Y1.2
unnamed: C13.2, R6.1, U3.34 (~RESET)
unnamed: C14.2, U3.38 (VCCCORE)
unnamed: C15.2, U3.37 (VCCA)
unnamed: D1.2 (A), R3.2
unnamed: D2.1 (K), U3.27 (ACBUS3)
unnamed: D2.2 (A), R9.1
unnamed: D3.1 (K), U3.26 (ACBUS2)
unnamed: D3.2 (A), R10.1
unnamed: IC1.3 (DI), R4.1
unnamed: J6.1, X1.1 (EN)
unnamed: R7.2, U3.5 (REF)
unnamed: R14.1, U5.3 (~WP~(D2))
unnamed: R17.1, U5.7 (~HOLD~(D3))
unnamed: U3.1 (XCSI), Y1.1
unnamed: U3.2 (XCSO), Y1.3
TMUX_SEL: IC2.1 (SEL), J4.2, U3.21 (ACBUS0)
TXD_EN: J7.2, R8.2, U3.25 (ACBUS1), U4.1 (~OE)
USB_CS1: IC2.3 (S1B), U3.16 (ADBUS3)
USB_CS2: J8.4, U3.17 (ADBUS4), U6.34 (mprj_io[3]_CSB)
USB_SCK_TXD: IC2.13 (S4B), J8.5, R11.2, U3.13 (ADBUS0), U6.35 (mprj_io[4]_SCK)
USB_SI: IC2.6 (S2B), J8.2, U3.15 (ADBUS2), U6.32 (mprj_io[1]_SDO)
USB_SO_RXD: IC2.10 (S3B), J8.3, U3.14 (ADBUS1), U4.4 (Y), U6.33 (mprj_io[2]_SDI)
gpio: D1.1 (K), J10.5, U6.28 (gpio)
mprj_io[0]: J8.1, U6.31 (mprj_io[0]_JTAG)
mprj_io[5]_ser_rx: J8.6, R11.1, U6.36 (mprj_io[5]_ser_rx)
mprj_io[6]_ser_tx: J8.7, U4.2 (A), U6.37 (mprj_io[6]_ser_tx)
mprj_io[7]: J8.8, U6.41 (mprj_io[7])
mprj_io[8]: J8.9, U6.42 (mprj_io[8])
mprj_io[9]: J8.10, U6.43 (mprj_io[9])
mprj_io[10]: J8.11, U6.44 (mprj_io[10])
mprj_io[11]: J8.12, U6.45 (mprj_io[11])
mprj_io[12]: J8.13, U6.46 (mprj_io[12])
mprj_io[13]: J8.14, U6.48 (mprj_io[13])
mprj_io[14]: J8.15, U6.50 (mprj_io[14])
mprj_io[15]: J8.16, U6.51 (mprj_io[15])
mprj_io[16]: J8.17, U6.53 (mprj_io[16])
mprj_io[17]: J8.18, U6.54 (mprj_io[17])
mprj_io[18]: J8.19, U6.55 (mprj_io[18])
mprj_io[19]: J9.19, U6.57 (mprj_io[19])
mprj_io[20]: J9.18, U6.58 (mprj_io[20])
mprj_io[21]: J9.17, U6.59 (mprj_io[21])
mprj_io[22]: J9.16, U6.60 (mprj_io[22])
mprj_io[23]: J9.15, U6.61 (mprj_io[23])
mprj_io[24]: J9.14, U6.62 (mprj_io[24])
mprj_io[25]: J9.13, U6.2 (mprj_io[25])
mprj_io[26]: J9.12, U6.3 (mprj_io[26])
mprj_io[27]: J9.11, U6.4 (mprj_io[27])
mprj_io[28]: J9.10, U6.5 (mprj_io[28])
mprj_io[29]: J9.9, U6.6 (mprj_io[29])
mprj_io[30]: J9.8, U6.7 (mprj_io[30])
mprj_io[31]: J9.7, U6.8 (mprj_io[31])
mprj_io[32]: J9.6, U6.11 (mprj_io[32])
mprj_io[33]: J9.5, U6.12 (mprj_io[33])
mprj_io[34]: J9.4, U6.13 (mprj_io[34])
mprj_io[35]: J9.3, U6.14 (mprj_io[35])
mprj_io[36]: J9.2, U6.15 (mprj_io[36])
mprj_io[37]: J9.1, U6.16 (mprj_io[37])
vccd1: C24.1, J10.9, U6.49 (vccd1)
vccd2: C22.2, J10.6, U6.63 (vccd2)
vdda1: C25.2, C28.1, J10.13, U6.40 (vdda1), U6.47 (vdda1)
vdda2: C26.2, J10.10, U6.9 (vdda2)
vddio: C8.2, C10.2, C12.2, C16.2, C17.2, C18.2, C19.2, C20.2, C21.2, C23.2, C27.1, C29.2, C31.1, IC1.6 (VCC), IC2.16 (VDD), J3.1, J3.2, J4.1, J5.1, J5.2, J10.11, J10.12, J10.14, R1.2, R2.2, R3.1, R5.1, R6.2, R8.1, R9.2, R10.2, R12.2, R13.2, R14.2, R15.2, R16.2, R17.2, U2.2 (VO), U3.3 (VPHY), U3.8 (VPLL), U3.12 (VCCIO), U3.24 (VCCIO), U3.39 (VCCD), U3.40 (VREGIN), U3.46 (VCCIO), U4.5 (VCC), U5.8 (VCC), U6.17 (vddio), U6.30 (vdda), U6.64 (vddio), X1.4 (V+)
xclk: J10.4, U6.22 (clock), X1.3 (OUT)
~RST: SW1.1, U6.21 (resetb)

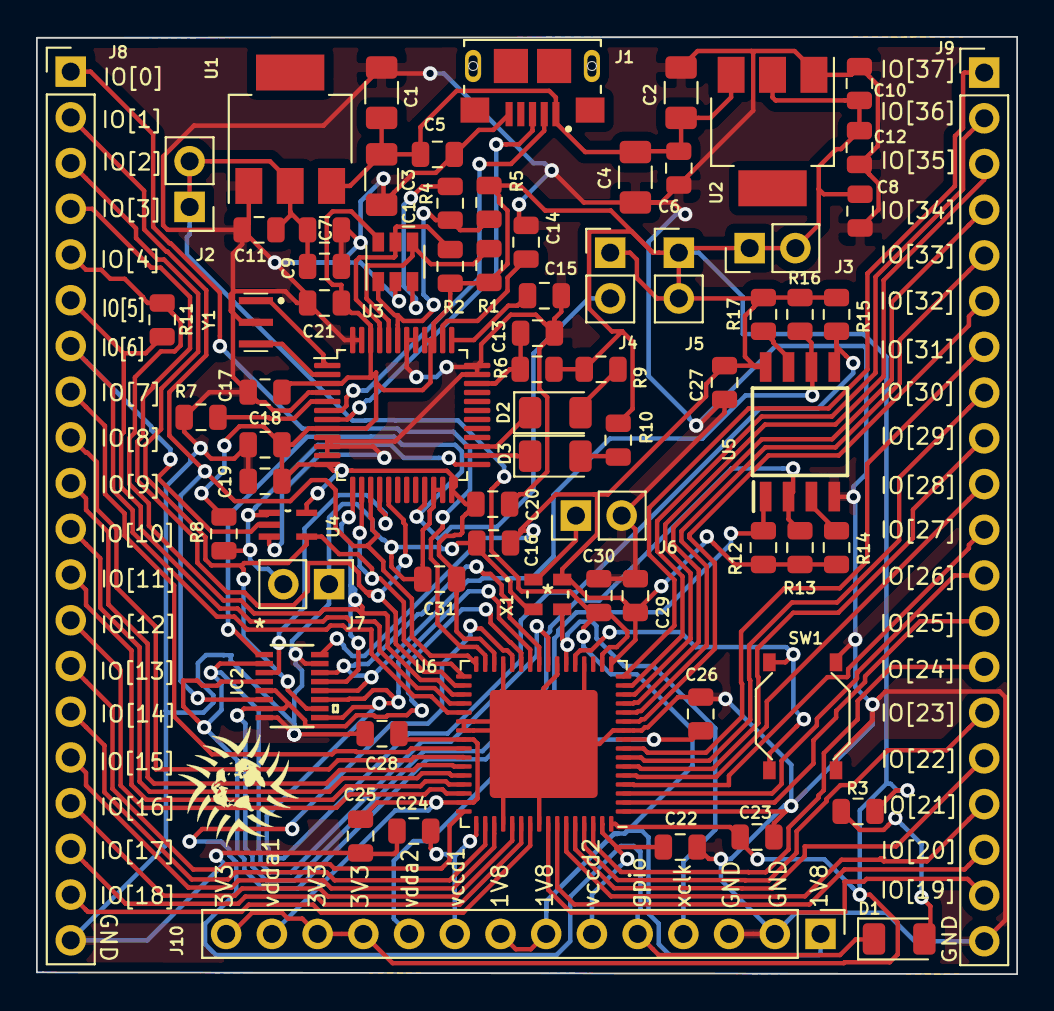
[picture p114: board Caravel_pcb.kicad_pcb from above]

Board: 2 copper layers, 54.5 x 52.1 mm, 73 parts (0 on the bottom side), 76 nets.
