efabless/caravel_board/hardware/nucleo/caravel-Nucleo-v2-M.2/caravel-Nucleo-v2-M.2.kicad_pcb

## KiCad design hardware/nucleo/caravel-Nucleo-v2-M.2/caravel-Nucleo-v2-M.2.kicad_pcb (2023-04-04)

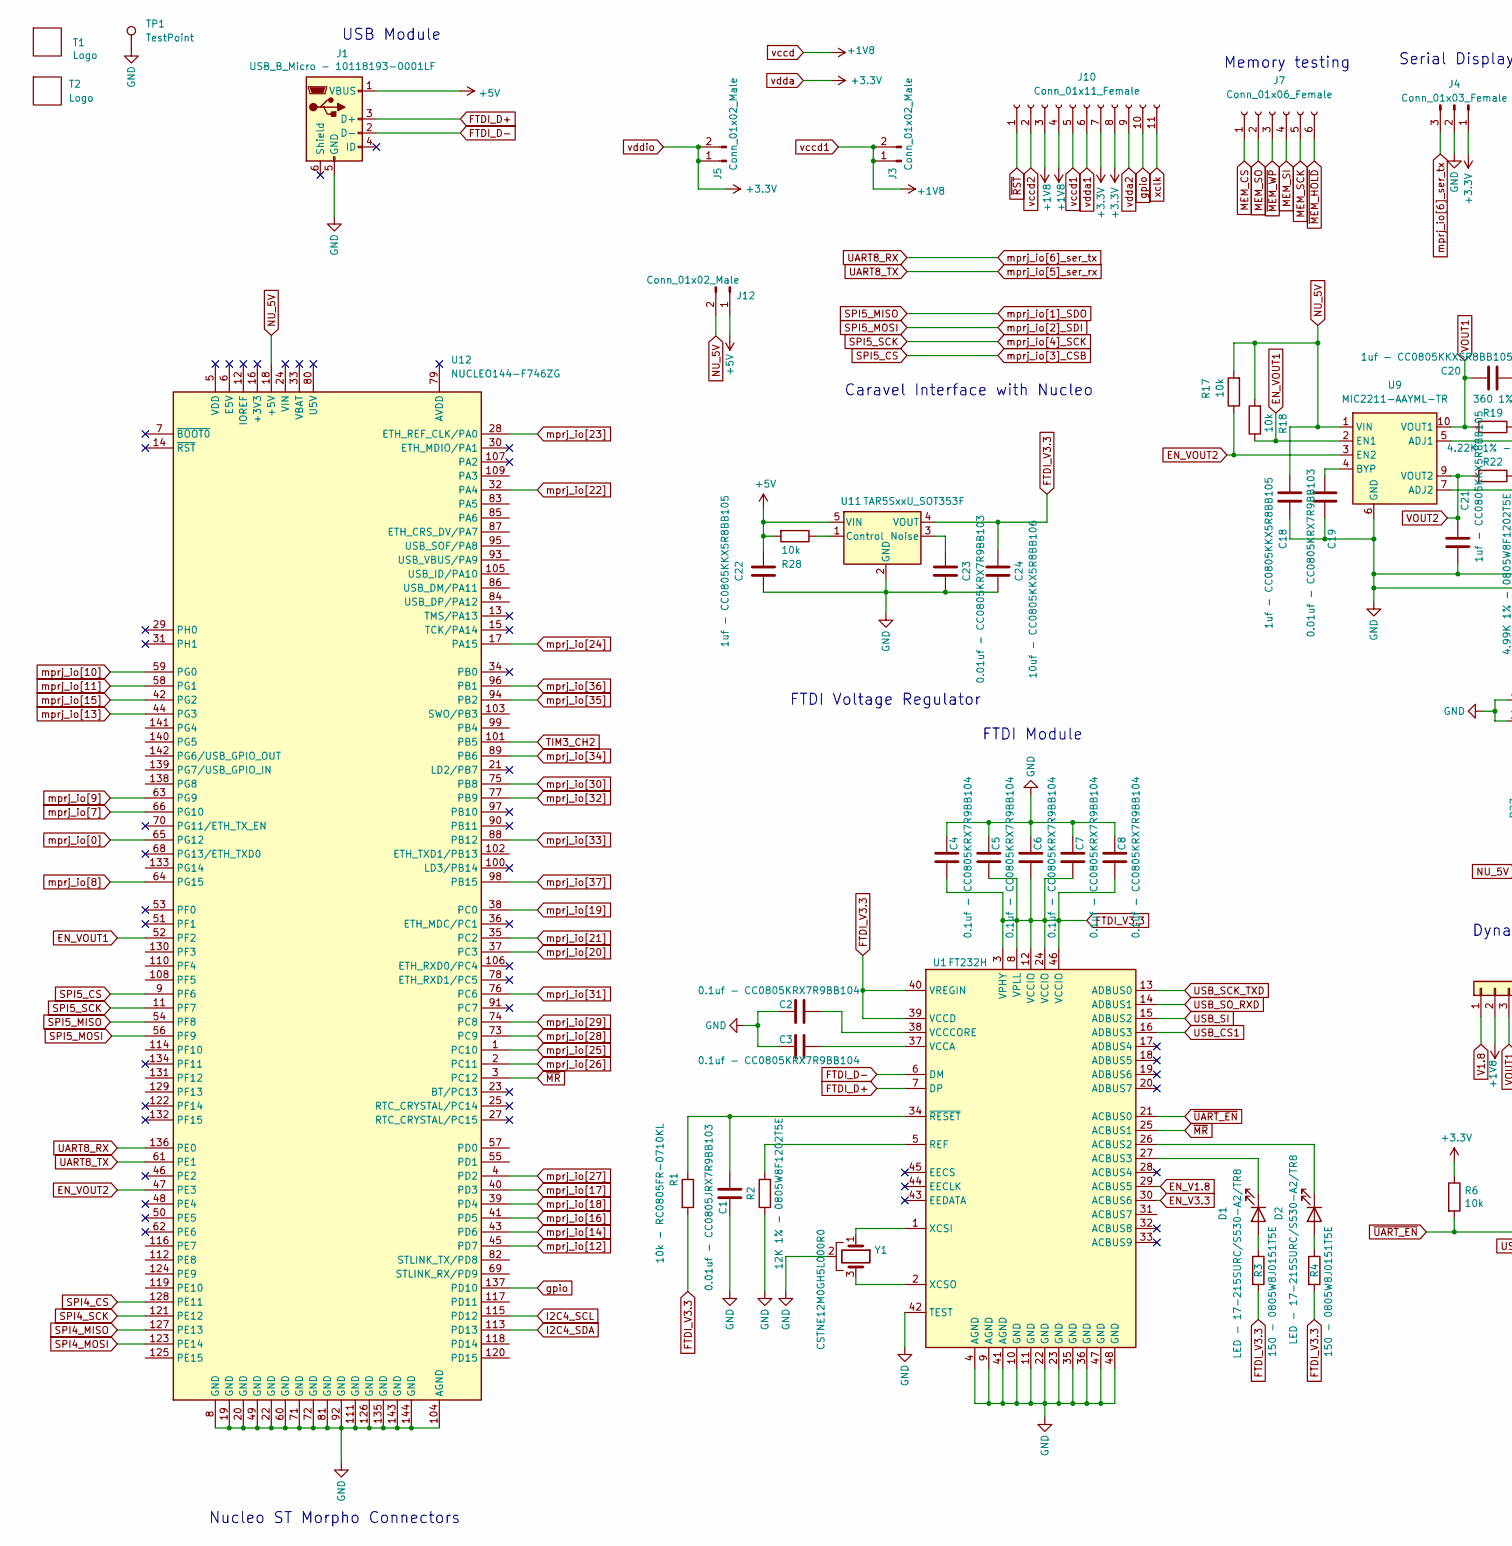
[picture p115: schematic caravel-Nucleo-v2-M.2.kicad_sch, part in row 1, column 1]

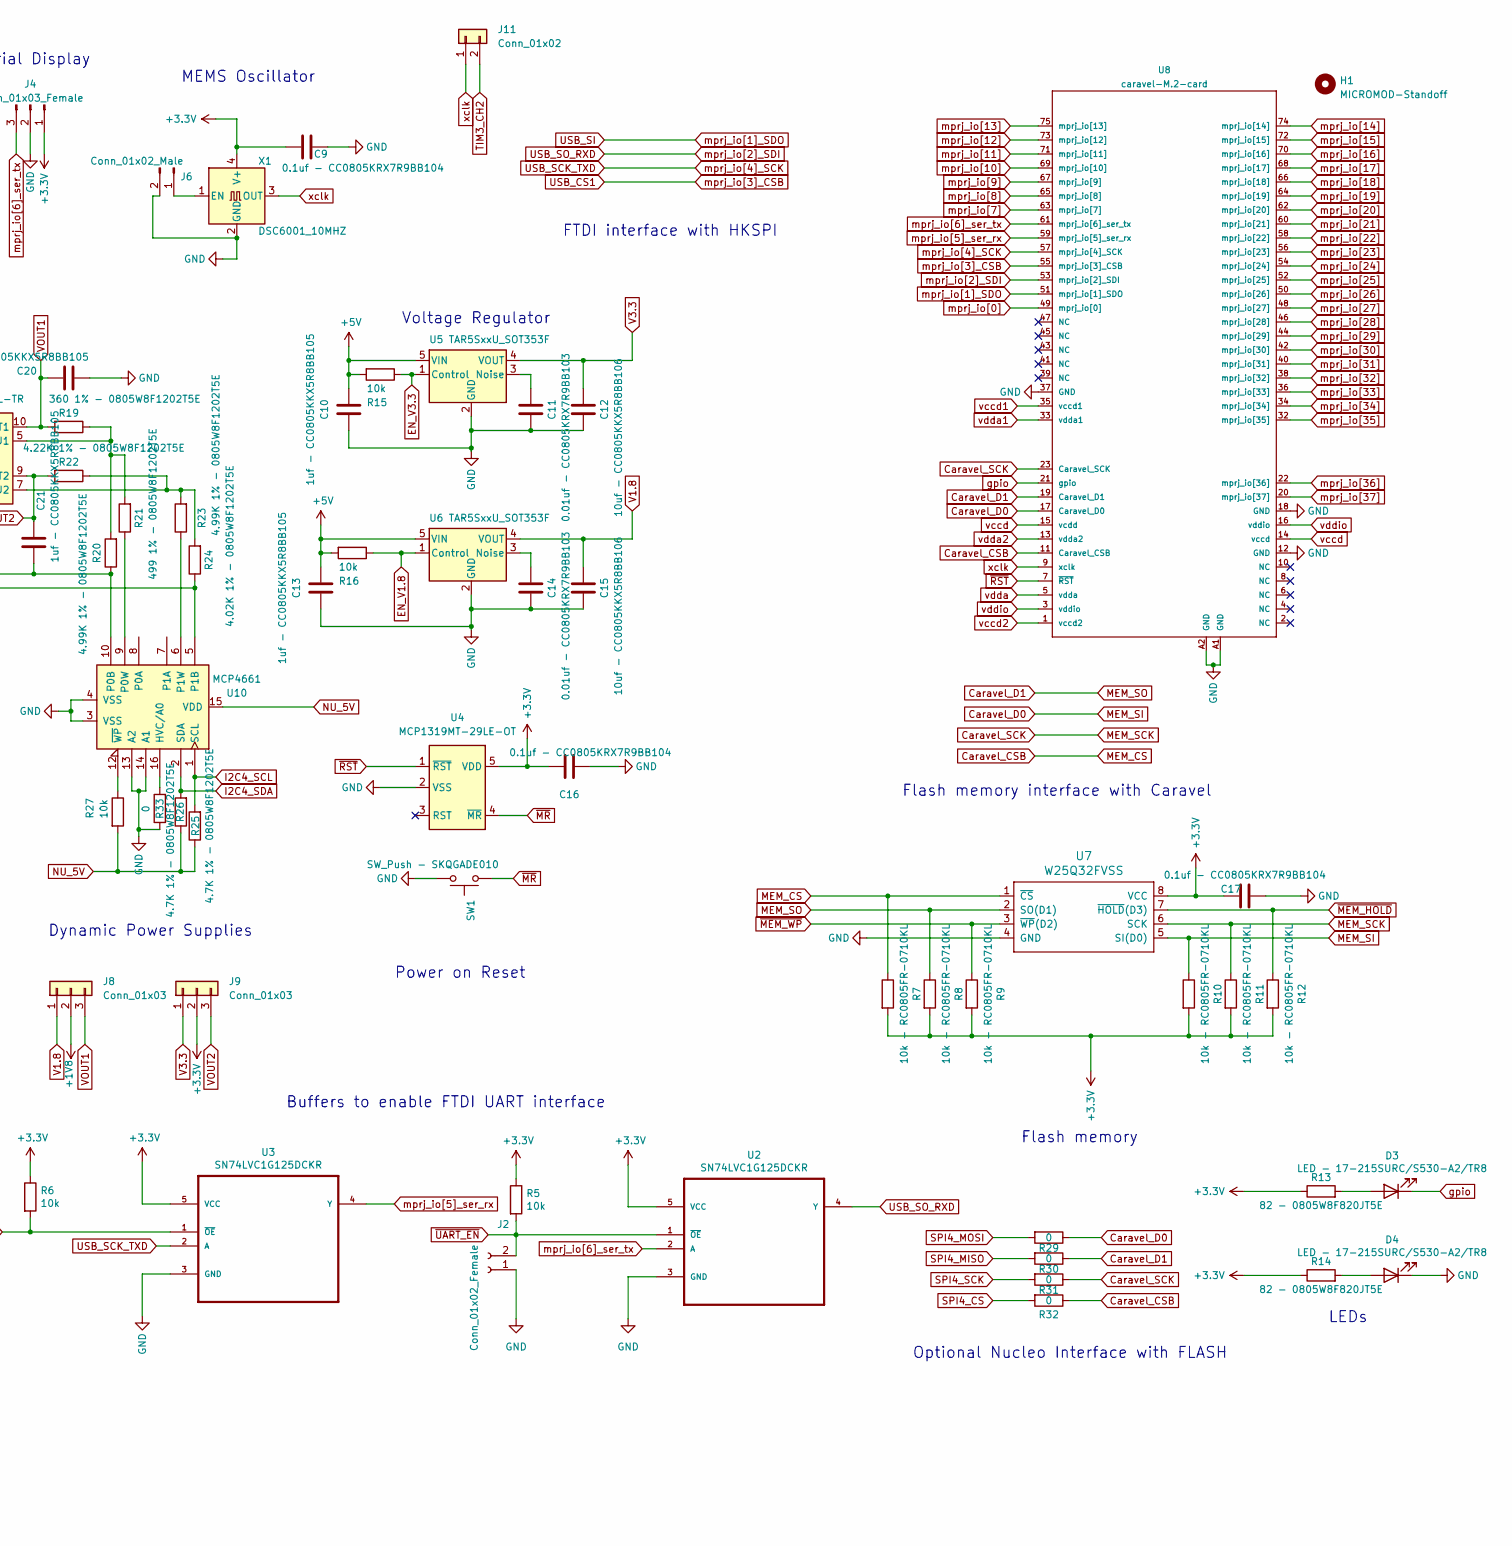
[picture p116: schematic caravel-Nucleo-v2-M.2.kicad_sch, part in row 1, column 2]

Parts:
C1: 0.01uf - CC0805JRX7R9BB103; C_0805_2012Metric
C2, C3, C4, C5, C6, C7, C8, C9, C16, C17: 0.1uf - CC0805KRX7R9BB104; C_0805_2012Metric
C10, C13, C18, C20, C21, C22: 1uf - CC0805KKX5R8BB105; C_0805_2012Metric
C11, C14, C19, C23: 0.01uf - CC0805KRX7R9BB103; C_0805_2012Metric
C12, C15, C24: 10uf - CC0805KKX5R8BB106; C_0805_2012Metric
D1, D2, D3, D4: LED - 17-215SURC/S530-A2/TR8; LED_1206_3216Metric
H1: MICROMOD-Standoff; MicroMod-Standoff
J1: USB_B_Micro - 10118193-0001LF; FCI_10118193-0001LF
J2: Conn_01x02_Female; PinHeader_1x02_P2.54mm_Vertical
J3, J5, J6, J12: Conn_01x02_Male; PinHeader_1x02_P2.54mm_Vertical
J4: Conn_01x03_Female; PinHeader_1x03_P2.54mm_Vertical
J7: Conn_01x06_Female; PinHeader_1x06_P2.54mm_Vertical
J8, J9: Conn_01x03; PinHeader_1x03_P2.54mm_Vertical
J10: Conn_01x11_Female; PinHeader_1x11_P2.54mm_Vertical
J11: Conn_01x02; PinHeader_1x02_P2.54mm_Vertical
R1, R7, R8, R9, R10, R11, R12: 10k - RC0805FR-0710KL; R_0805_2012Metric
R2: 12K 1% - 0805W8F1202T5E; R_0805_2012Metric
R3, R4: 150 - 0805W8J0151T5E; R_0805_2012Metric
R5, R6, R15, R16, R17, R18, R27, R28: 10k; R_0805_2012Metric
R13, R14: 82 - 0805W8F820JT5E; R_0805_2012Metric
R19: 360 1% - 0805W8F1202T5E; R_0805_2012Metric
R20, R23: 4.99K 1% - 0805W8F1202T5E; R_0805_2012Metric
R21: 499 1% - 0805W8F1202T5E; R_0805_2012Metric
R22: 4.22K 1% - 0805W8F1202T5E; R_0805_2012Metric
R24: 4.02K 1% - 0805W8F1202T5E; R_0805_2012Metric
R25, R26: 4.7K 1% - 0805W8F1202T5E; R_0805_2012Metric
R29, R30, R31, R32, R33: 0; R_0805_2012Metric
SW1: SW_Push - SKQGADE010; SW4-SMD-5.2X5.2X1.5MM
T1: Logo; logo
T2: Logo; ef_logo
TP1: TestPoint; TestPoint_Bridge_Pitch2.54mm_Drill1.0mm
U1: FT232H; QFN-48-1EP_8x8mm_P0.5mm_EP6.2x6.2mm
U2, U3: SN74LVC1G125DCKR; SOT65P210X110-5N
U4: MCP1319MT-29LE-OT; PoR_5_SOT23
U5, U6, U11: TAR5SxxU_SOT353F; SOT-353F
U7: W25Q32FVSS; SOIC127P790X216-8N
U8: caravel-M.2-card; M.2-CONNECTOR-E
U9: MIC2211-AAYML-TR; DFN-10-1EP_3x3mm_P0.5mm_EP1.65x2.38mm
U10: MCP4661; QFN-16-1EP_5x5mm_P0.8mm_EP2.7x2.7mm
U12: NUCLEO144-F746ZG; ST_Morpho_Connector_144_STLink
X1: DSC6001_10MHZ; DSC6001JE1A-010.0000
Y1: CSTNE12M0GH5L000R0

Connections:
+5V: C10.2, C13.2, C22.2, J1.1 (VBUS), J12.1, R15.2, R16.2, R28.2, U5.5 (VIN), U6.5 (VIN), U11.5 (VIN)
Caravel_CSB: J7.1, R7.1, R32.1, U7.1 (~CS), U8.11 (Caravel_CSB)
Caravel_D0: J7.4, R10.1, R29.1, U7.5 (SI(D0)), U8.17 (Caravel_D0)
Caravel_D1: J7.2, R8.1, R30.1, U7.2 (SO(D1)), U8.19 (Caravel_D1)
Caravel_SCK: J7.5, R11.1, R31.1, U7.6 (SCK), U8.23 (Caravel_SCK)
EN_V1.8: R16.1, U1.29 (ACBUS5), U6.1 (Control)
EN_V3.3: R15.1, U1.30 (ACBUS6), U5.1 (Control)
EN_VOUT1: R18.1, U9.2 (EN1), U12.52 (PF2)
EN_VOUT2: R17.1, U9.3 (EN2), U12.47 (PE3)
FTDI_D+: J1.3 (D+), U1.7 (DP)
FTDI_D-: J1.2 (D-), U1.6 (DM)
FTDI_V3.3: C4.2, C5.2, C6.2, C7.2, C8.2, C24.2, R1.2, R3.2, R4.2, U1.3 (VPHY), U1.8 (VPLL), U1.12 (VCCIO), U1.24 (VCCIO), U1.39 (VCCD), U1.40 (VREGIN), U1.46 (VCCIO), U11.4 (VOUT)
GND: C1.1, C2.1, C3.1, C4.1, C5.1, C6.1, C7.1, C8.1, C9.1, C10.1, C11.2, C12.1, C13.1, C14.2, C15.1, C16.1, C17.2, C18.1, C19.2, C20.2, C21.2, C22.1, C23.2, C24.1, D4.1 (K), J1.5 (GND), J2.1, J4.2, J6.2, R2.1, R20.1, R24.1, R33.1, SW1.2, TP1.1, U1.4 (AGND), U1.9 (AGND), U1.10 (GND), U1.11 (GND), U1.22 (GND), U1.23 (GND), U1.35 (GND), U1.36 (GND), U1.41 (AGND), U1.42 (TEST), U1.47 (GND), U1.48 (GND), U2.3 (GND), U3.3 (GND), U4.2 (VSS), U5.2 (GND), U6.2 (GND), U7.4 (GND), U8.12 (GND), U8.18 (GND), U8.37 (GND), U8.A1 (GND), U8.A2 (GND), U9.6 (GND), U10.3 (VSS), U10.4 (VSS), U10.5 (P1B), U10.10 (P0B), U10.13 (A2), U10.14 (A1), U11.2 (GND), U12.8 (GND), U12.19 (GND), U12.20 (GND), U12.22 (GND), U12.49 (GND), U12.60 (GND), U12.71 (GND), U12.72 (GND), U12.81 (GND), U12.92 (GND), U12.104 (AGND), U12.111 (GND), U12.126 (GND), U12.135 (GND), U12.143 (GND), U12.144 (GND), X1.2 (GND), Y1.2
I2C4_SCL: R25.2, U10.1 (SCL), U12.115 (PD12)
I2C4_SDA: R26.2, U10.2 (SDA), U12.113 (PD13)
NU_5V: C18.2, J12.2, R17.2, R18.2, R25.1, R26.1, R27.2, U9.1 (VIN), U10.15 (VDD), U12.18 (+5V)
unnamed: D1.2 (A), R3.1
unnamed: D1.1 (K), U1.27 (ACBUS3)
unnamed: D2.2 (A), R4.1
unnamed: D2.1 (K), U1.26 (ACBUS2)
unnamed: D3.2 (A), R13.2
unnamed: D4.2 (A), R14.2
unnamed: J6.1, X1.1 (EN)
unnamed: R2.2, U1.5 (REF)
unnamed: C3.2, U1.37 (VCCA)
unnamed: C2.2, U1.38 (VCCCORE)
unnamed: U1.1 (XCSI), Y1.1
unnamed: U1.2 (XCSO), Y1.3
unnamed: C1.2, R1.1, U1.34 (~RESET)
unnamed: C11.1, U5.3 (Noise)
unnamed: C14.1, U6.3 (Noise)
unnamed: R19.1, R20.2, R21.2, U9.5 (ADJ1)
unnamed: R22.1, R23.2, R24.2, U9.7 (ADJ2)
unnamed: C19.1, U9.4 (BYP)
unnamed: R33.2, U10.16 (HVC/A0)
unnamed: R21.1, U10.9 (P0W)
unnamed: R23.1, U10.6 (P1W)
unnamed: R27.1, U10.12 (~WP)
unnamed: R28.1, U11.1 (Control)
unnamed: C23.1, U11.3 (Noise)
SPI4_CS: R32.2, U12.128 (PE11)
SPI4_MISO: R30.2, U12.127 (PE13)
SPI4_MOSI: R29.2, U12.123 (PE14)
SPI4_SCK: R31.2, U12.121 (PE12)
SPI5_CS: U1.16 (ADBUS3), U8.55 (mprj_io[3]_CSB), U12.9 (PF6)
SPI5_MISO: U1.15 (ADBUS2), U8.51 (mprj_io[1]_SDO), U12.54 (PF8)
SPI5_MOSI: U1.14 (ADBUS1), U2.4 (Y), U8.53 (mprj_io[2]_SDI), U12.56 (PF9)
SPI5_SCK: U1.13 (ADBUS0), U3.2 (A), U8.57 (mprj_io[4]_SCK), U12.11 (PF7)
TIM3_CH2: J11.2, U12.101 (PB5)
UART8_RX: J4.3, U2.2 (A), U8.61 (mprj_io[6]_ser_tx), U12.136 (PE0)
UART8_TX: U3.4 (Y), U8.59 (mprj_io[5]_ser_rx), U12.61 (PE1)
V1.8: C15.2, J8.1, U6.4 (VOUT)
V3.3: C12.2, J9.1, U5.4 (VOUT)
VOUT1: C20.1, J8.3, R19.2, U9.10 (VOUT1)
VOUT2: C21.1, J9.3, R22.2, U9.9 (VOUT2)
gpio: D3.1 (K), J10.10, U8.21 (gpio), U12.137 (PD10)
mprj_io[0]: U8.49 (mprj_io[0]), U12.65 (PG12)
mprj_io[7]: U8.63 (mprj_io[7]), U12.66 (PG10)
mprj_io[8]: U8.65 (mprj_io[8]), U12.64 (PG15)
mprj_io[9]: U8.67 (mprj_io[9]), U12.63 (PG9)
mprj_io[10]: U8.69 (mprj_io[10]), U12.59 (PG0)
mprj_io[11]: U8.71 (mprj_io[11]), U12.58 (PG1)
mprj_io[12]: U8.73 (mprj_io[12]), U12.45 (PD7)
mprj_io[13]: U8.75 (mprj_io[13]), U12.44 (PG3)
mprj_io[14]: U8.74 (mprj_io[14]), U12.43 (PD6)
mprj_io[15]: U8.72 (mprj_io[15]), U12.42 (PG2)
mprj_io[16]: U8.70 (mprj_io[16]), U12.41 (PD5)
mprj_io[17]: U8.68 (mprj_io[17]), U12.40 (PD3)
mprj_io[18]: U8.66 (mprj_io[18]), U12.39 (PD4)
mprj_io[19]: U8.64 (mprj_io[19]), U12.38 (PC0)
mprj_io[20]: U8.62 (mprj_io[20]), U12.37 (PC3)
mprj_io[21]: U8.60 (mprj_io[21]), U12.35 (PC2)
mprj_io[22]: U8.58 (mprj_io[22]), U12.32 (PA4)
mprj_io[23]: U8.56 (mprj_io[23]), U12.28 (ETH_REF_CLK/PA0)
mprj_io[24]: U8.54 (mprj_io[24]), U12.17 (PA15)
mprj_io[25]: U8.52 (mprj_io[25]), U12.1 (PC10)
mprj_io[26]: U8.50 (mprj_io[26]), U12.2 (PC11)
mprj_io[27]: U8.48 (mprj_io[27]), U12.4 (PD2)
mprj_io[28]: U8.46 (mprj_io[28]), U12.73 (PC9)
mprj_io[29]: U8.44 (mprj_io[29]), U12.74 (PC8)
mprj_io[30]: U8.42 (mprj_io[30]), U12.75 (PB8)
mprj_io[31]: U8.40 (mprj_io[31]), U12.76 (PC6)
mprj_io[32]: U8.38 (mprj_io[32]), U12.77 (PB9)
mprj_io[33]: U8.36 (mprj_io[33]), U12.88 (PB12)
mprj_io[34]: U8.34 (mprj_io[34]), U12.89 (PB6)
mprj_io[35]: U8.32 (mprj_io[35]), U12.94 (PB2)
mprj_io[36]: U8.22 (mprj_io[36]), U12.96 (PB1)
mprj_io[37]: U8.20 (mprj_io[37]), U12.98 (PB15)
vccd: J3.1, J3.2, J8.2, J10.3, J10.4, J10.5, U8.14 (vccd), U8.15 (vcdd), U8.35 (vccd1)
vccd2: J10.2, U8.1 (vccd2)
vdda: C9.2, C16.2, C17.1, J4.1, J5.1, J5.2, J9.2, J10.7, J10.8, R5.1, R6.1, R7.2, R8.2, R9.2, R10.2, R11.2, R12.2, R13.1, R14.1, U2.5 (VCC), U3.5 (VCC), U4.5 (VDD), U7.8 (VCC), U8.3 (vddio), U8.5 (vdda), U8.16 (vddio), X1.4 (V+)
vdda1: J10.6, U8.33 (vdda1)
vdda2: J10.9, U8.13 (vdda2)
xclk: J10.11, J11.1, U8.9 (xclk), X1.3 (OUT)
~MEM_HOLD: J7.6, R12.1, U7.7 (~HOLD(D3))
~MEM_WP: J7.3, R9.1, U7.3 (~WP(D2))
~MR: SW1.1, U1.25 (ACBUS1), U4.4 (~MR), U12.3 (PC12)
~RST: J10.1, U4.1 (~RST), U8.7 (~RST)
~UART_EN: J2.2, R5.2, R6.2, U1.21 (ACBUS0), U2.1 (~OE), U3.1 (~OE)

Notes on the sheet:
Caravel Interface with Nucleo
Flash memory
MEMS Oscillator
Serial Display
Power on Reset
LEDs
Memory testing
Voltage Regulator
Optional Nucleo Interface with FLASH
FTDI interface with HKSPI
USB Module
FTDI Module
FTDI Voltage Regulator
Buffers to enable FTDI UART interface
Nucleo ST Morpho Connectors
Flash memory interface with Caravel
Dynamic Power Supplies

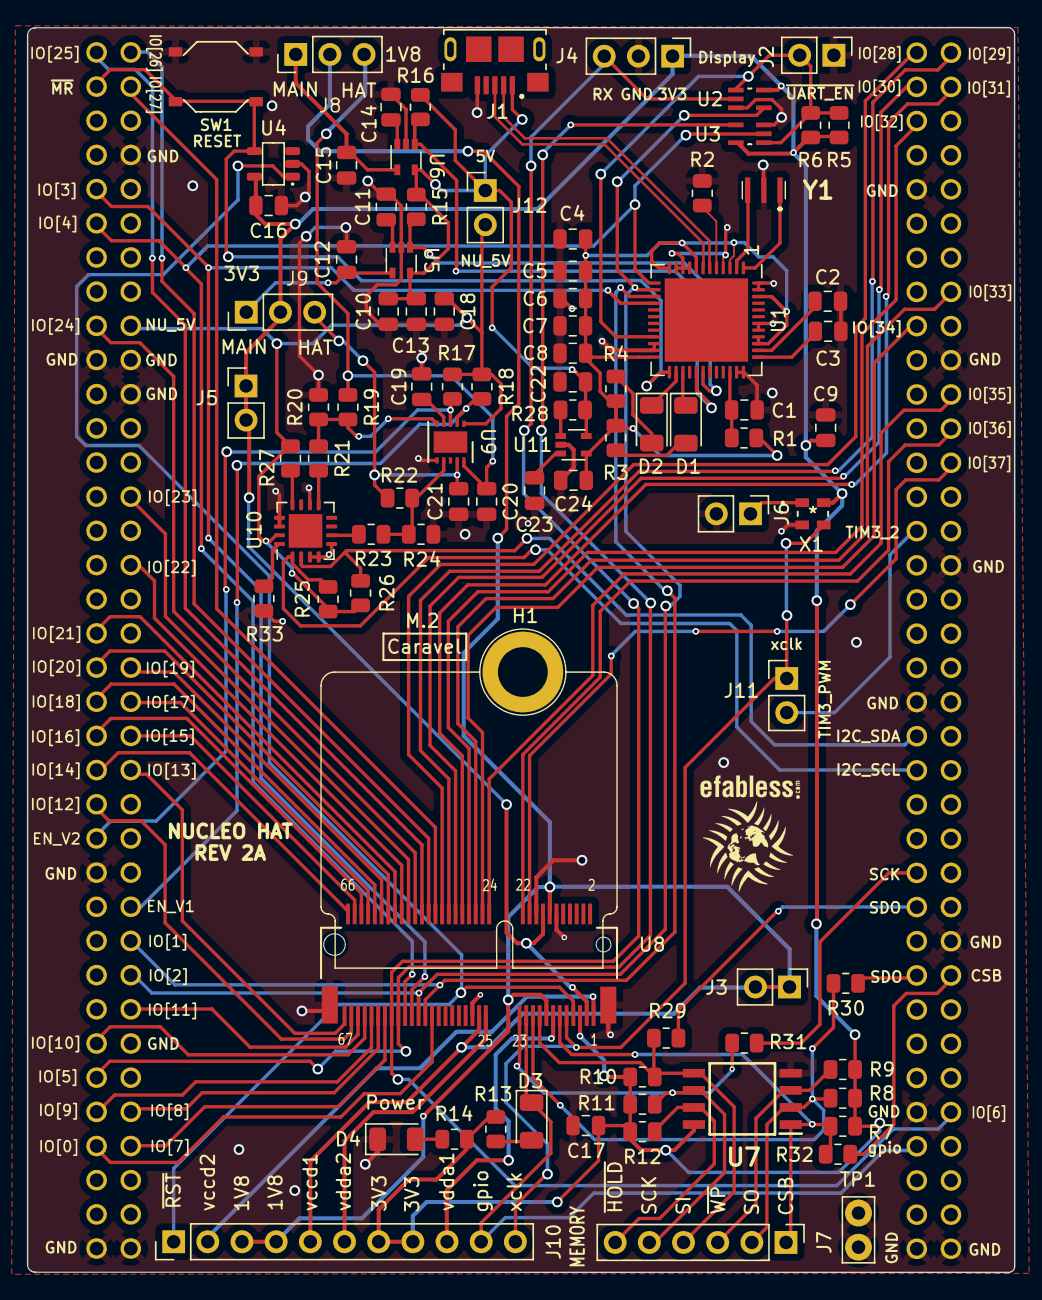
[picture p117: board caravel-Nucleo-v2-M.2.kicad_pcb from above]

Board: 2 copper layers, 73.4 x 92.5 mm, 92 parts (0 on the bottom side), 99 nets.
