efabless/caravel_board/hardware/breakout/caravel-M.2-card-WCSP/caravel-M.2-card-WCSP.kicad_pcb

## KiCad design hardware/breakout/caravel-M.2-card-WCSP/caravel-M.2-card-WCSP.kicad_pcb (2023-04-04)

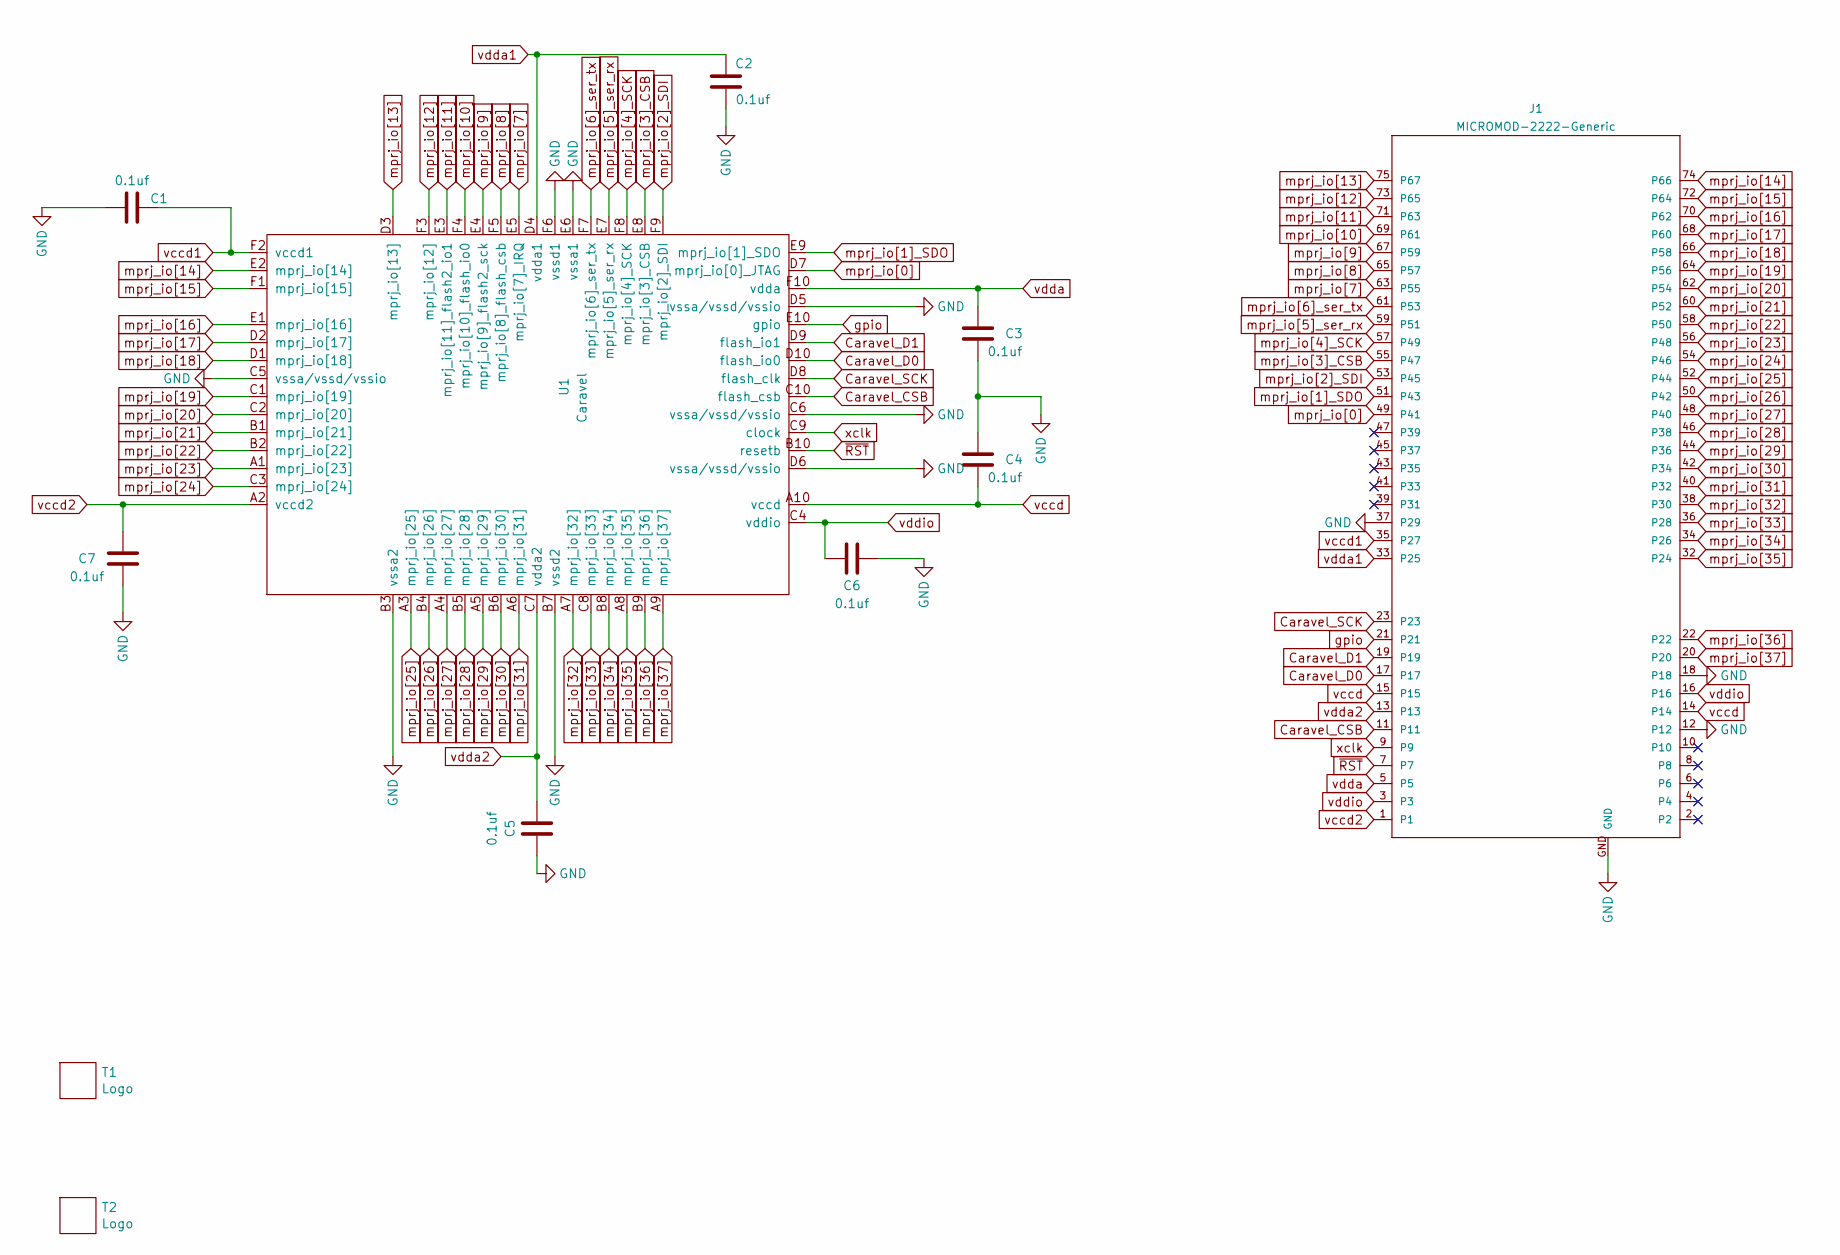
[picture p118: schematic caravel-M.2-card-WCSP.kicad_sch, Carvel Breakout board as M.2 Card]

Parts:
C1, C2, C3, C4, C5, C6, C7: 0.1uf; C_0402_1005Metric
J1: MICROMOD-2222-Generic; MicroMod-M.2-CARD-E-22
T1: Logo; logo_small
T2: Logo; ef_logo
U1: Caravel; Caravel_WCSP

Connections:
Caravel_CSB: J1.11, U1.C10 (flash_csb)
Caravel_D0: J1.17, U1.D10 (flash_io0)
Caravel_D1: J1.19, U1.D9 (flash_io1)
Caravel_SCK: J1.23, U1.D8 (flash_clk)
GND: C1.1, C2.2, C3.2, C4.1, C5.1, C6.1, C7.1, J1.12, J1.18, J1.37 (P29), J1.GND, U1.B3 (vssa2), U1.B7 (vssd2), U1.C5 (vssa/vssd/vssio), U1.C6 (vssa/vssd/vssio), U1.D5 (vssa/vssd/vssio), U1.D6 (vssa/vssd/vssio), U1.E6 (vssa1), U1.F6 (vssd1)
gpio: J1.21, U1.E10 (gpio)
mprj_io[0]: J1.49 (P41), U1.D7 (mprj_io[0]_JTAG)
mprj_io[1]_SDO: J1.51 (P43), U1.E9 (mprj_io[1]_SDO)
mprj_io[2]_SDI: J1.53 (P45), U1.F9 (mprj_io[2]_SDI)
mprj_io[3]_CSB: J1.55 (P47), U1.E8 (mprj_io[3]_CSB)
mprj_io[4]_SCK: J1.57 (P49), U1.F8 (mprj_io[4]_SCK)
mprj_io[5]_ser_rx: J1.59 (P51), U1.E7 (mprj_io[5]_ser_rx)
mprj_io[6]_ser_tx: J1.61 (P53), U1.F7 (mprj_io[6]_ser_tx)
mprj_io[7]: J1.63 (P55), U1.E5 (mprj_io[7]_IRQ)
mprj_io[8]: J1.65 (P57), U1.F5 (mprj_io[8]_flash_csb)
mprj_io[9]: J1.67 (P59), U1.E4 (mprj_io[9]_flash2_sck)
mprj_io[10]: J1.69 (P61), U1.F4 (mprj_io[10]_flash_io0)
mprj_io[11]: J1.71 (P63), U1.E3 (mprj_io[11]_flash2_io1)
mprj_io[12]: J1.73 (P65), U1.F3 (mprj_io[12])
mprj_io[13]: J1.75 (P67), U1.D3 (mprj_io[13])
mprj_io[14]: J1.74 (P66), U1.E2 (mprj_io[14])
mprj_io[15]: J1.72 (P64), U1.F1 (mprj_io[15])
mprj_io[16]: J1.70 (P62), U1.E1 (mprj_io[16])
mprj_io[17]: J1.68 (P60), U1.D2 (mprj_io[17])
mprj_io[18]: J1.66 (P58), U1.D1 (mprj_io[18])
mprj_io[19]: J1.64 (P56), U1.C1 (mprj_io[19])
mprj_io[20]: J1.62 (P54), U1.C2 (mprj_io[20])
mprj_io[21]: J1.60 (P52), U1.B1 (mprj_io[21])
mprj_io[22]: J1.58 (P50), U1.B2 (mprj_io[22])
mprj_io[23]: J1.56 (P48), U1.A1 (mprj_io[23])
mprj_io[24]: J1.54 (P46), U1.C3 (mprj_io[24])
mprj_io[25]: J1.52 (P44), U1.A3 (mprj_io[25])
mprj_io[26]: J1.50 (P42), U1.B4 (mprj_io[26])
mprj_io[27]: J1.48 (P40), U1.A4 (mprj_io[27])
mprj_io[28]: J1.46 (P38), U1.B5 (mprj_io[28])
mprj_io[29]: J1.44 (P36), U1.A5 (mprj_io[29])
mprj_io[30]: J1.42 (P34), U1.B6 (mprj_io[30])
mprj_io[31]: J1.40 (P32), U1.A6 (mprj_io[31])
mprj_io[32]: J1.38 (P30), U1.A7 (mprj_io[32])
mprj_io[33]: J1.36 (P28), U1.C8 (mprj_io[33])
mprj_io[34]: J1.34 (P26), U1.B8 (mprj_io[34])
mprj_io[35]: J1.32 (P24), U1.A8 (mprj_io[35])
mprj_io[36]: J1.22, U1.B9 (mprj_io[36])
mprj_io[37]: J1.20, U1.A9 (mprj_io[37])
vccd: C4.2, J1.14, J1.15, U1.A10 (vccd)
vccd1: C1.2, J1.35 (P27), U1.F2 (vccd1)
vccd2: C7.2, J1.1, U1.A2 (vccd2)
vdda: C3.1, J1.5, U1.F10 (vdda)
vdda1: C2.1, J1.33 (P25), U1.D4 (vdda1)
vdda2: C5.2, J1.13, U1.C7 (vdda2)
vddio: C6.2, J1.3, J1.16, U1.C4 (vddio)
xclk: J1.9, U1.C9 (clock)
~RST: J1.7, U1.B10 (resetb)

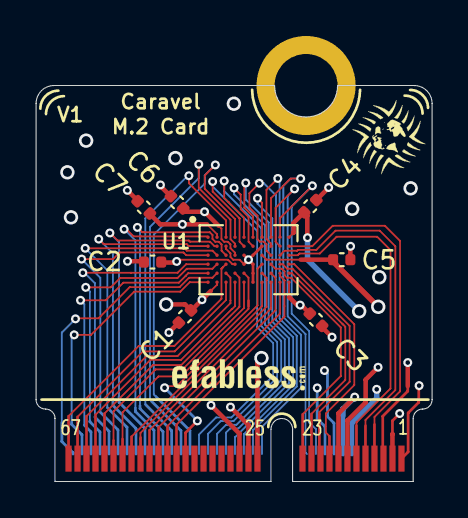
[picture p119: board caravel-M.2-card-WCSP.kicad_pcb from above]

Board: 4 copper layers, 22.0 x 22.0 mm, 11 parts (0 on the bottom side), 53 nets.
