efabless/caravel_board/hardware/other/led-bar-pcb/led-bar-pcb.kicad_pcb

## KiCad design hardware/other/led-bar-pcb/led-bar-pcb.kicad_pcb (2023-04-05)

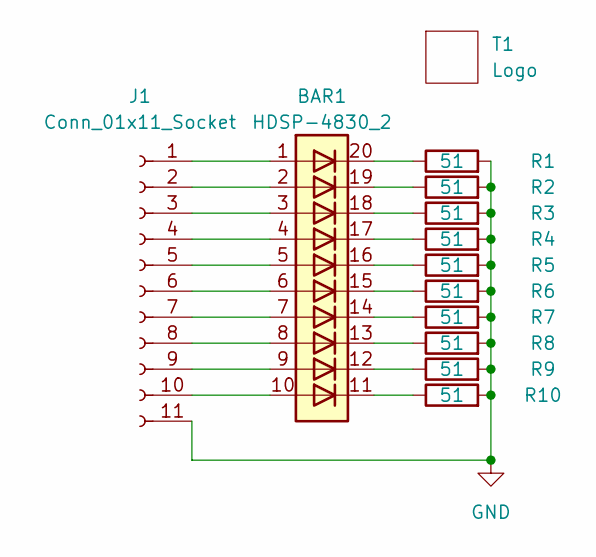
[picture p120: schematic led-bar-pcb.kicad_sch]

Parts:
BAR1: HDSP-4830_2; HDSP-4830
J1: Conn_01x11_Socket; PinHeader_1x11_P1.00mm_Vertical
R1, R2, R3, R4, R5, R6, R7, R8, R9, R10: 51; R_0805_2012Metric
T1: Logo; ef_logo

Connections:
GND: J1.11, R1.2, R2.2, R3.2, R4.2, R5.2, R6.2, R7.2, R8.2, R9.2, R10.2
unnamed: BAR1.11 (K), R10.1
unnamed: BAR1.12 (K), R9.1
unnamed: BAR1.13 (K), R8.1
unnamed: BAR1.14 (K), R7.1
unnamed: BAR1.15 (K), R6.1
unnamed: BAR1.16 (K), R5.1
unnamed: BAR1.17 (K), R4.1
unnamed: BAR1.18 (K), R3.1
unnamed: BAR1.19 (K), R2.1
unnamed: BAR1.20 (K), R1.1
unnamed: BAR1.1 (A), J1.1
unnamed: BAR1.2 (A), J1.2
unnamed: BAR1.3 (A), J1.3
unnamed: BAR1.4 (A), J1.4
unnamed: BAR1.5 (A), J1.5
unnamed: BAR1.6 (A), J1.6
unnamed: BAR1.7 (A), J1.7
unnamed: BAR1.8 (A), J1.8
unnamed: BAR1.9 (A), J1.9
unnamed: BAR1.10 (A), J1.10

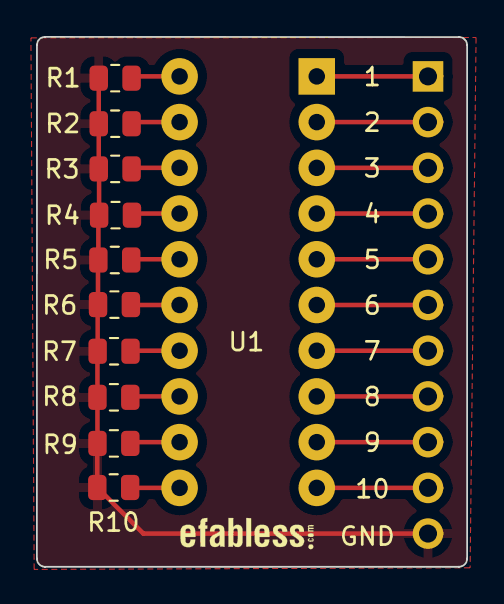
[picture p121: board led-bar-pcb.kicad_pcb from above]

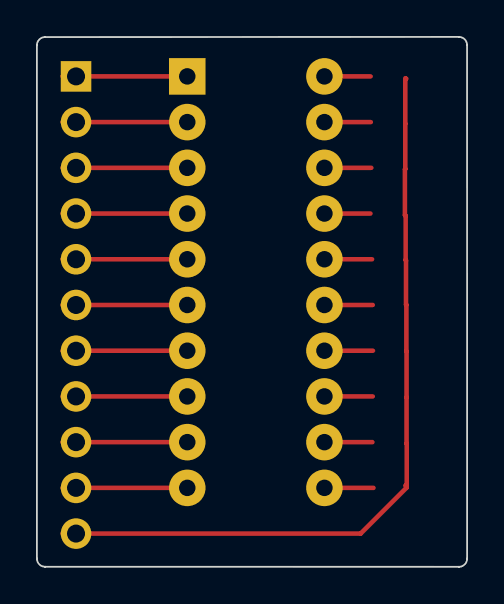
[picture p122: board led-bar-pcb.kicad_pcb from below]

Board: 2 copper layers, 23.9 x 29.4 mm, 13 parts (2 on the bottom side), 21 nets.
