efabless/caravel_board/hardware/5V-dev-v6-M.2/5V-dev-v6-M.2.kicad_sch

## KiCad design hardware/5V-dev-v6-M.2/5V-dev-v6-M.2.kicad_sch (2023-05-03)

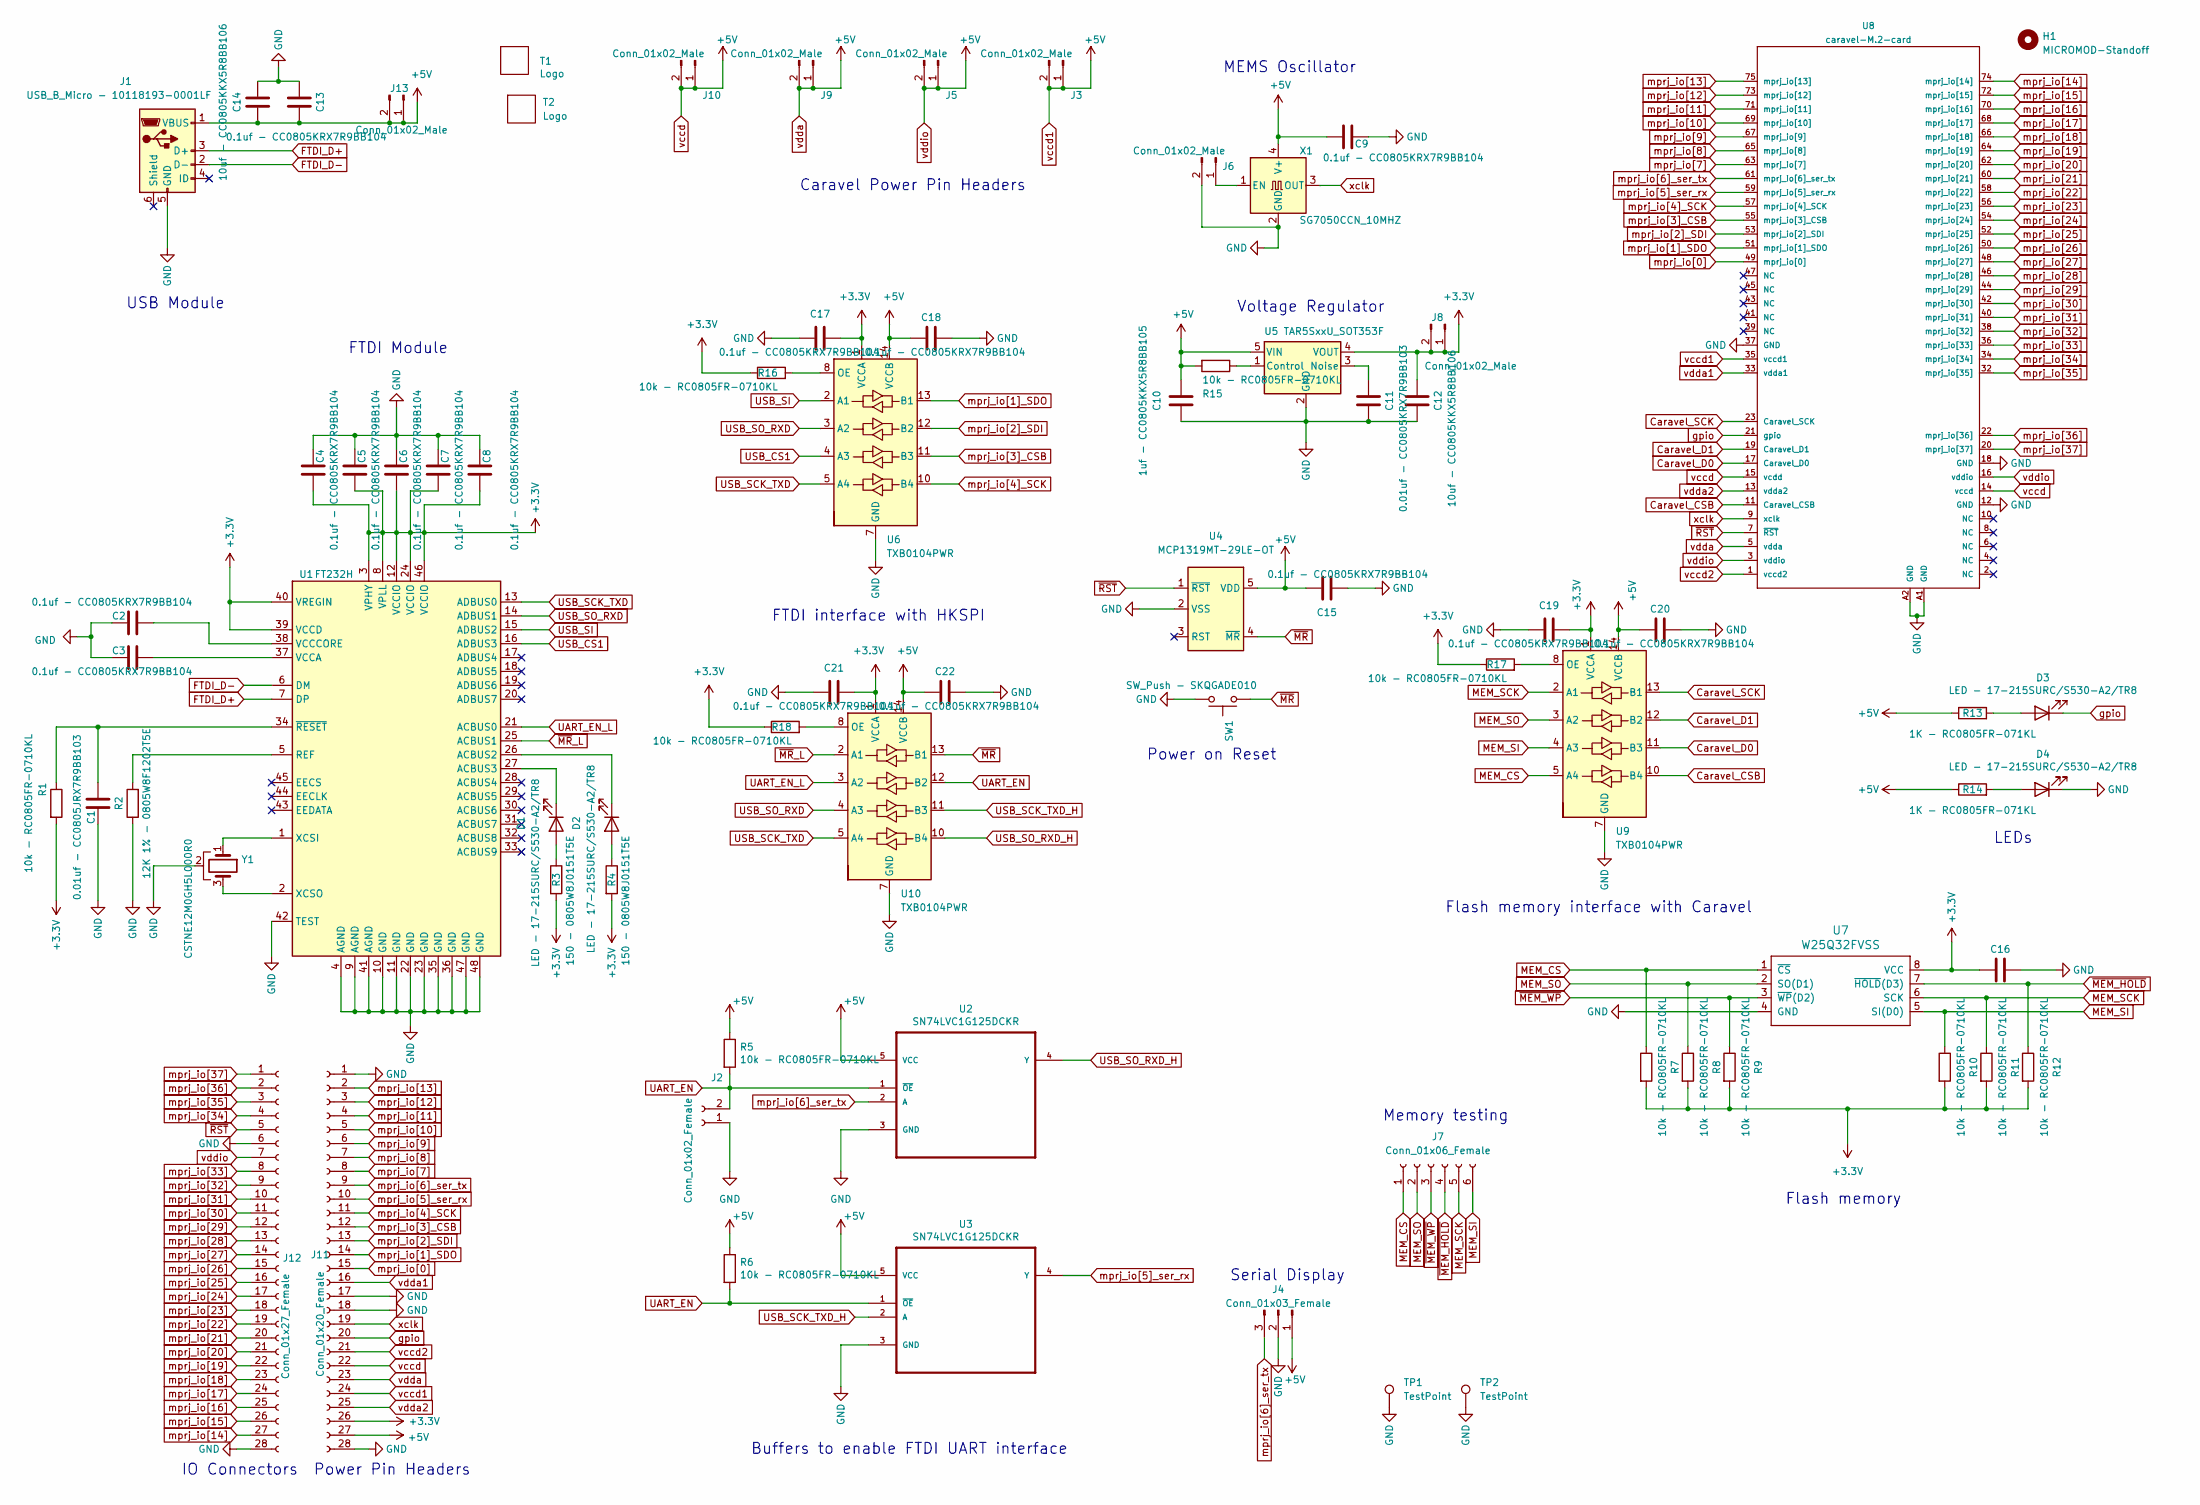
[picture p125: schematic 5V-dev-v6-M.2.kicad_sch]

Parts:
C1: 0.01uf - CC0805JRX7R9BB103; C_0805_2012Metric
C2, C3, C4, C5, C6, C7, C8, C9, C13, C15, C16, C17, C18, C19, C20, C21, C22: 0.1uf - CC0805KRX7R9BB104; C_0805_2012Metric
C10: 1uf - CC0805KKX5R8BB105; C_0805_2012Metric
C11: 0.01uf - CC0805KRX7R9BB103; C_0805_2012Metric
C12, C14: 10uf - CC0805KKX5R8BB106; C_0805_2012Metric
D1, D2, D3, D4: LED - 17-215SURC/S530-A2/TR8; LED_1206_3216Metric
H1: MICROMOD-Standoff; MicroMod-Standoff
J1: USB_B_Micro - 10118193-0001LF; FCI_10118193-0001LF
J2: Conn_01x02_Female; PinHeader_1x02_P2.54mm_Vertical
J3, J5, J6, J8, J9, J10, J13: Conn_01x02_Male; PinHeader_1x02_P2.54mm_Vertical
J4: Conn_01x03_Female; PinHeader_1x03_P2.54mm_Vertical
J7: Conn_01x06_Female; PinHeader_1x06_P2.54mm_Vertical
J11: Conn_01x20_Female; PinHeader_1x20_P2.54mm_Vertical
J12: Conn_01x27_Female; PinHeader_1x27_P2.54mm_Vertical
R1, R5, R6, R7, R8, R9, R10, R11, R12, R15, R16, R17, R18: 10k - RC0805FR-0710KL; R_0805_2012Metric
R2: 12K 1% - 0805W8F1202T5E; R_0805_2012Metric
R3, R4: 150 - 0805W8J0151T5E; R_0805_2012Metric
R13, R14: 1K - RC0805FR-071KL; R_0805_2012Metric
SW1: SW_Push - SKQGADE010; SW4-SMD-5.2X5.2X1.5MM
T1: Logo; logo
T2: Logo; ef_logo
TP1, TP2: TestPoint; TestPoint_Bridge_Pitch2.54mm_Drill1.0mm
U1: FT232H; QFN-48-1EP_8x8mm_P0.5mm_EP6.2x6.2mm
U2, U3: SN74LVC1G125DCKR; SOT65P210X110-5N
U4: MCP1319MT-29LE-OT; PoR_5_SOT23
U5: TAR5SxxU_SOT353F; SOT-353F
U6, U9, U10: TXB0104PWR; TSSOP-14_4.4x5mm_P0.65mm
U7: W25Q32FVSS; SOIC127P790X216-8N
U8: caravel-M.2-card; M.2-CONNECTOR-E
X1: SG7050CCN_10MHZ; SG7050CCN-10M-HJGA3
Y1: CSTNE12M0GH5L000R0

Connections:
+3.3V: C4.2, C5.2, C6.2, C7.2, C8.2, C12.2, C16.1, C17.2, C19.2, C21.2, J8.1, J8.2, J11.26, R1.2, R3.2, R4.2, R7.2, R8.2, R9.2, R10.2, R11.2, R12.2, R16.1, R17.1, R18.1, U1.3 (VPHY), U1.8 (VPLL), U1.12 (VCCIO), U1.24 (VCCIO), U1.39 (VCCD), U1.40 (VREGIN), U1.46 (VCCIO), U5.4 (VOUT), U6.1 (VCCA), U7.8 (VCC), U9.1 (VCCA), U10.1 (VCCA)
+5V: C9.2, C10.2, C13.1, C14.2, C15.2, C18.2, C20.2, C22.2, J1.1 (VBUS), J3.1, J3.2, J4.1, J5.1, J5.2, J9.1, J9.2, J10.1, J10.2, J11.22, J11.23, J11.24, J11.27, J12.7, J13.1, J13.2, R5.1, R6.1, R13.1, R14.1, R15.2, U2.5 (VCC), U3.5 (VCC), U4.5 (VDD), U5.5 (VIN), U6.14 (VCCB), U8.3 (vddio), U8.5 (vdda), U8.14 (vccd), U8.15 (vcdd), U8.16 (vddio), U8.35 (vccd1), U9.14 (VCCB), U10.14 (VCCB), X1.4 (V+)
Caravel_CSB: U8.11 (Caravel_CSB), U9.10 (B4)
Caravel_D0: U8.17 (Caravel_D0), U9.11 (B3)
Caravel_D1: U8.19 (Caravel_D1), U9.12 (B2)
Caravel_SCK: U8.23 (Caravel_SCK), U9.13 (B1)
FTDI_D+: J1.3 (D+), U1.7 (DP)
FTDI_D-: J1.2 (D-), U1.6 (DM)
GND: C1.1, C2.1, C3.1, C4.1, C5.1, C6.1, C7.1, C8.1, C9.1, C10.1, C11.2, C12.1, C13.2, C14.1, C15.1, C16.2, C17.1, C18.1, C19.1, C20.1, C21.1, C22.1, D4.1 (K), J1.5 (GND), J2.1, J4.2, J6.2, J11.1, J11.17, J11.18, J11.28, J12.6, J12.28, R2.1, SW1.2, TP1.1, TP2.1, U1.4 (AGND), U1.9 (AGND), U1.10 (GND), U1.11 (GND), U1.22 (GND), U1.23 (GND), U1.35 (GND), U1.36 (GND), U1.41 (AGND), U1.42 (TEST), U1.47 (GND), U1.48 (GND), U2.3 (GND), U3.3 (GND), U4.2 (VSS), U5.2 (GND), U6.7 (GND), U7.4 (GND), U8.12 (GND), U8.18 (GND), U8.37 (GND), U8.A1 (GND), U8.A2 (GND), U9.7 (GND), U10.7 (GND), X1.2 (GND), Y1.2
MEM_CS: J7.1, R7.1, U7.1 (~CS), U9.5 (A4)
MEM_SCK: J7.5, R11.1, U7.6 (SCK), U9.2 (A1)
MEM_SI: J7.6, R10.1, U7.5 (SI(D0)), U9.4 (A3)
MEM_SO: J7.2, R8.1, U7.2 (SO(D1)), U9.3 (A2)
unnamed: C1.2, R1.1, U1.34 (~RESET)
unnamed: C2.2, U1.38 (VCCCORE)
unnamed: C3.2, U1.37 (VCCA)
unnamed: C11.1, U5.3 (Noise)
unnamed: D1.1 (K), U1.27 (ACBUS3)
unnamed: D1.2 (A), R3.1
unnamed: D2.1 (K), U1.26 (ACBUS2)
unnamed: D2.2 (A), R4.1
unnamed: D3.2 (A), R13.2
unnamed: D4.2 (A), R14.2
unnamed: J6.1, X1.1 (EN)
unnamed: R2.2, U1.5 (REF)
unnamed: R15.1, U5.1 (Control)
unnamed: R16.2, U6.8 (OE)
unnamed: R17.2, U9.8 (OE)
unnamed: R18.2, U10.8 (OE)
unnamed: U1.1 (XCSI), Y1.1
unnamed: U1.2 (XCSO), Y1.3
UART_EN: J2.2, R5.2, R6.2, U2.1 (~OE), U3.1 (~OE), U10.12 (B2)
UART_EN_L: U1.21 (ACBUS0), U10.3 (A2)
USB_CS1: U1.16 (ADBUS3), U6.4 (A3)
USB_SCK_TXD: U1.13 (ADBUS0), U6.5 (A4), U10.5 (A4)
USB_SCK_TXD_H: U3.2 (A), U10.11 (B3)
USB_SI: U1.15 (ADBUS2), U6.2 (A1)
USB_SO_RXD: U1.14 (ADBUS1), U6.3 (A2), U10.4 (A3)
USB_SO_RXD_H: U2.4 (Y), U10.10 (B4)
gpio: D3.1 (K), J11.20, U8.21 (gpio)
mprj_io[0]: J11.15, U8.49 (mprj_io[0])
mprj_io[1]_SDO: J11.14, U6.13 (B1), U8.51 (mprj_io[1]_SDO)
mprj_io[2]_SDI: J11.13, U6.12 (B2), U8.53 (mprj_io[2]_SDI)
mprj_io[3]_CSB: J11.12, U6.11 (B3), U8.55 (mprj_io[3]_CSB)
mprj_io[4]_SCK: J11.11, U6.10 (B4), U8.57 (mprj_io[4]_SCK)
mprj_io[5]_ser_rx: J11.10, U3.4 (Y), U8.59 (mprj_io[5]_ser_rx)
mprj_io[6]_ser_tx: J4.3, J11.9, U2.2 (A), U8.61 (mprj_io[6]_ser_tx)
mprj_io[7]: J11.8, U8.63 (mprj_io[7])
mprj_io[8]: J11.7, U8.65 (mprj_io[8])
mprj_io[9]: J11.6, U8.67 (mprj_io[9])
mprj_io[10]: J11.5, U8.69 (mprj_io[10])
mprj_io[11]: J11.4, U8.71 (mprj_io[11])
mprj_io[12]: J11.3, U8.73 (mprj_io[12])
mprj_io[13]: J11.2, U8.75 (mprj_io[13])
mprj_io[14]: J12.27, U8.74 (mprj_io[14])
mprj_io[15]: J12.26, U8.72 (mprj_io[15])
mprj_io[16]: J12.25, U8.70 (mprj_io[16])
mprj_io[17]: J12.24, U8.68 (mprj_io[17])
mprj_io[18]: J12.23, U8.66 (mprj_io[18])
mprj_io[19]: J12.22, U8.64 (mprj_io[19])
mprj_io[20]: J12.21, U8.62 (mprj_io[20])
mprj_io[21]: J12.20, U8.60 (mprj_io[21])
mprj_io[22]: J12.19, U8.58 (mprj_io[22])
mprj_io[23]: J12.18, U8.56 (mprj_io[23])
mprj_io[24]: J12.17, U8.54 (mprj_io[24])
mprj_io[25]: J12.16, U8.52 (mprj_io[25])
mprj_io[26]: J12.15, U8.50 (mprj_io[26])
mprj_io[27]: J12.14, U8.48 (mprj_io[27])
mprj_io[28]: J12.13, U8.46 (mprj_io[28])
mprj_io[29]: J12.12, U8.44 (mprj_io[29])
mprj_io[30]: J12.11, U8.42 (mprj_io[30])
mprj_io[31]: J12.10, U8.40 (mprj_io[31])
mprj_io[32]: J12.9, U8.38 (mprj_io[32])
mprj_io[33]: J12.8, U8.36 (mprj_io[33])
mprj_io[34]: J12.4, U8.34 (mprj_io[34])
mprj_io[35]: J12.3, U8.32 (mprj_io[35])
mprj_io[36]: J12.2, U8.22 (mprj_io[36])
mprj_io[37]: J12.1, U8.20 (mprj_io[37])
vccd2: J11.21, U8.1 (vccd2)
vdda1: J11.16, U8.33 (vdda1)
vdda2: J11.25, U8.13 (vdda2)
xclk: J11.19, U8.9 (xclk), X1.3 (OUT)
~MEM_HOLD: J7.4, R12.1, U7.7 (~HOLD(D3))
~MEM_WP: J7.3, R9.1, U7.3 (~WP(D2))
~MR: SW1.1, U4.4 (~MR), U10.13 (B1)
~MR_L: U1.25 (ACBUS1), U10.2 (A1)
~RST: J12.5, U4.1 (~RST), U8.7 (~RST)

Notes on the sheet:
Serial Display
Flash memory interface with Caravel
Caravel Power Pin Headers
Power on Reset
Flash memory
Memory testing
FTDI interface with HKSPI
Power Pin Headers
LEDs
Voltage Regulator
IO Connectors
FTDI Module
USB Module
MEMS Oscillator
Buffers to enable FTDI UART interface
