efabless/caravel_board/hardware/caravel_breakout_WCSP/Caravel_breakout_WCSP.kicad_sch

## KiCad design hardware/caravel_breakout_WCSP/Caravel_breakout_WCSP.kicad_sch (2022-08-07)

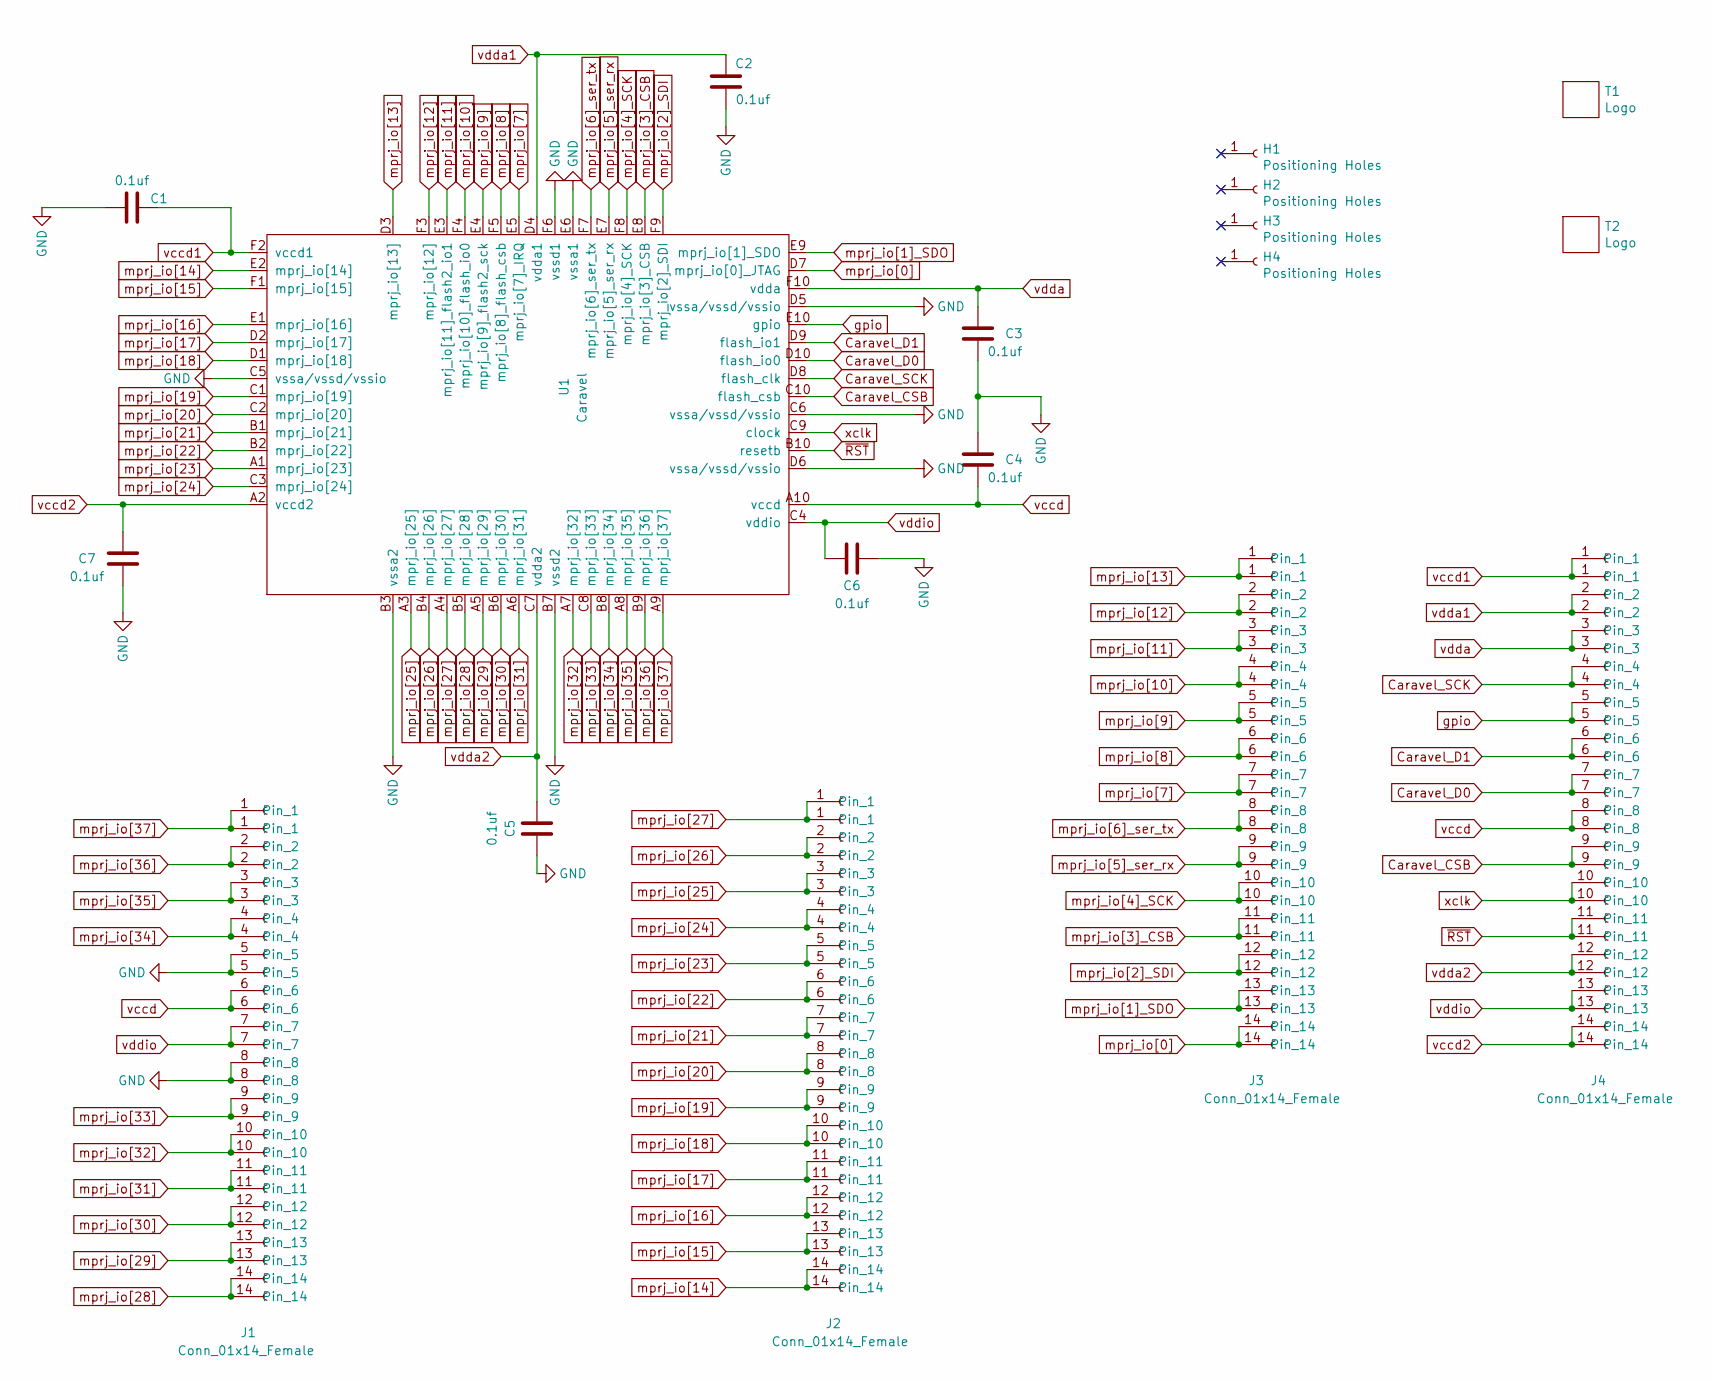
[picture p126: schematic Caravel_breakout_WCSP.kicad_sch]

Parts:
C1, C2, C3, C4, C5, C6, C7: 0.1uf; C_0603_1608Metric
H1, H2, H3, H4: Positioning Holes; MountingHole_2.2mm_M2_ISO7380_Pad
J1, J2, J3, J4: Conn_01x14_Female; Caravel_Breakout_Connectors_2x14
T1: Logo; logo
T2: Logo; ef_logo
U1: Caravel; Caravel_WCSP

Connections:
Caravel_CSB: J4.9, U1.C10 (flash_csb)
Caravel_D0: J4.7, U1.D10 (flash_io0)
Caravel_D1: J4.6, U1.D9 (flash_io1)
Caravel_SCK: J4.4, U1.D8 (flash_clk)
GND: C1.1, C2.2, C3.2, C4.1, C5.1, C6.1, C7.1, J1.5, J1.8, U1.B3 (vssa2), U1.B7 (vssd2), U1.C5 (vssa/vssd/vssio), U1.C6 (vssa/vssd/vssio), U1.D5 (vssa/vssd/vssio), U1.D6 (vssa/vssd/vssio), U1.E6 (vssa1), U1.F6 (vssd1)
gpio: J4.5, U1.E10 (gpio)
mprj_io[0]: J3.14, U1.D7 (mprj_io[0]_JTAG)
mprj_io[1]_SDO: J3.13, U1.E9 (mprj_io[1]_SDO)
mprj_io[2]_SDI: J3.12, U1.F9 (mprj_io[2]_SDI)
mprj_io[3]_CSB: J3.11, U1.E8 (mprj_io[3]_CSB)
mprj_io[4]_SCK: J3.10, U1.F8 (mprj_io[4]_SCK)
mprj_io[5]_ser_rx: J3.9, U1.E7 (mprj_io[5]_ser_rx)
mprj_io[6]_ser_tx: J3.8, U1.F7 (mprj_io[6]_ser_tx)
mprj_io[7]: J3.7, U1.E5 (mprj_io[7]_IRQ)
mprj_io[8]: J3.6, U1.F5 (mprj_io[8]_flash_csb)
mprj_io[9]: J3.5, U1.E4 (mprj_io[9]_flash2_sck)
mprj_io[10]: J3.4, U1.F4 (mprj_io[10]_flash_io0)
mprj_io[11]: J3.3, U1.E3 (mprj_io[11]_flash2_io1)
mprj_io[12]: J3.2, U1.F3 (mprj_io[12])
mprj_io[13]: J3.1, U1.D3 (mprj_io[13])
mprj_io[14]: J2.14, U1.E2 (mprj_io[14])
mprj_io[15]: J2.13, U1.F1 (mprj_io[15])
mprj_io[16]: J2.12, U1.E1 (mprj_io[16])
mprj_io[17]: J2.11, U1.D2 (mprj_io[17])
mprj_io[18]: J2.10, U1.D1 (mprj_io[18])
mprj_io[19]: J2.9, U1.C1 (mprj_io[19])
mprj_io[20]: J2.8, U1.C2 (mprj_io[20])
mprj_io[21]: J2.7, U1.B1 (mprj_io[21])
mprj_io[22]: J2.6, U1.B2 (mprj_io[22])
mprj_io[23]: J2.5, U1.A1 (mprj_io[23])
mprj_io[24]: J2.4, U1.C3 (mprj_io[24])
mprj_io[25]: J2.3, U1.A3 (mprj_io[25])
mprj_io[26]: J2.2, U1.B4 (mprj_io[26])
mprj_io[27]: J2.1, U1.A4 (mprj_io[27])
mprj_io[28]: J1.14, U1.B5 (mprj_io[28])
mprj_io[29]: J1.13, U1.A5 (mprj_io[29])
mprj_io[30]: J1.12, U1.B6 (mprj_io[30])
mprj_io[31]: J1.11, U1.A6 (mprj_io[31])
mprj_io[32]: J1.10, U1.A7 (mprj_io[32])
mprj_io[33]: J1.9, U1.C8 (mprj_io[33])
mprj_io[34]: J1.4, U1.B8 (mprj_io[34])
mprj_io[35]: J1.3, U1.A8 (mprj_io[35])
mprj_io[36]: J1.2, U1.B9 (mprj_io[36])
mprj_io[37]: J1.1, U1.A9 (mprj_io[37])
vccd: C4.2, J1.6, J4.8, U1.A10 (vccd)
vccd1: C1.2, J4.1, U1.F2 (vccd1)
vccd2: C7.2, J4.14, U1.A2 (vccd2)
vdda: C3.1, J4.3, U1.F10 (vdda)
vdda1: C2.1, J4.2, U1.D4 (vdda1)
vdda2: C5.2, J4.12, U1.C7 (vdda2)
vddio: C6.2, J1.7, J4.13, U1.C4 (vddio)
xclk: J4.10, U1.C9 (clock)
~RST: J4.11, U1.B10 (resetb)
