efabless/caravel_board/hardware/caravel_pcb_v3_FTDI/caravel_pcb_v3_FTDI.kicad_sch

## KiCad design hardware/caravel_pcb_v3_FTDI/caravel_pcb_v3_FTDI.kicad_sch (2022-06-28)

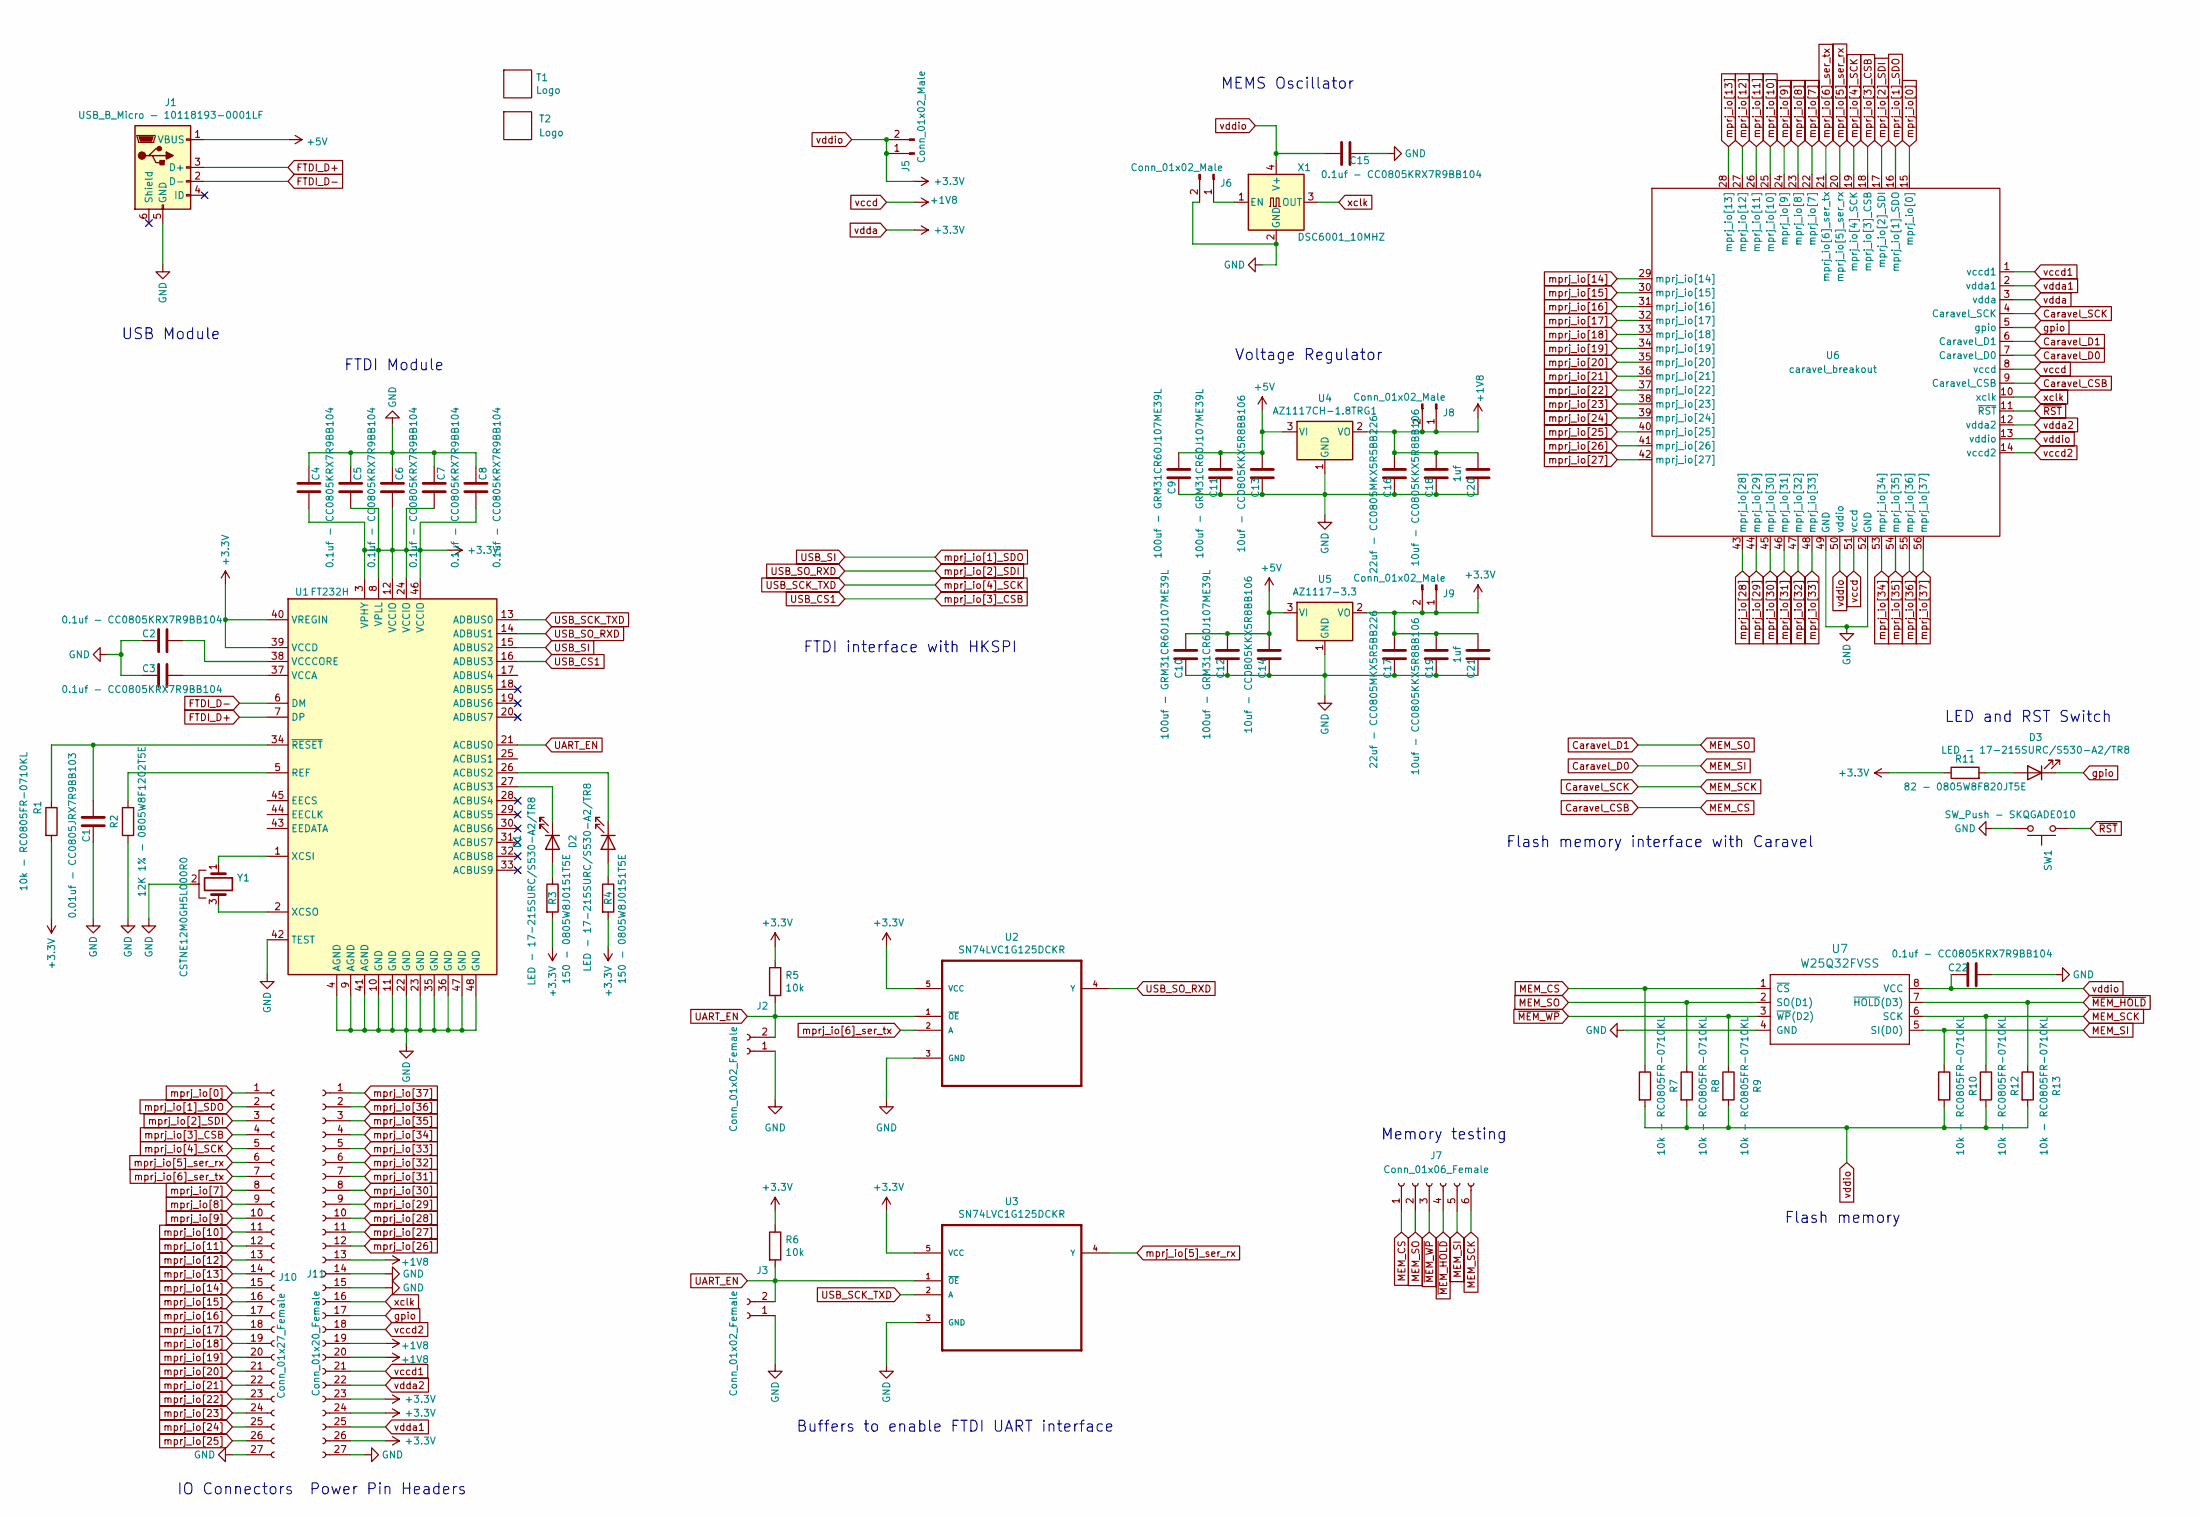
[picture p127: schematic caravel_pcb_v3_FTDI.kicad_sch]

Parts:
C1: 0.01uf - CC0805JRX7R9BB103; C_0805_2012Metric
C2, C3, C4, C5, C6, C7, C8, C15, C22: 0.1uf - CC0805KRX7R9BB104; C_0805_2012Metric
C9, C10, C11, C12: 100uf - GRM31CR60J107ME39L; C_1206_3216Metric
C13, C14, C18, C19: 10uf - CC0805KKX5R8BB106; C_0805_2012Metric
C16, C17: 22uf - CC0805MKX5R5BB226; C_0805_2012Metric
C20, C21: 1uf; C_0805_2012Metric
D1, D2, D3: LED - 17-215SURC/S530-A2/TR8; LED_1206_3216Metric
J1: USB_B_Micro - 10118193-0001LF; FCI_10118193-0001LF
J2, J3: Conn_01x02_Female; PinHeader_1x02_P2.54mm_Vertical
J5, J6, J8, J9: Conn_01x02_Male; PinHeader_1x02_P2.54mm_Vertical
J7: Conn_01x06_Female; PinHeader_1x06_P2.54mm_Vertical
J10: Conn_01x27_Female; PinHeader_1x27_P2.54mm_Vertical
J11: Conn_01x20_Female; PinHeader_1x20_P2.54mm_Vertical
R1, R7, R8, R9, R10, R12, R13: 10k - RC0805FR-0710KL; R_0805_2012Metric
R2: 12K 1% - 0805W8F1202T5E; R_0805_2012Metric
R3, R4: 150 - 0805W8J0151T5E; R_0805_2012Metric
R5, R6: 10k; R_0805_2012Metric
R11: 82 - 0805W8F820JT5E; R_0805_2012Metric
SW1: SW_Push - SKQGADE010; SW4-SMD-5.2X5.2X1.5MM
T1: Logo; logo
T2: Logo; ef_logo
U1: FT232H; QFN-48-1EP_8x8mm_P0.5mm_EP6.2x6.2mm
U2, U3: SN74LVC1G125DCKR; SOT65P210X110-5N
U4: AZ1117CH-1.8TRG1; SOT-223
U5: AZ1117-3.3; SOT-223
U6: caravel_breakout; caravel_breakout_flexy
U7: W25Q32FVSS; SOIC127P790X216-8N
X1: DSC6001_10MHZ; DSC6001JE1A-010.0000
Y1: CSTNE12M0GH5L000R0

Connections:
+1V8: C16.2, C18.2, C20.2, J8.1, J8.2, J11.13, J11.19, J11.20, U4.2 (VO), U6.8 (vccd), U6.51 (vccd)
+3.3V: C4.2, C5.2, C6.2, C7.2, C8.2, C15.2, C17.2, C19.2, C21.2, C22.1, J5.1, J5.2, J9.1, J9.2, J11.23, J11.24, J11.26, R1.2, R3.2, R4.2, R5.1, R6.1, R7.2, R8.2, R9.2, R10.2, R11.1, R12.2, R13.2, U1.3 (VPHY), U1.8 (VPLL), U1.12 (VCCIO), U1.24 (VCCIO), U1.39 (VCCD), U1.40 (VREGIN), U1.46 (VCCIO), U2.5 (VCC), U3.5 (VCC), U5.2 (VO), U6.3 (vdda), U6.13 (vddio), U6.50 (vddio), U7.8 (VCC), X1.4 (V+)
+5V: C9.2, C10.2, C11.2, C12.2, C13.2, C14.2, J1.1 (VBUS), U4.3 (VI), U5.3 (VI)
Caravel_CSB: J7.1, R7.1, U6.9 (Caravel_CSB), U7.1 (~CS)
Caravel_D0: J7.5, R10.1, U6.7 (Caravel_D0), U7.5 (SI(D0))
Caravel_D1: J7.2, R8.1, U6.6 (Caravel_D1), U7.2 (SO(D1))
Caravel_SCK: J7.6, R12.1, U6.4 (Caravel_SCK), U7.6 (SCK)
FTDI_D+: J1.3 (D+), U1.7 (DP)
FTDI_D-: J1.2 (D-), U1.6 (DM)
GND: C1.1, C2.1, C3.1, C4.1, C5.1, C6.1, C7.1, C8.1, C9.1, C10.1, C11.1, C12.1, C13.1, C14.1, C15.1, C16.1, C17.1, C18.1, C19.1, C20.1, C21.1, C22.2, J1.5 (GND), J2.1, J3.1, J6.2, J11.14, J11.15, R2.1, SW1.2, U1.4 (AGND), U1.9 (AGND), U1.10 (GND), U1.11 (GND), U1.22 (GND), U1.23 (GND), U1.35 (GND), U1.36 (GND), U1.41 (AGND), U1.42 (TEST), U1.47 (GND), U1.48 (GND), U2.3 (GND), U3.3 (GND), U4.1 (GND), U5.1 (GND), U6.49 (GND), U6.52 (GND), U7.4 (GND), X1.2 (GND), Y1.2
unnamed: C1.2, R1.1, U1.34 (~RESET)
unnamed: C2.2, U1.38 (VCCCORE)
unnamed: C3.2, U1.37 (VCCA)
unnamed: D1.1 (K), U1.27 (ACBUS3)
unnamed: D1.2 (A), R3.1
unnamed: D2.1 (K), U1.26 (ACBUS2)
unnamed: D2.2 (A), R4.1
unnamed: D3.2 (A), R11.2
unnamed: J6.1, X1.1 (EN)
unnamed: R2.2, U1.5 (REF)
unnamed: U1.1 (XCSI), Y1.1
unnamed: U1.2 (XCSO), Y1.3
UART_EN: J2.2, J3.2, R5.2, R6.2, U1.21 (ACBUS0), U2.1 (~OE), U3.1 (~OE)
gpio: D3.1 (K), J11.17, U6.5 (gpio)
mprj_io[0]: J10.1, U6.15 (mprj_io[0])
mprj_io[1]_SDO: J10.2, U1.15 (ADBUS2), U6.16 (mprj_io[1]_SDO)
mprj_io[2]_SDI: J10.3, U1.14 (ADBUS1), U2.4 (Y), U6.17 (mprj_io[2]_SDI)
mprj_io[3]_CSB: J10.4, U1.16 (ADBUS3), U6.18 (mprj_io[3]_CSB)
mprj_io[4]_SCK: J10.5, U1.13 (ADBUS0), U3.2 (A), U6.19 (mprj_io[4]_SCK)
mprj_io[5]_ser_rx: J10.6, U3.4 (Y), U6.20 (mprj_io[5]_ser_rx)
mprj_io[6]_ser_tx: J10.7, U2.2 (A), U6.21 (mprj_io[6]_ser_tx)
mprj_io[7]: J10.8, U6.22 (mprj_io[7])
mprj_io[8]: J10.9, U6.23 (mprj_io[8])
mprj_io[9]: J10.10, U6.24 (mprj_io[9])
mprj_io[10]: J10.11, U6.25 (mprj_io[10])
mprj_io[11]: J10.12, U6.26 (mprj_io[11])
mprj_io[12]: J10.13, U6.27 (mprj_io[12])
mprj_io[13]: J10.14, U6.28 (mprj_io[13])
mprj_io[14]: J10.15, U6.29 (mprj_io[14])
mprj_io[15]: J10.16, U6.30 (mprj_io[15])
mprj_io[16]: J10.17, U6.31 (mprj_io[16])
mprj_io[17]: J10.18, U6.32 (mprj_io[17])
mprj_io[18]: J10.19, U6.33 (mprj_io[18])
mprj_io[19]: J10.20, U6.34 (mprj_io[19])
mprj_io[20]: J10.21, U6.35 (mprj_io[20])
mprj_io[21]: J10.22, U6.36 (mprj_io[21])
mprj_io[22]: J10.23, U6.37 (mprj_io[22])
mprj_io[23]: J10.24, U6.38 (mprj_io[23])
mprj_io[24]: J10.25, U6.39 (mprj_io[24])
mprj_io[25]: J10.26, U6.40 (mprj_io[25])
mprj_io[26]: J11.12, U6.41 (mprj_io[26])
mprj_io[27]: J11.11, U6.42 (mprj_io[27])
mprj_io[28]: J11.10, U6.43 (mprj_io[28])
mprj_io[29]: J11.9, U6.44 (mprj_io[29])
mprj_io[30]: J11.8, U6.45 (mprj_io[30])
mprj_io[31]: J11.7, U6.46 (mprj_io[31])
mprj_io[32]: J11.6, U6.47 (mprj_io[32])
mprj_io[33]: J11.5, U6.48 (mprj_io[33])
mprj_io[34]: J11.4, U6.53 (mprj_io[34])
mprj_io[35]: J11.3, U6.54 (mprj_io[35])
mprj_io[36]: J11.2, U6.55 (mprj_io[36])
mprj_io[37]: J11.1, U6.56 (mprj_io[37])
vccd1: J11.21, U6.1 (vccd1)
vccd2: J11.18, U6.14 (vccd2)
vdda1: J11.25, U6.2 (vdda1)
vdda2: J11.22, U6.12 (vdda2)
xclk: J11.16, U6.10 (xclk), X1.3 (OUT)
~MEM_HOLD: J7.4, R13.1, U7.7 (~HOLD(D3))
~MEM_WP: J7.3, R9.1, U7.3 (~WP(D2))
~RST: SW1.1, U6.11 (~RST)

Notes on the sheet:
LED and RST Switch
Flash memory interface with Caravel
Flash memory
Memory testing
FTDI interface with HKSPI
Power Pin Headers
Voltage Regulator
IO Connectors
FTDI Module
USB Module
MEMS Oscillator
Buffers to enable FTDI UART interface
