efabless/caravel_board/firmware/mpw2-5/nucleo/config_io_o.c

#include "../defs.h"
#include "gpio_config_io.c"
#include "send_packet.c"

void set_registers() {

    reg_mprj_io_0 = GPIO_MODE_MGMT_STD_INPUT_PULLDOWN;
    reg_mprj_io_1 = GPIO_MODE_MGMT_STD_OUTPUT;
    reg_mprj_io_2 = GPIO_MODE_MGMT_STD_OUTPUT;
    reg_mprj_io_3 = GPIO_MODE_MGMT_STD_OUTPUT;
    reg_mprj_io_4 = GPIO_MODE_MGMT_STD_OUTPUT;
    reg_mprj_io_5 = GPIO_MODE_MGMT_STD_OUTPUT;
    reg_mprj_io_6 = GPIO_MODE_MGMT_STD_OUTPUT;
    reg_mprj_io_7 = GPIO_MODE_MGMT_STD_OUTPUT;
    reg_mprj_io_8 = GPIO_MODE_MGMT_STD_OUTPUT;
    reg_mprj_io_9 = GPIO_MODE_MGMT_STD_OUTPUT;
    reg_mprj_io_10 = GPIO_MODE_MGMT_STD_OUTPUT;
    reg_mprj_io_11 = GPIO_MODE_MGMT_STD_OUTPUT;
    reg_mprj_io_12 = GPIO_MODE_MGMT_STD_OUTPUT;
    reg_mprj_io_13 = GPIO_MODE_MGMT_STD_OUTPUT;
    reg_mprj_io_14 = GPIO_MODE_MGMT_STD_OUTPUT;
    reg_mprj_io_15 = GPIO_MODE_MGMT_STD_OUTPUT;
    reg_mprj_io_16 = GPIO_MODE_MGMT_STD_OUTPUT;
    reg_mprj_io_17 = GPIO_MODE_MGMT_STD_OUTPUT;
    reg_mprj_io_18 = GPIO_MODE_MGMT_STD_OUTPUT;

    reg_mprj_io_19 = GPIO_MODE_MGMT_STD_OUTPUT;
    reg_mprj_io_20 = GPIO_MODE_MGMT_STD_OUTPUT;
    reg_mprj_io_21 = GPIO_MODE_MGMT_STD_OUTPUT;
    reg_mprj_io_22 = GPIO_MODE_MGMT_STD_OUTPUT;
    reg_mprj_io_23 = GPIO_MODE_MGMT_STD_OUTPUT;
    reg_mprj_io_24 = GPIO_MODE_MGMT_STD_OUTPUT;
    reg_mprj_io_25 = GPIO_MODE_MGMT_STD_OUTPUT;
    reg_mprj_io_26 = GPIO_MODE_MGMT_STD_OUTPUT;
    reg_mprj_io_27 = GPIO_MODE_MGMT_STD_OUTPUT;
    reg_mprj_io_28 = GPIO_MODE_MGMT_STD_OUTPUT;
    reg_mprj_io_29 = GPIO_MODE_MGMT_STD_OUTPUT;
    reg_mprj_io_30 = GPIO_MODE_MGMT_STD_OUTPUT;
    reg_mprj_io_31 = GPIO_MODE_MGMT_STD_OUTPUT;
    reg_mprj_io_32 = GPIO_MODE_MGMT_STD_OUTPUT;
    reg_mprj_io_33 = GPIO_MODE_MGMT_STD_OUTPUT;
    reg_mprj_io_34 = GPIO_MODE_MGMT_STD_OUTPUT;
//    reg_mprj_io_34 = 0x0403;
    reg_mprj_io_35 = GPIO_MODE_MGMT_STD_OUTPUT;
    reg_mprj_io_36 = GPIO_MODE_MGMT_STD_OUTPUT;
    reg_mprj_io_37 = GPIO_MODE_MGMT_STD_OUTPUT;
//    reg_mprj_io_37 = GPIO_MODE_MGMT_STD_INPUT_PULLDOWN;
//    reg_mprj_io_37 = 0x0403;

}

void main()
{
	int i,j,high_chain_io;
    int num_pulses = 4;
    //int num_bits = 19;
    //configure_io0_37();

    reg_gpio_mode1 = 1;
    reg_gpio_mode0 = 0;
    reg_gpio_ien = 1;
    reg_gpio_oe = 1;
    int old_received;
    int received;

    set_registers();
    reg_mprj_datah = 0;
    reg_mprj_datal = 0;
    gpio_config_io();

    reg_gpio_out = 1; // OFF
    int flag = 0;
    int mask;
    int mask_io37 = 0x1 << 5;
    int mask_io0 = 0x1;
    int io_num = 0;
    int received_bit;
    // send_packet_io0(2);

    while (1){
//        flag = receive_io37();
        flag = receive_io0();
        // if (flag == 2){
        //     io_num = 0;
        //     flag = 1;
        //     // send_packet_io0(4);
        // }
        if (flag == 1){
            
            io_num++;
            mask = 0;
            high_chain_io = 37 - io_num;
            int counter = 0;
            while(1){
//                old_received = reg_mprj_datah & mask_io37;
                old_received = reg_mprj_datal & mask_io0;
                while(1){
//                    received = reg_mprj_datah & mask_io37;
                    received = reg_mprj_datal & mask_io0;
                    if (received != old_received){
                        // send_packet_io0(4);
//                        received_bit = received >> 5;
                        received_bit = received;
                        if (high_chain_io<32){
                            mask = received_bit << io_num;
                            mask = mask | received_bit << high_chain_io;
                        }
                        else{
                            mask = received_bit << io_num;
                        }
                        if (high_chain_io>=32){
                            reg_mprj_datah = received_bit << high_chain_io-32;
                        }
                        reg_mprj_datal = mask;
                        // old_received = received;
                        // send_packet_io0(4);
                        counter++;
                        break;
                    }
                }
                if (counter == 4){
                    count_down(PULSE_WIDTH*10);
                    break;
                }
            }
        }
            
    }

}
