efabless/caravel_board/firmware/mpw2-5/nucleo/gpio_config_data.c

char config_stream[] = { 0xf7, 0x26, 0x26, 0x26, 0x26, 0x66, 0x66, 0x66, 0x66, 0x66, 0x06, 0x06, 0x06, 0x26, 0x26, 0x26, 0x26, 0x66, 0x66, 0x66, 0x66, 0x66, 0x06, 0x06, 0x06, 0x26, 0x26, 0x26, 0x26, 0x66, 0x66, 0x66, 0x66, 0x66, 0x06, 0x06, 0x06, 0x26, 0x26, 0x26, 0x26, 0x66, 0x66, 0x66, 0x66, 0x66, 0x06, 0x06, 0x06, 0x26, 0x26, 0x26, 0x26, 0x66, 0x66, 0x66, 0x66, 0x66, 0x06, 0x06, 0x06, 0x26, 0x26, 0x26, 0x26, 0x66, 0x66, 0x66, 0x66, 0x66, 0x06, 0x06, 0x06, 0x26, 0x26, 0x26, 0x26, 0x66, 0x66, 0x66, 0x66, 0x66, 0x06, 0x06, 0x06, 0x06, 0x26, 0x26, 0x26, 0x66, 0x66, 0x66, 0x66, 0x66, 0x06, 0x06, 0x06, 0x06, 0x06, 0x26, 0x26, 0x66, 0x66, 0x66, 0x66, 0x66, 0x06, 0x06, 0x06, 0x06, 0x06, 0x06, 0x26, 0x66, 0x66, 0x66, 0x66, 0x66, 0x06, 0x06, 0x06, 0x06, 0x06, 0x06, 0x26, 0x66, 0x66, 0x66, 0x66, 0x66, 0x06, 0x06, 0x06, 0x06, 0x06, 0x06, 0x06, 0x66, 0x66, 0x66, 0x66, 0x66, 0x06, 0x06, 0x06, 0x06, 0x06, 0x06, 0x06, 0x46, 0x66, 0x66, 0x66, 0x66, 0x06, 0x06, 0x06, 0x06, 0x06, 0x06, 0x06, 0x46, 0x66, 0x66, 0x66, 0x66, 0x06, 0x06, 0x06, 0x06, 0x06, 0x06, 0x06, 0x46, 0x46, 0x66, 0x66, 0x66, 0x06, 0x06, 0x06, 0x06, 0x06, 0x06, 0x06, 0x06, 0x46, 0x66, 0x66, 0x66, 0x06, 0x06, 0x06, 0x06, 0x06, 0x06, 0x06, 0x06, 0x06, 0x66, 0x66, 0x66, 0x06, 0x06, 0x06, 0x06, 0x06, 0x06, 0x06, 0x06, 0x06, 0x46, 0x66, 0x66, 0x06, 0x06, 0x06, 0x06, 0x06, 0x06, 0x06, 0x06, 0x06, 0x06, 0x66, 0x46, 0x06, 0x06, 0x06, 0x06, 0x06, 0x06, 0x06, 0x06, 0x06, 0x26, 0x66, 0x00, 0x00, 0x00, 0x00, 0x00, 0x00, 0x00, 0x00, 0x00, 0x00, 0x00 };
