efabless/caravel_board/firmware/mpw1/util/slippage.py

#!/bin/env python3
#
# slippage.py ---  Analyze a GPIO configuration setting for Caravel ChipIgnite one.
#
# Input:   Intended configuration setting bits for GPIO 0 to 18
# Output:  Required configuration setting bits for GPIO 0 to 18
#

gpio_0  = 0x0403	# user input
gpio_1  = 0x1803	# management output (SDO)
gpio_2  = 0x0403	# management input  (SDI)
gpio_3  = 0x0402	# management input  (SCK)
gpio_4  = 0x0402	# management input  (CSB)
gpio_5  = 0x0402	# management input  (UART Rx)
gpio_6  = 0x1808	# management output (UART Tx)
gpio_7  = 0x0403	# user input
gpio_8  = 0x1808	# management output
gpio_9  = 0x0403	# user input
gpio_10 = 0x1808	# management output
gpio_11 = 0x0403	# user input
gpio_12 = 0x1808	# management output
gpio_13 = 0x0403	# user input
gpio_14 = 0x1808	# management output
gpio_15 = 0x0403	# user input
gpio_16 = 0x1808	# management output
gpio_17 = 0x0403	# user input
gpio_18 = 0x1808	# management output

gpio_0_bin  = "{:013b}".format(gpio_0)
gpio_1_bin  = "{:013b}".format(gpio_1)
gpio_2_bin  = "{:013b}".format(gpio_2)
gpio_3_bin  = "{:013b}".format(gpio_3)
gpio_4_bin  = "{:013b}".format(gpio_4)
gpio_5_bin  = "{:013b}".format(gpio_5)
gpio_6_bin  = "{:013b}".format(gpio_6)
gpio_7_bin  = "{:013b}".format(gpio_7)
gpio_8_bin  = "{:013b}".format(gpio_8)
gpio_9_bin  = "{:013b}".format(gpio_9)
gpio_10_bin = "{:013b}".format(gpio_10)
gpio_11_bin = "{:013b}".format(gpio_11)
gpio_12_bin = "{:013b}".format(gpio_12)
gpio_13_bin = "{:013b}".format(gpio_13)
gpio_14_bin = "{:013b}".format(gpio_14)
gpio_15_bin = "{:013b}".format(gpio_15)
gpio_16_bin = "{:013b}".format(gpio_16)
gpio_17_bin = "{:013b}".format(gpio_17)
gpio_18_bin = "{:013b}".format(gpio_18)

# Print in hex
print('')
print('Input:')
print('')
print('reg_mprj_io_0  = 0x' + '{0:0>4x}'.format(int(gpio_0_bin, 2)))
print('reg_mprj_io_1  = 0x' + '{0:0>4x}'.format(int(gpio_1_bin, 2)))
print('reg_mprj_io_2  = 0x' + '{0:0>4x}'.format(int(gpio_2_bin, 2)))
print('reg_mprj_io_3  = 0x' + '{0:0>4x}'.format(int(gpio_3_bin, 2)))
print('reg_mprj_io_4  = 0x' + '{0:0>4x}'.format(int(gpio_4_bin, 2)))
print('reg_mprj_io_5  = 0x' + '{0:0>4x}'.format(int(gpio_5_bin, 2)))
print('reg_mprj_io_6  = 0x' + '{0:0>4x}'.format(int(gpio_6_bin, 2)))
print('reg_mprj_io_7  = 0x' + '{0:0>4x}'.format(int(gpio_7_bin, 2)))
print('reg_mprj_io_8  = 0x' + '{0:0>4x}'.format(int(gpio_8_bin, 2)))
print('reg_mprj_io_9  = 0x' + '{0:0>4x}'.format(int(gpio_9_bin, 2)))
print('reg_mprj_io_10 = 0x' + '{0:0>4x}'.format(int(gpio_10_bin, 2)))
print('reg_mprj_io_11 = 0x' + '{0:0>4x}'.format(int(gpio_11_bin, 2)))
print('reg_mprj_io_12 = 0x' + '{0:0>4x}'.format(int(gpio_12_bin, 2)))
print('reg_mprj_io_13 = 0x' + '{0:0>4x}'.format(int(gpio_13_bin, 2)))
print('reg_mprj_io_14 = 0x' + '{0:0>4x}'.format(int(gpio_14_bin, 2)))
print('reg_mprj_io_15 = 0x' + '{0:0>4x}'.format(int(gpio_15_bin, 2)))
print('reg_mprj_io_16 = 0x' + '{0:0>4x}'.format(int(gpio_16_bin, 2)))
print('reg_mprj_io_17 = 0x' + '{0:0>4x}'.format(int(gpio_17_bin, 2)))
print('reg_mprj_io_18 = 0x' + '{0:0>4x}'.format(int(gpio_18_bin, 2)))
print('')
print('')

gpio_0_bits  = list(gpio_0_bin)
gpio_1_bits  = list(gpio_1_bin)
gpio_2_bits  = list(gpio_2_bin)
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
        gpio_16_actual[0] = '0'
        gpio_17_actual[12] = '1'
        print('   GPIO 17 changed mgmt mode to preserve output mode on GPIO 16')
    else:
        print('   This is unresolvable (implementation must change).')
        gpio_16_good = False

if dm_17 != dm_17_actual:
    print('GPIO 17 digital mode changed from ' + ''.join(dm_17) +
	    ' to ' + ''.join(dm_17_actual))
    if dm_17[0] == '0':
        dm_17_actual[1] = '1'
        gpio_17_actual[1] = '1'
        print('   GPIO 17 digital mode adjusted to ' + ''.join(dm_17_actual) +
		' (weak output)')
    elif dm_17[0] == '1' and dm_18[0] == '0':
        gpio_17_actual[0] = '0'
        gpio_18_actual[12] = '1'
        print('   GPIO 18 changed mgmt mode to preserve output mode on GPIO 17')
    else:
        print('   This is unresolvable (implementation must change).')
        gpio_17_good = False

# Summarize good and bad configurations

print('')
print('GPIO summary:')
print('')
print('GPIO 0:  good' if gpio_0_good else 'GPIO 0:  bad')
print('GPIO 1:  good' if gpio_1_good else 'GPIO 1:  bad')
print('GPIO 2:  good' if gpio_2_good else 'GPIO 2:  bad')
print('GPIO 3:  good' if gpio_3_good else 'GPIO 3:  bad')
print('GPIO 4:  good' if gpio_4_good else 'GPIO 4:  bad')
print('GPIO 5:  good' if gpio_5_good else 'GPIO 5:  bad')
print('GPIO 6:  good' if gpio_6_good else 'GPIO 6:  bad')
print('GPIO 7:  good' if gpio_7_good else 'GPIO 7:  bad')
print('GPIO 8:  good' if gpio_8_good else 'GPIO 8:  bad')
print('GPIO 9:  good' if gpio_9_good else 'GPIO 9:  bad')
print('GPIO 10: good' if gpio_10_good else 'GPIO 10: bad')
print('GPIO 11: good' if gpio_11_good else 'GPIO 11: bad')
print('GPIO 12: good' if gpio_12_good else 'GPIO 12: bad')
print('GPIO 13: good' if gpio_13_good else 'GPIO 13: bad')
print('GPIO 14: good' if gpio_14_good else 'GPIO 14: bad')
print('GPIO 15: good' if gpio_15_good else 'GPIO 15: bad')
print('GPIO 16: good' if gpio_16_good else 'GPIO 16: bad')
print('GPIO 17: good' if gpio_17_good else 'GPIO 17: bad')
print('GPIO 18: good' if gpio_18_good else 'GPIO 18: bad')

# Remove slipped bit, compressing output from 13 bits to 12

gpio_0_out = gpio_1_actual[12:13]   + gpio_0_actual[1:13]
gpio_1_out = gpio_2_actual[11:13]   + gpio_1_actual[1:12]
gpio_2_out = gpio_3_actual[10:13]   + gpio_2_actual[1:11]
gpio_3_out = gpio_4_actual[9:13]    + gpio_3_actual[1:10]
gpio_4_out = gpio_5_actual[8:13]    + gpio_4_actual[1:9]
gpio_5_out = gpio_6_actual[7:13]    + gpio_5_actual[1:8]
gpio_6_out = gpio_7_actual[6:13]    + gpio_6_actual[1:7]
gpio_7_out = gpio_8_actual[5:13]    + gpio_7_actual[1:6]
gpio_8_out = gpio_9_actual[4:13]    + gpio_8_actual[1:5]
gpio_9_out = gpio_10_actual[3:13]   + gpio_9_actual[1:4]
gpio_10_out = gpio_11_actual[2:13]  + gpio_10_actual[1:3]
gpio_11_out = gpio_12_actual[1:13]  + gpio_11_actual[1:2]
gpio_12_out = gpio_14_actual[12:13] + gpio_13_actual[1:13]
gpio_13_out = gpio_15_actual[11:13] + gpio_14_actual[1:12]
gpio_14_out = gpio_16_actual[10:13] + gpio_15_actual[1:11]
gpio_15_out = gpio_17_actual[9:13]  + gpio_16_actual[1:10]
gpio_16_out = gpio_18_actual[8:13]  + gpio_17_actual[1:9]
gpio_17_out = list('00000')         + gpio_18_actual[0:8]
gpio_18_out = list('0000000000000')

# Convert back to strings

gpio_0_config =  ''.join(gpio_0_out)
gpio_1_config =  ''.join(gpio_1_out)
gpio_2_config =  ''.join(gpio_2_out)
gpio_3_config =  ''.join(gpio_3_out)
gpio_4_config =  ''.join(gpio_4_out)
gpio_5_config =  ''.join(gpio_5_out)
gpio_6_config =  ''.join(gpio_6_out)
gpio_7_config =  ''.join(gpio_7_out)
gpio_8_config =  ''.join(gpio_8_out)
gpio_9_config =  ''.join(gpio_9_out)
gpio_10_config = ''.join(gpio_10_out)
gpio_11_config = ''.join(gpio_11_out)
gpio_12_config = ''.join(gpio_12_out)
gpio_13_config = ''.join(gpio_13_out)
gpio_14_config = ''.join(gpio_14_out)
gpio_15_config = ''.join(gpio_15_out)
gpio_16_config = ''.join(gpio_16_out)
gpio_17_config = ''.join(gpio_17_out)
gpio_18_config = ''.join(gpio_18_out)

# Print in hex
print('')
print('Output:')
print('')
print('reg_mprj_io_0  = 0x' + '{0:0>4x};'.format(int(gpio_0_config, 2)))
print('reg_mprj_io_1  = 0x' + '{0:0>4x};'.format(int(gpio_1_config, 2)))
print('reg_mprj_io_2  = 0x' + '{0:0>4x};'.format(int(gpio_2_config, 2)))
print('reg_mprj_io_3  = 0x' + '{0:0>4x};'.format(int(gpio_3_config, 2)))
print('reg_mprj_io_4  = 0x' + '{0:0>4x};'.format(int(gpio_4_config, 2)))
print('reg_mprj_io_5  = 0x' + '{0:0>4x};'.format(int(gpio_5_config, 2)))
print('reg_mprj_io_6  = 0x' + '{0:0>4x};'.format(int(gpio_6_config, 2)))
print('reg_mprj_io_7  = 0x' + '{0:0>4x};'.format(int(gpio_7_config, 2)))
print('reg_mprj_io_8  = 0x' + '{0:0>4x};'.format(int(gpio_8_config, 2)))
print('reg_mprj_io_9  = 0x' + '{0:0>4x};'.format(int(gpio_9_config, 2)))
print('reg_mprj_io_10 = 0x' + '{0:0>4x};'.format(int(gpio_10_config, 2)))
print('reg_mprj_io_11 = 0x' + '{0:0>4x};'.format(int(gpio_11_config, 2)))
print('reg_mprj_io_12 = 0x' + '{0:0>4x};'.format(int(gpio_12_config, 2)))
print('reg_mprj_io_13 = 0x' + '{0:0>4x};'.format(int(gpio_13_config, 2)))
print('reg_mprj_io_14 = 0x' + '{0:0>4x};'.format(int(gpio_14_config, 2)))
print('reg_mprj_io_15 = 0x' + '{0:0>4x};'.format(int(gpio_15_config, 2)))
print('reg_mprj_io_16 = 0x' + '{0:0>4x};'.format(int(gpio_16_config, 2)))
print('reg_mprj_io_17 = 0x' + '{0:0>4x};'.format(int(gpio_17_config, 2)))
print('reg_mprj_io_18 = 0x' + '{0:0>4x};'.format(int(gpio_18_config, 2)))
