efabless/caravel_board/firmware/mpw2-5/matt_test/gpio_config_data_pwm_F1_7.c

char config_stream[] = {0x06, 0x06, 0x06, 0x06, 0x06, 0x46, 0x46, 0x46, 0x46, 0x46, 0x06, 0x06, 0x06, 0x06, 0x06, 0x06, 0x06, 0x46, 0x46, 0x46, 0x46, 0x46, 0x06, 0x06, 0x26, 0x26, 0x26, 0x26, 0x26, 0x66, 0x66, 0x66, 0x66, 0x66, 0x06, 0x06, 0x06, 0x26, 0x26, 0x26, 0x26, 0x66, 0x66, 0x66, 0x66, 0x66, 0x06, 0x06, 0x06, 0x26, 0x26, 0x26, 0x26, 0x66, 0x66, 0x66, 0x66, 0x66, 0x06, 0x06, 0x06, 0x26, 0x26, 0x26, 0x26, 0x66, 0x66, 0x66, 0x66, 0x66, 0x06, 0x06, 0x06, 0x26, 0x26, 0x26, 0x26, 0x66, 0x66, 0x66, 0x66, 0x66, 0x06, 0x06, 0x06, 0x06, 0x26, 0x26, 0x26, 0x66, 0x66, 0x66, 0x66, 0x66, 0x06, 0x06, 0x06, 0x06, 0x06, 0x26, 0x26, 0x66, 0x66, 0x66, 0x66, 0x66, 0x06, 0x06, 0x06, 0x06, 0x06, 0x26, 0x26, 0x26, 0x66, 0x66, 0x66, 0x66, 0x46, 0x06, 0x06, 0x06, 0x06, 0x26, 0x26, 0x26, 0x66, 0x66, 0x66, 0x46, 0x46, 0x06, 0x06, 0x06, 0x26, 0x26, 0x26, 0x26, 0x66, 0x66, 0x26, 0x66, 0x46, 0x06, 0x06, 0x06, 0x06, 0x06, 0x26, 0x26, 0x26, 0x66, 0x26, 0x66, 0x46, 0x06, 0x06, 0x06, 0x06, 0x06, 0x26, 0x26, 0x26, 0x66, 0x26, 0x46, 0x46, 0x06, 0x06, 0x06, 0x06, 0x06, 0x26, 0x26, 0x26, 0x66, 0x66, 0x46, 0x06, 0x06, 0x06, 0x06, 0x06, 0x06, 0x06, 0x26, 0x26, 0x26, 0x66, 0x46, 0x06, 0x06, 0x06, 0x06, 0x06, 0x06, 0x06, 0x26, 0x26, 0x26, 0x66, 0x46, 0x06, 0x06, 0x06, 0x06, 0x06, 0x06, 0x06, 0x26, 0x26, 0x26, 0x26, 0x66, 0x46, 0x06, 0x06, 0x06, 0x06, 0x06, 0x06, 0x06, 0x06, 0x26, 0x06, 0x46, 0x46, 0x06, 0x06, 0x06, 0x06, 0x06, 0x06, 0x26, 0x06, 0x26, 0x26, };
int n_bits = 237;
